HrafnaValkyrja/ultrasonic/RESUME.md

# RESUME (on ice 2026-10-08 ~22:55 ET, owner: "Put Ultrasonic on ice for today.")
Branch claude/clever-mayer-s5rxuw, all session work committed + pushed (last: b92e59c + this file).
Stashes: stash@{0} = pre-session K4 scratch/render outputs parked at freeze (restore with `git stash pop` if wanted); stash@{1} = ECR-0025 dome prep (#11); older WIP below that.

## State
- Four proofs PASS (docs/proof/). D17 = A+L BUILT (owner 22:3x): limiter on, ceiling at clamp, loud mode +12 (triple press in gesture B, HOLD2 in A, off at boot), battery saver off + knob toggle. fwsim all PASS 35 rows.
- Ceiling-test restore DONE (b92e59c): lim_c scales 1/ARR; clamp-hit check covers 200/400/800 kHz, 0 hits / 1.36M hops; plm 0 stale.
- Real-use runtime (cea34fe, 130 mAh, 0.85 usable): loud12 8.1 h dense / 23.7 h dusk. loud_shape (I-034, OFF) would give 6.4 h dense -> off unless bench likes it.
- Iterative Improvement rounds 1-6 judged; ledger docs/brainstorm/LEDGER.md (to I-040). TEAX exciter dropped (12.8 g).
- Bench day kit: docs/bench/bench-day-1.md + .png, k4-dummy-template.pdf, bench/rig/ scripts (sounddevice installed).

## NEXT (movable)
1. #7 cap derating as soon as ./inbox has the Samsung files (CL03A225MP3CRNC K4-P C9, CL03A105MO3NRNC K4-M C17).
2. Ask the taste WHY for D17 (prediction C missed; she chose A+L).
3. II round 7 (new question needed; all live rows are bench-gated).
4. NEXT.md refill per the work-selection rule (movable top 5 + Waiting).

## Waiting
- #7 cap files from her (ruled A: download now) -> ./inbox.
- #1 pen test + I-029 cardboard dummy (bench day) -> pod pick.
- #11 K1-thin button: 2-arc D4 pad re-route (~1 h, stash@{0}) only if K1t still needed after #1.
- #14 bench: masked threshold, car log, I-021/22/27/28, loud_shape A/B, BCE-1 Bl.
- #4 body measure (bench day), #8 order (after freeze, owner-only).
