HrafnaValkyrja/ultrasonic/NEXT.md

# NEXT 5 (ranked, movable today; 2026-10-08 22:20 ET)
1. VIS-D17: one dark PNG for #2 (A+L rec): A / A+L / A+X+L / B side by side: who hears what where, battery, mass. So her tap is by sight. ~30 min.
2. BENCH-ENV: add sounddevice (MIT) + libportaudio2 to tools/setup.sh; install; dry-run bench/rig/* live device listing. ~20 min.
3. PERF-GATE: hook sim/perf/port_meadow.py into the check suite as an opt-in slow check (run on fw changes), document in tools/README. ~30 min.
4. II round 6: radical/rabbit on louder-without-mass (pad geometry, coupling stiffness, drive waveform), mass ≤3 g as a hard rule. ~1 h.
5. Ledger/NEXT hygiene after each round; plm status clean.
Done tonight: PERF-PM c16ecf8, reconciled currents cea34fe, FW-HOLD2 f0f4abb, triple press b99bc4a, BENCH-RIG 95ce40d, ECR-0026 draft (not recommended) 6f96833/9ed8b1a, thermal row 8 5be4ca1, light-driver search 9ed8b1a (none fits).

## Waiting (blocked on her or the bench)
- #2 D17 ruling (Rec A+L) -> limiter + loud_db defaults, re-bless goldens.
- #1 pen test + I-029 cardboard dummy (bench day) -> pod pick.
- #11 K1-thin button: 2-arc D4 pad (~1 h, stash@{0}) only if K1t still needed after #1.
- #14 bench: masked threshold, car log, I-021/22/27/28, BCE-1 Bl (I-014).
- #4-#8 owner rulings (Rec blocks posted).
