HrafnaValkyrja/ultrasonic/docs/system/integration-map.md

# Integration map: the pod as one system (generated)

Generated by `hw/pod/system_map.py` from the SKiDL schematic (`hw/pod/gen.py`, package set mz2: design phase2 in `hw/current.yaml`) plus hand-kept facts. Do not edit by hand; regenerate. Part of the living big-picture set (`docs/system/README.md`). The block diagram is `docs/diagrams/schematic-rev1.png`.

**Use:** before proposing any change, walk it through every section. The required cross-check is at the end.

> 2026-10-07 (round 10, packet Q1): dims_r2.py / heel.py / dock_route.py / shell_r2.py / blade.py now take a NON-DEFAULT variant (ULTRASONIC_DESIGN=k1|k1p via hw/current.yaml blocks + hw/mech/dims.py). Phase-2 values are byte-identical (74-name dims snapshot; shell, heel, dock_route, board_in_pod, mass and interfaces outputs unchanged apart from new info fields). K1 facts: reg-pod-body.md Variants.
> 2026-10-08: hw/current.yaml gained a NON-DEFAULT `k4` block (shell_dims dims_k4.py, shell_out hw/mech/out/k4s; ULTRASONIC_DESIGN=k4) so sim/checks/pod_mass.py can select the K4 pod (mass, CoM, nose/ear split; sim/out/mech/pod_mass_k4.json). The default design (phase2) and every other tool are unchanged. 2026-10-08 (56cf4fd, N-K4-TOOLS): the `k4` block gained board_p / netlist_p / bom_p (P board) and shell_out now `hw/mech/out/k4s_lift` (K4_RELIEF=lift default, ECR-0024); board/netlist/bom keys point at K4 board M, the *_p keys at P; tools default via tools/current.py. 2026-10-08 shell: cell modelled sharp (bought part); cavity y0/z1 edge R0.25 + 0.2 relief in the strut fill clear the cell corner (shell_k4.py, dims_k4 CELL_RELIEF_R). 2026-10-08 (b2fa6ae): each design block gained `cell` (phase2 PH2_175, k4/k1t K1_130 = fw/variants.yaml cells); interfaces.py rails reads it and judges the clamped bridge peak (FWSIM-R64).

> 2026-10-07 round 11 (NON-DEFAULT, packet Q1/Q2): K1 duct options (K1_DUCT, sim/acoustics/duct_options.py), k1t (walls/lid 0.6), 0.6 wall coupon (hw/mech/coupon_wall06.py). Phase 2 unchanged (dims snapshot: only new names REAR_GAP; shell checks add info fields puck_feasible / puck_guide_bore / pocket_breaks_outer_face). Facts: reg-pod-body.md Variants.

## 1. Functions (what the pod must keep doing)

| Function | Blocks | Electrical chain (nets / pins) | Mechanical counterpart | Firmware counterpart |
|---|---|---|---|---|
| F1 Hear 20-85 kHz | MIC, MCU | MIC_VDD from PA5 (GPIO-switched supply, off in Off mode); MIC_CLK PB3 -> R2 33R -> U2; MIC_DATA U2 -> PB4 (ADF1) | mic U2 on B at board (2.65, 6.0), its 0.6 mm port at (1.88, 6.0) through the board (pod x 32.43); sealed duct ID 1.0 (reamed lid bore + D1.0 hole in the 0.25 VHB across the 0.30 F gap), hex-window mesh seat, on the pod centre line | ADF1 4 MHz PDM, algorithm A/B |
| F2 Process | MCU, CORE_SMPS, CLOCK | +3V0 -> VDD/VDDA/VDDSMPS; VLXSMPS -> L1 -> VDD11 (C8/C9); LSE Y1 on PC14/PC15 | - | MSI/PLL clocks, LSE (see A3-clock doc), Stop 2 / Off modes (D12) |
| F3 Drive the exciter | BRIDGE, ARM_PADS | TIM1 CH1/CH1N PA8/PA7 -> Q1 gates (GA_P/GA_N); CH3/CH3N PA10/PB15 -> Q2 (GB_P/GB_N; Rev F, ECR-0003); P sources on +3V0, N sources on BRIDGE_RTN; OUT_A/OUT_B -> J1/J2 | 2 litz wires up the NiTi arm (rear-side route, heel channel, strut bore) to the exciter in the pad | complementary PWM ~200 kHz with dead time; level/volume control |
| F4 Self-test exciter |Z| | SELFTEST, BRIDGE | BRIDGE_RTN -> R21 0.1R -> GND; BRIDGE_RTN -> R22 1k -> I_SENSE (C22 10n; R23 1M offset from +3V0, Phase 2 2026-10-07) -> PA6 ADC1_IN11 | - | tone sweep + synchronous detection over USB self-test (O15) |
| F5 Charge the cell | DOCK_USB, CHARGER, CELL_PADS | dock J3 DOCK_VBUS -> D4 -> VBUS -> U3 IN; U3 BAT -> VBAT -> J5 (cell +) / J4 shared GND (cell -) -> cell (PCM inside); config over I2C | magnetic 5-pin target in the belly bay, wired to J3/J4/J10/J11/J12; cell on 0.25 VHB in the tub, 1.4 mm under the board's B face | I2C charge current/JEITA setup, charge state |
| F6 Temperature-safe charge | CHARGER | TS: RT1 (on board) OR J9 cell NTC, never both -> U3 TS/MR; TS also -> PA2 | optional NTC taped on the cell, wire to J9 | firmware 20 C rule reads PA2 |
| F7 System power rail | CHARGER, LDO | U3 SYS -> VSYS -> U4 IN/EN -> LDO_OUT (C18) -> R20 0R -> +3V0 | - | - |
| F8 Battery level | VBAT_SENSE | VBAT -> R8 1M / R9 1M (C19) -> VBAT_SENSE -> PA4 (ADC4 works in Stop 2) | - | fuel estimate, low-battery cutoff |
| F9 Dock detect | DOCK_USB | VBUS -> R12/R13 100k/100k -> VBUS_SENSE -> PA1 | - | DFU entry, charge mode |
| F10 USB data / DFU | DOCK_USB, MCU | J10 D+ / J11 D- -> U6 ESD -> PA12/PA11 (USB FS); CC: J12 -> R18 5k1 Rd (CC not sensed since Rev F; ILIM by enumeration) | dock contacts D+/D-/CC | ROM DFU via boot stub, CDC self-test, firmware update |
| F11 Wake / button | UI, MCU | SW1 (3V0 <-> BTN) -> PA0 WKUP1, R10 2k2 pull-down (switch needs >= 1 mA) | SW1 on F at board (18.5, 6.0) in a 4.3 x 3.1 lid pocket under a printed puck (selective-fit length) + silicone skin, KMT0 travel 0.15 mm | wake from Off/Stop, on/off, modes |
| F12 Power LED (solid) | UI, ARM_PADS | VSYS -> R14 2k2 -> LED_A -> J7 -> wire -> LED in the pad housing -> wire -> J8 -> LED_K -> PB7 (open-drain, FT) | 2 more litz wires up the arm (4 total), LED on the tiny pad board (O8) | duty set from VBAT for steady brightness |
| F13 Charger link | CHARGER, MCU | I2C_SCL PB13, I2C_SDA PB14 (R15/R16 10k to 3V0); CHG_INT -> PA15 (internal pull-up; PB5 strapped to GND, ECR-0013 S1) | - | I2C2, charger IRQ |
| F14 Debug / flash / test | DEBUG, MCU | TP1 SWDIO PA13, TP2 SWCLK PA14, TP3 NRST, TP4 3V0, TP5 GND, TP6 VSYS; BOOT0 (PH3) R1 10k low (R1 pad = DFU tack point); TP7 PB6 USART1_TX printf; TP8/TP9/TP10 MDF mic fallback dots; PA10 pulled up by the ROM loader itself (bootloader USART1_RX) | TP1-TP6 bare 0.7 mm pads on F (TP1/2/4/5 at y 11.3, TP3 (9.3, 2.9), TP6 (24.0, 10.9)) in a VHB cut-out: reachable before the lid is bonded; snap-off test frame (O9) | SWD, ROM bootloader |
| F15 ESD at exposed contacts | DOCK_USB | D5 TPD1E10B06 at J3 DOCK_VBUS (bidirectional, 5.5 V working; D4 reverse block); D6 (same part) at J12 CC (Rev G); U6 on D+/D- | dock contacts are the only exposed metal | - |

## 2. Blocks (every placed or copper-only part)

| Block | Parts |
|---|---|
| MCU | U1 C1 C2 C3 C4 C5 C6 C7 C10 R1 |
| CORE_SMPS | L1 C8 C9 |
| CLOCK | Y1 C11 C12 |
| MIC | U2 R2 C13 |
| BRIDGE | Q1 Q2 R3 R4 R5 R6 C14 |
| SELFTEST | R21 R22 C22 |
| ARM_PADS | J1 J2 J7 J8 |
| DOCK_USB | J3 J4 J10 J11 J12 D4 D5 D6 U6 R18 R12 R13 C15 |
| CHARGER | U3 C16 C21 RT1 J9 R15 R16 |
| CELL_PADS | J5 |
| VBAT_SENSE | R8 R9 C19 |
| LDO | U4 C17 C18 R20 |
| UI | SW1 R10 R14 |
| DEBUG | TP1 TP2 TP3 TP4 TP5 TP6 TP7 TP8 TP9 TP10 |

## 3. Inter-block nets (the logical connections a domain change can break)

| Net | Blocks | Pins (ref.pin name) |
|---|---|---|
| +3V0 | BRIDGE, CHARGER, DEBUG, LDO, MCU, UI | U1.1 VBAT, U1.9 VDDA, U1.21 VDDSMPS, U1.25 VDD, U1.36 VDD, U1.48 VDD, C1.1 , C2.1 , C3.1 , C4.1 , C5.1 , C6.1 , C7.1 , Q1.4 S_P, R3.2 , Q2.4 S_P, R5.2 , C14.1 , R15.2 , R16.2 , R20.2 , SW1.1 1, SW1.2 2, TP4.1 1 |
| BRIDGE_RTN | BRIDGE, SELFTEST | Q1.1 S_N, Q2.1 S_N, R21.1 , R22.1  |
| BTN | MCU, UI | U1.10 PA0, SW1.3 3, SW1.4 4, R10.1  |
| CHG_INT | CHARGER, MCU | U1.38 PA15, U3.A1 /INT |
| DBG_TX | DEBUG, MCU | U1.42 PB6, TP7.1 1 |
| GA_N | BRIDGE, MCU | U1.17 PA7, Q1.2 G_N, R4.1  |
| GA_P | BRIDGE, MCU | U1.29 PA8, Q1.5 G_P, R3.1  |
| GB_N | BRIDGE, MCU | U1.28 PB15, Q2.2 G_N, R6.1  |
| GB_P | BRIDGE, MCU | U1.31 PA10, Q2.5 G_P, R5.1  |
| GND | all | 47 pins |
| I2C_SCL | CHARGER, MCU | U1.26 PB13, U3.B1 SCL, R15.1  |
| I2C_SDA | CHARGER, MCU | U1.27 PB14, U3.C1 SDA, R16.1  |
| I_SENSE | MCU, SELFTEST | U1.16 PA6, R22.2 , C22.1, R23.2 (Phase 2)  |
| LED_A | ARM_PADS, UI | R14.2 , J7.1 1 |
| LED_K | ARM_PADS, MCU | U1.43 PB7, J8.1 1 |
| LSE_IN | CLOCK, MCU | U1.3 PC14, Y1.1 1, C11.1  |
| LSE_OUT | CLOCK, MCU | U1.4 PC15, Y1.2 2, C12.1  |
| MDF_CCK | DEBUG, MCU | U1.45 PB8, TP8.1 1 |
| MDF_SDI | DEBUG, MCU | U1.19 PB1, TP9.1 1 |
| MIC_DATA | DEBUG, MCU, MIC | U1.40 PB4, U2.1 DATA, TP10.1 1 |
| MIC_VDD | MCU, MIC | U1.15 PA5, U2.5 VDD, C13.1  |
| N$2 | MCU, MIC | U1.39 PB3, R2.1  |
| NRST | DEBUG, MCU | U1.7 NRST, C10.1 , TP3.1 1 |
| OUT_A | ARM_PADS, BRIDGE | Q1.3 D_P, Q1.6 D_N, Q1.7 D_N, Q1.8 D_P, J1.1 1 |
| OUT_B | ARM_PADS, BRIDGE | Q2.3 D_P, Q2.6 D_N, Q2.7 D_N, Q2.8 D_P, J2.1 1 |
| SWCLK | DEBUG, MCU | U1.37 PA14, TP2.1 1 |
| SWDIO | DEBUG, MCU | U1.34 PA13, TP1.1 1 |
| TS | CHARGER, MCU | U1.12 PA2, U3.D1 TS/MR, J9.1 1, RT1.1  |
| USB_DM | DOCK_USB, MCU | U1.32 PA11, J11.1 1, U6.5 IO2 |
| USB_DP | DOCK_USB, MCU | U1.33 PA12, J10.1 1, U6.3 IO1 |
| VBAT | CELL_PADS, CHARGER, VBAT_SENSE | U3.C2 BAT, C16.1 , J5.1 1, R8.1  |
| VBAT_SENSE | MCU, VBAT_SENSE | U1.14 PA4, R8.2 , R9.1 , C19.1  |
| VBUS | CHARGER, DOCK_USB | D4.1 K, U3.A2 IN, C15.1 , R12.1  |
| VBUS_SENSE | DOCK_USB, MCU | U1.11 PA1, R12.2 , R13.1  |
| VDD11 | CORE_SMPS, MCU | U1.23 VDD11, U1.46 VDD11, L1.2 2, C8.1 , C9.1  |
| VLXSMPS | CORE_SMPS, MCU | U1.20 VLXSMPS, L1.1 1 |
| VSYS | CHARGER, DEBUG, LDO, UI | U3.B2 SYS, C21.1 , U4.3 EN, U4.4 IN, C17.1 , R14.1 , TP6.1 1 |

Nets inside one block only: CC, DOCK_VBUS, LDO_OUT, MIC_CLK, N$1

## 4. MCU pin map (STM32U575CIU6Q, QFN48)

| Pin | Name | Net | Other end |
|---|---|---|---|
| 1 | VBAT | +3V0 | (rail) |
| 3 | PC14 | LSE_IN | C11, Y1 |
| 4 | PC15 | LSE_OUT | C12, Y1 |
| 7 | NRST | NRST | C10, TP3 |
| 8 | VSSA | GND | (rail) |
| 9 | VDDA | +3V0 | (rail) |
| 10 | PA0 | BTN | R10, SW1 |
| 11 | PA1 | VBUS_SENSE | R12, R13 |
| 12 | PA2 | TS | J9, RT1, U3 |
| 14 | PA4 | VBAT_SENSE | C19, R8, R9 |
| 15 | PA5 | MIC_VDD | C13, U2 |
| 16 | PA6 | I_SENSE | C22, R22, R23 (Phase 2) |
| 17 | PA7 | GA_N | Q1, R4 |
| 19 | PB1 | MDF_SDI | TP9 |
| 20 | VLXSMPS | VLXSMPS | L1 |
| 21 | VDDSMPS | +3V0 | (rail) |
| 22 | VSSSMPS | GND | (rail) |
| 23 | VDD11 | VDD11 | C8, C9, L1 |
| 24 | VSS | GND | (rail) |
| 25 | VDD | +3V0 | (rail) |
| 26 | PB13 | I2C_SCL | R15, U3 |
| 27 | PB14 | I2C_SDA | R16, U3 |
| 28 | PB15 | GB_N | Q2, R6 |
| 29 | PA8 | GA_P | Q1, R3 |
| 31 | PA10 | GB_P | Q2, R5 |
| 32 | PA11 | USB_DM | J11, U6 |
| 33 | PA12 | USB_DP | J10, U6 |
| 34 | PA13 | SWDIO | TP1 |
| 35 | VSS | GND | (rail) |
| 36 | VDD | +3V0 | (rail) |
| 37 | PA14 | SWCLK | TP2 |
| 38 | PA15 | CHG_INT | U3 |
| 39 | PB3 | N$2 | R2 |
| 40 | PB4 | MIC_DATA | TP10, U2 |
| 41 | PB5 | GND | (rail) |
| 42 | PB6 | DBG_TX | TP7 |
| 43 | PB7 | LED_K | J8 |
| 44 | PH3 | N$1 | R1 |
| 45 | PB8 | MDF_CCK | TP8 |
| 46 | VDD11 | VDD11 | C8, C9, L1 |
| 47 | VSS | GND | (rail) |
| 48 | VDD | +3V0 | (rail) |
| 49 | VSS | GND | (rail) |

**Free MCU pins:** 2 PC13, 5 PH0, 6 PH1, 13 PA3, 18 PB0, 30 PA9

## 5. Rails and loads

| Rail | Source and loads |
|---|---|
| +3V0 | source: U4 LDO via R20 (TPS7A2030, 300 mA rated, ICL 360 mA min). Loads: MCU ~2.4-5.8 mA run; mic ~0.9-1.1 mA via PA5; bridge P sources: avg 0.6-1.7 mA at listening level but ~315 mA peaks at full drive (8R + 1.2R FETs) buffered by C14 22 uF; pull-ups R15/R16; SW1 contact (>= 1 mA while pressed). |
| VSYS | source: U3 SYS (power path: VBUS when docked, else VBAT through the BATFET). Loads: U4 LDO input, R14 LED (~0.35-0.75 mA), TP6. |
| VBAT | cell (Renata ICP501233PA-02 175 mAh, 3.0-4.2 V, PCM inside) <-> U3 BAT. Loads: R8/R9 divider (2 uA), C16. |
| VBUS | dock 5 V via D4 Schottky (reverse-dock block). Loads: U3 IN, R12/R13 sense, C15 (25 V). DOCK_VBUS side: D5 ESD. |
| VDD11 | MCU's own SMPS output via L1; MCU core only (D11 allows this switching regulator only). |
| BRIDGE_RTN | bridge N-FET sources -> R21 0.1R shunt -> GND (31 mV at 315 mA). |

## 6. Off-board interfaces

| Pads | Nets | Goes to |
|---|---|---|
| J1 / J2 | OUT_A / OUT_B | litz wire up the arm -> bone-conduction exciter RC-BC02 (8 or 12 ohm) in the pad |
| J7 / J8 | LED_A / LED_K | litz wire up the arm -> blue 0402 LED on the pad board |
| J3 / J4 / J10 / J11 / J12 | DOCK_VBUS / GND / USB_DP / USB_DM / CC | Xinyangze YZT0675 5-pin magnetic target in the belly bay (pogo YZP0048 on the cable) |
| J5 / J4 | VBAT / GND (J4 shared with dock GND, between J3 and J5) | cell leads (PCM inside the cell) |
| J9 | TS | optional NTC taped on the cell (then RT1 not fitted) |
| TP1-TP6 | SWDIO, SWCLK, NRST, +3V0, GND, VSYS | probe / pogo only |

## 7. Mechanical interfaces and keep-outs

- Board 30 x 12 x 0.8 mm (R1.0 corners), 4 layers (In1 GND plane, In2 +3V0 plane); every part on B except SW1 and bare TP1-TP6 on F; pod x 30.55-60.55 (hw/mech/dims_r2.py).
- F faces the lid (outside); B faces the cell. Height bands: B 1.4 (gap to the cell), F 0.30 (VHB gap to the lid), SW1 0.90 in its lid pocket.
- Mic MUST be on B with its D0.6 port hole on the board centre line y 6.0 (board 1.88 = pod 32.43): sealed duct ID 1.0 (reamed lid bore + VHB hole) onto it; same spot on both pods (O16-5).
- Switch MUST be on F at board (18.5, 6.0), inside the 4.3 x 3.1 lid pocket under the puck + skin: changing the button changes the lid.
- The board hangs from the lid on full-face VHB (3M 4914, 0.25 mm): nothing presses its long edges; coarse x-stop 0.25 mm at the front skirt; a stepped gauge pin through the bore registers it at bonding. F parts only in VHB cut-outs.
- Wire pads J* on B at the rear (board x 25-30); the arm wires reach them through the stowage gap behind the board (pod x 60.55-66.7) from the heel exit.
- Dock target sits in the belly bay (pod x 31.5-52.7), wired to J3/J4/J10/J11/J12; the whole belly is tub.
- Cell 35 x 12 x 5.3 mm on 0.25 VHB in the tub, 1.4 mm under the board's B face (tallest B part U2 1.08 mm).
- Arm: 4 litz wires (2 exciter + 2 LED) in shrink tube through heel channel D1.0 and strut bore D1.2: the wire count sets those bores.

## 8. Firmware dependencies

- TIM1 complementary PWM with dead time on PA8/PA7/PA9/PB0 (bridge).
- ADF1 (audio digital filter) on PB3 clock / PB4 data, 4 MHz PDM; PA5 is the mic's supply pin.
- ADC: PA4 VBAT (ADC4, works in Stop 2), PA1 VBUS sense, PA2 TS, PA6 bridge current (PA3 spare since Rev F).
- I2C2 on PB13/PB14 to the charger, EXTI on PA15 (CHG_INT).
- USB FS on PA11/PA12 (HSI48 + CRS), ROM DFU (the ROM loader pulls PA10 up itself, AN2606 Table 199); PB6 USART1_TX debug printf (TP7).
- Wake: PA0 = WKUP1 (button). LED: PB7 open-drain, PWM duty set from VBAT.
- Knob `loud_shape`/`loud_shape_k` (I-034 flat-top inside loud mode; default off, bit-identical; fw/core/dsp.c only, no new interface). Knobs `loud_db` (D17 loud mode, toggled by the HOLD2 gesture in option A only in practice; default off) and `hiz_idle` (bridge Hi-Z while squelched, I-027; default off): both default to legacy behaviour, bit-identical; touch F3 (drive, limiter, R64 clamp) and F11 (gestures). Tests `fw/test/test_loud.c`.
- SWD on PA13/PA14. Low-power modes Stop 2 / Off (D12).

## 9. Constraints and owner decisions

- Spec section 1 (MVP) is owner-locked.
- D11: switching regulators ONLY the MCU core SMPS; self-noise no louder than ambient.
- Power budget ~5-8.5 mA total (algorithm A) / 7.5-10.5 mA (B); runtime targets in spec.
- O8 power LED in the pad housing, solid. O9 rev 1 IS the prototype (test pads + snap-off frame).
- O12 magnetic USB dock (charge + DFU), IPX4 min / IPX5 preferred, outdoor wear in light rain, fast charge.
- O16: Renata 175 mAh cell, BQ25180 charger, pre-built magnetic connector, one board for both pods, no screws in the housing, IP68 switch.
- Owner rule for this study: one expensive component beats five half-price ones.

## 11. K4 two-board split (ECR-0020, proposed; NOT the current design until adopted)

Netlists (rev 3, area re-balance 2026-10-08): hw/pod/k4/gen.py -> pod_k4_M.net (23 placed parts), pod_k4_P.net (31); ERC 0 errors both. Board M (lower, mic on its outer face): U2/C13, charger U3 block, LDO U4 block (+R20), dock D4/D5/U6 + own gold pads J3/J4/J10/J11 + 2 magnets, SW1/R10, VBUS/VBAT dividers, RT1/J9, R14/J7/J8, J5, TP6, J20 BM28 receptacle. Board P (upper, over the mic): U1 + caps, Y1, L1/C7/C8/C9, R1/R2, R15/R16, bridge Q1/Q2 + shunt + C14, J1/J2, TP1-TP5/TP7-TP10, J21 BM28 plug. J12/R18/D6 and net CC are gone (ECR-0019).

| BM28 pin | Net | BM28 pin | Net | BM28 pin | Net |
|---|---|---|---|---|---|
| 1 | GND | 11 | USB_DP | 21 | GND |
| 2 | GND | 12 | GND | 22 | TS |
| 3 | MIC_CLK | 13 | USB_DM | 23 | I2C_SCL |
| 4 | GND | 14 | GND | 24 | GND |
| 5 | GND | 15 | GND | 25 | I2C_SDA |
| 6 | MIC_VDD | 16 | GND | 26 | VBUS_SENSE |
| 7 | MIC_DATA | 17 | +3V0 | 27 | CHG_INT |
| 8 | GND | 18 | +3V0 | 28 | VBAT_SENSE |
| 9 | GND | 19 | +3V0 | 29 | BTN |
| 10 | GND | 20 | GND | 30 | LED_K |

30 contacts = 16 signal/power + 14 GND (odd pins row A, even row B [T]). Parts: P plug C424570 BM28B0.6-30DP/2-0.35V(51), M receptacle C424571 BM28B0.6-30DS/2-0.35V(51), JLC 2026-10-08. Rating 0.3 A per signal contact [T, secondary source]; +3V0 (LDO on M to P) uses 3 contacts, the 315 mA bridge peaks are served by C14/C4/C7 on P. No VLXSMPS, VDD11 or bridge node crosses. Mated height 0.6 mm [T].

K4 dock (ECR-0021, proposed; docs/research/k4-dock.yaml option_A_design, 2026-10-08): J3 / J11 / J10 / J4 are 4 castellated ENIG pads (pitch 2.5) on the 0.8 mm tab of board M, seen through 4 belly windows, with 2 N52 D2.5 x 1.0 magnets in bossed belly pockets; they replace the YZT0675 target (J3/J4/J10/J11 wired). Head YZP0048-20048-04025-03 (C5126845). Nets and D4/D5/U6 unchanged; pod L 49.15 -> 50.65. Magnet pitch, polarity and stroke of the head are [T] until a sample is calipered.

## 10. Required cross-check for every proposed change

Every proposed change must state, and check against the sections above:
1. functions_affected: which F-rows change, and the NEW implementation chain for each (no function may be left without one; say explicitly if a function is dropped and that it needs an owner decision).
2. nets_changed: nets removed, added or re-driven; every remaining net still has exactly one driver and its loads.
3. pins: MCU pins freed and pins newly needed, with the alternate function used; no pin may end up with two jobs (check the pin map, including other domains' proposals).
4. rails: load change per rail (mA avg and peak) vs its source's rating; new rails need a source that respects D11.
5. offboard: changes to J pads, wire counts up the arm, dock contacts, cell wiring.
6. mechanical: which face each moved/added part is on, height band, keep-outs (mic port, switch/plunger, clamp bands, wire path), lid/shell features that must change.
7. firmware: peripherals/features added, removed or re-pinned.
8. depends_on / conflicts_with: other domains' changes this one needs or excludes.
