HrafnaValkyrja/ultrasonic/docs/brainstorm/LEDGER.md

# Brainstorm ledger (Iterative Improvement mode; process: ~/.claude-shared/board/howto/ITERATIVE-IMPROVEMENT.md)
Owner's plan 2026-10-08. One row per idea; the judge pass re-ranks each cycle and kills weak ones with a reason. Merit = evidence or a calculation + moves a spec metric meaningfully (or removes a hard build step or a risk) + a stated cost. Rows with merit go to the owner as a packet (recommendation first, "let's talk" option). Nothing is ordered; changes to the committed design go through her.

Tracks: D = deeper (main), R = rabbit trail (research swarm), X = step back (informed radical), B = blind designer (requirements brief only: BRIEF-blind.md).
Metrics (spec): thickness T, height H, length L, worn mass, vision clearance, runtime h, charge time, loudness margin (dB over ambient+12.5), mic noise margin dB, build difficulty (max step), build hours, part count, cost, risk.

| ID | Track | Idea | Metric moved (est.) | Evidence / calc | Cost + risk | Rank | Status | Judge note |
|---|---|---|---|---|---|---|---|---|
| I-001 | D | Playback limiter at the R64 clamp (lim_lookahead) + system sounds at 2-3 kHz (alert_hz); the limiter is the playback lever | alert margin +4.5 dB (quiet +6.1->+10.6, office -8.9->-4.4, street -28.9->-24.4; p05) | loudness.md before/after, fbfb38b | free; limiter raises max output past the -12 dBFS D17 ceiling: needs owner re-sign of D17 + golden re-bless | 1 | built, limiter OFF pending owner (D17) | - |
| I-002 | D | Pad stiffness / exciter resonance at 2-3 kHz | loudness +4-10 dB | loudness.md levers; needs E1/E2 | bench time, pad parts | - | bench day | - |
| I-003 | B | B-thin "single-deck slab": cell and board side by side in one layer, cell sets thickness | T 6.4 -> 4.3 mm (-2.1, -33%; sum 0.5+3.0+0.3+0.5 checks); mass ~6.5 g (checks) | B-thin calc; ALL part facts "from memory" [v]. Cell 1.575 cm3 x 83 = 131 mAh checks. L 58 mm from X=30 ends at 88: **fails the ~38 mm usable length by 20 mm**. In 38 mm the cell is ~21 mm = ~78 mAh -> worst day 6.4 h at their 11 mA (8.4 h only if the MCU error below is fixed): misses 8 h unless H grows (O34b). Error: MCU 30% x 96 MHz x 10 uA/MHz = 0.29 mA, not 2.9 mA | Thin win is real in principle; needs a 38 mm re-size (H up, cell shorter), 0.5 mm printed walls, 2 mm exciter unverified; rigid-flex vendor unverified | 3 | killed at 38 mm | D-slab38.md: T 4.3 x H 15.25 x L 38 leaves 13 mm for the cell = ~43 mAh, 3.1 h worst (8 h needs 113 mAh) and cannot source the 315 mA peak |
| I-004 | B+X | Single rigid-flex board (island + flex tail, cell as mandrel); removes BM28 pair, step 3/4 wires and step 9 cell-lead fold | build: -45 min of 5.6 h (~-13%), 2 hard steps gone, ~1 connector gap gone [A] | X-arch #3 and B-thin both reach it independently. JLC rigid-flex stack-up (min thickness, bend radius) NOT checked by either; 4L 0.8 mm is published only for rigid | rigid-flex 5-10x FR4 cost [A] (irrelevant, O19); redo layout (weeks), discards K4 DRC-0 work | 2 | killed at JLC | D-rigidflex.md aeb469c: JLC flex page 2026-10-08 "Rigid-flex PCBs are not yet supported"; flex 1/2/4L, bend 6-10x t; 0.6 mm fold only with a 1-layer tail. Reopen only if the owner accepts another fab |
| I-005 | B | One-chip charger+LDO+battery gauge link (TI BQ25155, 150 mA LDO) to cut parts | part count fewer lines | "[v]" from memory. Its 150 mA LDO is below the 208 mA bridge clamp and the 300 mA LDO figure in loudness.md | needs burst cap or second LDO; unverified datasheet | - | killed | D-onechip.md 9d50882: BQ25155 LDO 150 mA / BQ25120A 100 mA (+buck, D11) < ~219 mA needed; saves ~6 parts but +1.4 mm2; keep U3+U4 |
| I-006 | B | Loud exciter: tragus pad, 6 ohm coil, 0.34 A rms, "+15.5 dB over a 70 dBA street" | loudness claim +15.5 dB over street | Arithmetic internally consistent but drives 0.34 A rms (~0.48 A peak) vs the 208 mA R64 clamp (147 mA rms) and the LDO 300 mA limit; Bl 0.6 is [A]; 10 dB tragus bonus; thresholds [M] | no thickness gain (6.5 vs 6.4) | - | killed (as a loudness claim) | Re-run with the clamp: 78.2 dB-eq by its own method = -3.8 dB under its 82 target; with loudness.md thresholds, ~-4 to -15 dB. See loudness conflict in the judge log |
| I-007 | B | Piezo bender exciter with boost converter (fallback) | same force at ~1/10 current | needs 15-60 V boost | breaks D11 | - | killed (D11) unless owner relaxes D11 | R-exciter reached the same verdict |
| I-008 | B | Dose-based ceiling: <=80 dB-eq continuous, alerts <=88 dB-eq, <=0.5 s, <=60/h | safety policy, no metric | NIOSH 98-126 figures "from memory" [M]; ceiling is in unmeasured dB-eq (+-8 dB) | fw only | - | needs-evidence | Tie to D17; only meaningful after E1/E2 calibrate dB-eq |
| I-009 | X | Electronics into the arm run, front = mic-only flex tail, to fix the vision line | vision deficit 11.85 mm "eliminated" | Ignores the fixed rear end: K4 spans 17.65 to 67.5; the tail and everything else still need X >= 29.5, so the whole 49.85 mm must become ~38 mm. Moving mass back does not shorten it | 40 mm flex, PDM over 40 mm risk | - | killed (arithmetic) | Real need is 11.85 mm of length, not a different layout |
| I-010 | X | Tactile cue for SYSTEM events only (2-3 pulses 150-250 Hz); not a playback fix (owner: audio device, not an alert system) | alert audibility independent of masking (street/office) | Firmware only, 0 g, 0 BOM. Force at 180 Hz vs 300 Hz: 12 dB/oct x log2(300/180) = -8.8 dB (X-arch wrote -7); first-order only; face vibrotactile threshold is [A] | 20 min owner test; may buzz jaw/teeth; D1 promises quiet | 4 | built OFF (7183a29), marginal | skin displacement 4-8 um at 208 mA vs ~2-20 um threshold (from memory): -4 dB at 200 Hz, +2 at 250; system cue only, not playback |
| I-011 | X | One cell in the frame, 2 wires through both hinges | pod -4 mm, mass -3.5 g per pod | 4-5 g on the nose pads (X-arch's own kill test: >4.0 g kills) | links the pods | - | killed (brief hard no: no wires between sides, D2) | |
| I-012 | X | k1t 4L board (8.5 mm thick) behind the hinge in the arm | clears vision by 4.2 mm | 8.5 mm thick, worst on priority 1; depends on I-009 | - | - | killed | |
| I-013 | R | Dayton BCT-3 bone transducer (Bl 4.41) | +12.9 dB (20 log 4.41 and 4.41 x 0.208 = 0.917 N = 119.2 dB both check) | Web datasheet 2020-06-11; but 44x32 mm, 6.1 g | ~7x pod footprint | - | killed (size) | Gain is relative to an assumed Bl 1.0 that implies 106 dB at 208 mA, whereas the loudness model gives 94-97 dB: ratio valid, absolute not |
| I-014 | R | Measure RC-BC02 Bl, f0, force on the E1 rig; buy one Dayton BCE-1 (Bl unpublished) and ask Sonion/Goertek for Bl | retires the assumed Bl 1.0 that the loudness proof, B-loud and R-exciter all rest on; BCE-1 gain 0 to +6 dB, no basis | R-exciter table web-checked 2026-10-08 except BCE-1 price and the Tectonic Bl (secondary) | cheap, bench only; O21 means her call; BCE-1 is 7.8 mm vs T 6.4 | 2 | merit (risk removal) | Highest information per dollar; every loudness number moves with Bl |
| I-015 | R | Vision line from perimetry norms: Goldmann temporal ~90 deg -> line 11-21 mm from hinge (pod.py 29.5 is conservative) | vision clearance: K4 may need ~0-9 mm trim, not 11.85 | R-vision.md 21d7274 (sources dated; pupil-hinge unmeasured) | none; pen test confirms | 1 | merit (evidence) | Judge r3: desk sources fine, 5 mm margin spec-derived; pupil-hinge p unmeasured moves the line more than angle (R-vision says so). Median ~15 mm line, K4 passes only ~15-20%. Real action: 10-min pen test + side photo. |
| I-016 | D | K4-trim: re-lay boards to 13.75 long + gap trims (stock cell) -> X0 ~20.0; + custom 112.5 mAh 26.8 mm cell -> X0 ~24.2 (8.0 h worst, no margin) | vision clearance +2.4 / +6.6 mm; T 6.4 kept | D-k4trim.md 1f7935a | board re-place/re-route (serial heavy job); custom cell = supplier risk | 2 | merit (conditional on the pen test) | Judge r3: arithmetic checks (112.5 mAh = 8 h x 10.55 / 0.75; 4.19 mAh/mm; stack/gap saves sum 2.3 stock, 6.5 custom). Stock-only trim to ~20 is the free step; 24.2 custom has 1.95C and zero margin, so cap at ~21 (8.9 h, 1.75C). Do after pen test.  pen-test result picks: line <=12.6 K4 as is; <=15 K4-trim; <=19 K4-trim + custom cell; else K1t |
| I-017 | B | Blind thin38: one 0.8 mm board over an EEMB LP401230 cell (90 mAh, 4.3 x 12.5 x 31), fits X 29.5-67.5 | T 7.4 vs K1t 8.5 (-1.1), vision-clear | B-thin38.md 300cc45 (cell datasheet dated; mass est.; exciter avg 6 mA assumed) | 150 mA drive cap (-3 dB vs 208 mA); 8.4 h worst rests on the exciter avg; 2C rating only on the PCM-LD variant | - | killed (as specified); T idea kept as I-018 below | Judge r3: runtime fails on our real load. B-thin38 uses 8.6 mA (no LED, exciter 6 mA assumed); our model is 10.55 mA worst (9.8 full-chain + 0.75 LED, sub-power.md). 90 mAh x 0.75 / 10.55 = 6.4 h < 8 h (needs 112.5 mAh). 150 mA cap = 0.58C of our 260 mA clamp basis, -2.8 dB vs 208 mA, violates the 208 mA drive. Single 0.8 board has one face for MCU, bridge, charger, LDO, mic: unproven (Phase-2 and K4 are two-faced / two boards). |

## Judge log (newest first)
### Round 4 judge (2026-10-08)
- Read: R-dbpermA, B-r4-playback, d17-cost.md, sub-output.md, C3-output-stage.md, spec D6. Merit: I-019 (partly confirmed). Needs-evidence: I-020, I-021, I-022, I-027. Killed/dead: I-023, I-024, I-025, I-026.
- **Ternary PWM:** our bridge is 2-level AD at 200 kHz, not ternary; BD was rejected in v0.5 for dead-time distortion. Blind's ripple-mA claim mis-counts: recirculating ripple is heat, not battery mA; SPICE idle is 0.4-0.5 mA. It would cut current only if coil L is tiny (E1 unmeasured). Details in JUDGE-r4.md.
- **Owner packet:** TEAX plus ~+6 dB drive (I-019) with scene caveat; E1 measures L, Bl, f0 (I-014, also kills/keeps I-021/I-026/I-027).
- 2026-10-08 lead: FRAME CORRECTION (owner: "It's an audio device not an alert system."). Loudness is judged as playback listening headroom over day-to-day ambient, not alert margin. I-001 reworded (the limiter is the lever), I-010 demoted to system sounds.
### Round 3 judge (2026-10-08)
- Read: R-vision, D-k4trim, B-thin38, sub-power.md, loudness.md, variants.yaml, dims_k1.py. Merit: I-015, I-016 (conditional). Killed: I-017. New: I-018 (needs-evidence).
- **I-017 key question:** our K1t cannot take a ~90 mAh cell: worst load 10.55 mA (not 8.6) gives 6.4 h; 8 h needs 112.5 mAh. EEMB LP401230 is 90 mAh min at 54 mAh/cm3 (Renata 73), so a 112.5 mAh cell at 4.3 mm does not exist in 31 mm; stock 130 mAh is 4.5 thick. 90 mAh at 2C = 180 mA, clamp 144 mA (-3.2 dB), breaks 208 mA. Real thickness: ~7.6 (0.8 walls) / ~7.2 (0.6 walls), only if a one-face layout fits (unproven); today K1t 8.5.
- **Owner packet:** 1) pen test + side photo (picks K4 / K4-trim / K1t, I-015/I-016). 2) I-016 stock-only trim to ~20 mm is free of cell risk. 3) I-018 one-face floorplan check before any further thin push.
### Round 1 judge (2026-10-08)
- Read: B-thin, B-loud, X-arch, R-exciter, loudness.md. Merit: I-010, I-014. Needs-evidence: I-003, I-004, I-005, I-008. Killed: I-006, I-007, I-009, I-011, I-012, I-013.
- **Brief check:** usable length ~38 mm (X 29.5 to 67.5, rear end fixed). B-thin 58 mm and B-loud 48 mm both overrun it; X-arch #1 misses that K4 already ends at 67.5. Thickness: only B-thin (4.3 mm) moves it. B-loud gains nothing.
- **From memory, unverified:** every B-thin [v] part fact (STM32U3 10 uA/MHz, BQ25155, SPH0641 size, 8 mm exciter 2.0 mm tall); B-loud [M] ISO 389-3 / ISO 226 / NIOSH values; all X-arch [A].
- **Arithmetic errors:** B-thin MCU current 2.9 mA should be 0.29 mA; X-arch tactile -7 dB should be -8.8 dB; B-thin "0.56 W" is the sine average, not peak.
- **Loudness conflict (B-loud +15.5 dB over street vs loudness.md -24 dB):** B-loud never saw the 208 mA R64 clamp. Differing assumptions: (1) current 0.34 A rms vs 0.147 A rms (+7.3 dB); (2) touching-tragus +10 dB vs the measured front-of-tragus threshold at D1 (1-1.5 cm in front); (3) free Bl x I force (Bl 0.6) vs the bone.py pad/mass model, which gives 94.5 dB at clamp against 106 free (about -9 to -11 dB); (4) target: B-loud is stricter (82 dB vs 71.5, broadband vs dBA-11), which narrows the gap by ~10 dB. Net: (1)+(2)+(3) is roughly 26-28 dB of the ~29 dB nominal gap (my decomposition, +-5 dB). Both rest on assumed Bl; I-014 settles it.
- **Owner packet (top, recommendation first):** 1) I-010 tactile alert test (free, 20 min). 2) I-014 measure Bl on E1, plus one BCE-1 if she allows a bench buy. Best needs-evidence: I-003/I-004 thin single-deck rigid-flex, pending a 38 mm sizing and the JLC rigid-flex table.

| I-018 | D | K1t slimmed: single board over the Renata 130 mAh 4.5 mm cell, 0.6 walls, one-face IC layout | T ~7.2-7.6 vs 8.5 (my calc: 0.6+0.6+0.8+0.1+4.5+0.6 = 7.2; 0.8 walls 7.6) | judge calc from B-thin38 stack with the real cell; 130 mAh = 9.2 h, 260 mA pulse -> 208 mA drive kept | needs a one-face layout of ~30 parts in 36 x 13: unproven; H-bridge+charger+LDO heat | - | evidence in (D-k1t-oneface.md): board already one-face (B 228 of 246 mm2, only SW1+TP1-6 on F); 7.2 omitted 1.08 mic band + tapes; real floor 8.28 (8.08 with 0.6 board) | does-not-reach-7.6 | Mic bottom-port pins the B band; I-018 as stated fails, residual -0.2..-0.4 only || I-019 | R | Buy back drive with higher Bl: TEAX + ~+4.4 dB drive instead of +12 dB | runtime 6.2 -> ~8.5-9 h at equal loudness; dense mean 14.5 -> ~8.1 mA | R-dbpermA.md #1, calc from d17-cost table | TEAX bench buy (existing plan); limiter nonlinearity ignored | - | partly-confirmed, MASS KILL for TEAX14C02-8 (12.8 g/side vs ~1.2 g RC-BC02; R-light-driver.md, 2026-10-08) | Re-run (d17-cost.md, teax_drive_check.py): worst-call margin of TEAX+4.4 = current+12 in all scenes, median +4.4 dB; dense 7.8 mA/9.1 h holds, continuous 13.8 mA/6.4 h FAILS 8 h. 8 h dense: TEAX+6 (8.4 h); continuous: TEAX+0 only. |
| I-020 | R | Shift translated-programme energy to 2-4 kHz (lowest bone/tragus threshold) | ~8-12 dB per equal audibility, or x0.3-0.4 mean mA | RECALLED ISO 389-3 values, unverified | firmware mapping; needs primary check + bench | - | KILLED 2026-10-08: 95.6% energy already in 2.5k band; mastoid RETFL gain +0.2 dB (<2). Front-tragus +7.3 dB (2.5->4k, soft, SD 6-9) spun off as I-020b bench-only. D-i020-band.md | killed |
| I-021 | R | Exciter f0 into 2-3 kHz band | +6-9 dB in band, current falls at resonance | calc, assumed Q 2-3 | narrow, drifts with pad/skin; needs impedance sweep (I-014 rig) | - | needs-evidence | |
| I-022 | R | Tragus pad static force/area up | +2-4 dB (recalled) at 0 mA | RECALLED, unverified | comfort cap ~1-2 N; bench force sweep | - | needs-evidence | |
| I-023 | R | Programme-aware compression for mA | ~0.9 dB at best; compression raises mean current | calc | - | - | dead | no dB/mA; AGC on quiet calls only matters for the clamp |
| I-024 | R | Class-D / bridge / rail efficiency | 0 dB per battery mA (F = Bl x I, LDO 1:1); heat only; idle <1 mA | calc, identity in R-dbpermA.md | - | - | dead | does not move runtime-vs-loudness |
| I-025 | B | Blind r4 playback pod: 150 mAh cell in 3.2 x 14 x 27.5 mm, pod 4.9 x 27 x 30, 6.2 g, 12.7 h aged | T 4.9, 6.2 g, 12.7 h | B-r4-playback.md; every [R] unverified | cell energy density 450 Wh/L assumed vs 54-73 mAh/cm3 (about 200-270 Wh/L) found in r3 (EEMB/Renata): 150 mAh needs ~2-2.8 cm3, not 1.23; load 8.05 mA omits our 4.6-7.3 mA base; S=90 dB/W unsourced | - | killed (as specified) | 150 mAh at 1.23 cm3 is 2x denser than any stocked cell; kept as the S-gate idea (I-014 measures it) |
| I-026 | B | Ternary (3-level, BD) PWM 192 kHz + 33 uH per leg to remove idle ripple (claims 25-40 mA at idle) | idle ripple 3 mA vs 25-40 | spec D6/C3-output-stage.md: BD was v0.3/v0.4 and REJECTED in v0.5; bridge_spice.py idle bus current 0.49/0.42 mA (0.3/1.26 mH) | blind's ripple cost is wrong: ripple recirculates in L, battery pays only ~I_rms^2 R (tens of uW at 0.3 mH); only true if coil L is ~20 uH (unmeasured, E1). BD dead-time THD+N -10 dB at -40 dBFS (C3) | - | killed (reason: already analysed and rejected; our AD idle cost 0.4-0.5 mA) | Residual: if E1 measures L < ~0.1 mH, idle cost rises (20 uH: ~8 mA by calc) and a hybrid (BD only above -20 dBFS, or L in series) is worth a rerun. Kill test: E1 LCR meter L; deadtime_switching.py at that L |
| I-027 | B | Bridge Hi-Z (both legs off) when envelope under the noise gate | saves idle 0.4-0.5 mA (bridge_spice) in quiet scenes | calc; our idle number is from sim, not bench | firmware gate hysteresis; re-start click; AD zero-cross cancels dead-time error only while switching | - | SPICE ok: 0.42-0.49 mA at 1 tick, ~0.1-0.2 at 2 ticks; knob hiz_idle (default OFF) landed; D-hiz-idle.md | needs-evidence | Kill test: bench PWR-I12 idle bus current with real coil; if < 0.15 mA, drop |
| I-028 | R | Move playback centre 2.5 -> 4 kHz for ~+7 dB at tragus (Surendran, I-020b) | +7 dB claimed | R-tragus4k.md; Nishimura 2014/2015 (PubMed, doi 10.1002/lary.24485, 10.1016/j.anl.2014.08.001) | at 4 kHz open-ear CC is mostly airborne radiation (fit-dependent, bystander leak); numeric tables not retrieved; SD 6-9 dB; transducer response at 4 kHz unknown | - | needs-evidence | gain range 0 to +7 dB, not firm; bat-call naturalness ok (retune LO/mapping). Kill test: bench sweep at tragus force + canal mic, kill if < 2 dB net |
| I-029 | X | Slide whole K4 pod rearward over the ear helix: X0 17.65 -> 30.0, heel lead 12-15 mm litz | front X 30.0 vs 17.65; T 6.4, 9.2 h unchanged | calc from dims_k4 + R-vision; X-r5-vision.md | needs 79 mm straight arm (assumed); helix contact; CoG +20 % moment | - | needs-evidence | kill: cardboard block 30 min on her frame |
| I-030 | X | Cell forward, stack (P+M) behind the ear, mic flex tail | front X ~33; 9.2 h; nose -0.5 g | calc; X-r5-vision.md | flex PDM SNR, mastoid comfort, layout redo | - | needs-evidence | second to I-029 |
| I-031 | X | Single-face 1.8 mm stack under a 3.0 mm cell (overlap) | L 33.3, X0 33.3; but ~80 mAh = 7.5 mA budget vs 10.55 | calc, density assumed 65 mAh/cm3 | fails 8 h unless -29 % current | - | probably dead | kill by sub-power sum |
| I-032 | R | Tectonic TEAX09C005-8 as lighter exciter | Bl 1.1 -> +0.8 dB; 3.2 g, 26x13x6.5 | R-light-driver.md (datasheet snippet 2026-10-08) | size 26x13, mass over 3 g | - | dead | no gain over baseline |
| I-033 | R | Dayton BCE-1 (22x14x7.8, 2.3 g or 0.57 g) | Bl unpublished | R-light-driver.md | listings disagree; 1.8 mm thick | - | needs-evidence | weigh + measure on E1 |
| I-034 | R | Square/flat-top drive at the output tone (same peak current) | loudness +2.1 dB fundamental, perceived +2-3 | calc 4/pi; R-r6-nomass.md #1 | firmware; RMS current x1.41; 7.5 kHz bystander leak | - | offline 2026-10-08 D-r6-crest.md: k=2.5 +2.2 dB, mA x1.74, OOB 0.6 %: MERIT loud-toggle only; bench A/B still owed | kill: bench A/B < +1.5 dB or mA busts budget |
| I-035 | R | Move output band onto pad response peak (LO / log-map top), not boost | 0 to +7 dB | I-028 + R-r6-nomass.md #2; EQ cannot beat clamp for tones | firmware param; E1 sweep | - | bench day | kill: < 2 dB vs 2.5 kHz |
| I-036 | R | All-pass phase rotation + clip-filter crest reduction beyond limiter | 0-1.5 dB single call, 2-3 dB dense | R-r6-nomass.md #3; broadcast figures [recalled] | firmware, few biquads | - | KILLED 2026-10-08 D-r6-crest.md: fixed -0.2..-0.8 dB, corpus-tuned 0.0 dB | kill: offline corpus mean < 1 dB (no hardware) |
| I-037 | R | Stiffer/thinner pad contact (0.5 mm or A60 / option C foot) | +1 to +4 dB (unproven) | series-spring calc, E and tissue Z assumed | comfort vs O16(4) Sugru | - | bench day | kill: A/B spread < 1.5 dB |
| I-038 | R | Preload 1 -> ~2 N via arm set | +1 to +3 dB | Hosoi/Nishimura force effect [recalled] | comfort, creep | - | bench day | kill: < 1 dB per 0.5 N or discomfort |
| I-039 | R | Aim pad face at concha / canal (open-ear airborne path) | 0 to +3 dB | Nishimura 2015 PMID 25199744 | printed tilt variants, fit variation | - | bench day | kill: < 1 dB or sign flips across ears |
| I-040 | R | Stiffen/thicken cup back wall | 0 to +1 dB | R-r6-nomass.md #7 | 0 g | - | parked | only if E1 shows cup mode < 6 kHz |
