HrafnaValkyrja/ultrasonic/docs/brainstorm/R-r6-nomass.md

# R-r6-nomass: louder playback with the CURRENT pad driver, zero added mass (rabbit trail, II round 6, 2026-10-08)

Hard rule: ear-side mass <= RC-BC02 pad (1.2 g `[Low]`) + 0.5 g; exciter swaps dead (R-light-driver.md, 9ed8b1a). No WebSearch run (budget); numbers are repo-derived or **[recalled]** (unverified, treat as order of magnitude). Baseline: bridge +-3.0 V, 208 mA FWSIM-R64 clamp, look-ahead limiter (I-001), RC-BC02 Bl ~1.0 N/A ASSUMED (E1 unmeasured). Gains are at the SAME peak current unless stated. All bench claims close on E1 (swept sine through the real pod, force + ear-canal mic).

## Ranked (firmware first)
| # | Idea | dB gain (est.) | Cost | Kill test |
|---|---|---|---|---|
| 1 | **Square / flat-top drive (soft-clip to trapezoid) at the output tone.** At equal PEAK current a square's fundamental is 4/pi = **+2.1 dB** over a sine (calc); 3rd harmonic is -9.5 dB at 3f (7.5 kHz at 2.5 kHz), which the ear hears even better, so perceived gain ~ +2 to +3 dB. Bridge is already PWM, so a square is the native waveform. | +2 to +3 | firmware only (waveform shaper after the limiter). RMS current x1.41 vs sine, so the battery term at loud use rises up to 2x; THD irrelevant for an alert/translated-call channel but 7.5 kHz leaks to bystanders (T6 self-noise rule concerns idle, not playback). | Bench: same peak, A/B sine vs trapezoid, ear-canal mic dB(A) and battery mA at 2.5 kHz. Kill if < +1.5 dB or mA x1.8 busts the 8 h budget in loud mode (loud mode is toggle-only, so budget impact is usage-weighted). |
| 2 | **Move the output band onto the pad's response peak** (heterodyne LO / log-map top, free parameter; merges with I-028 4 kHz and I-002). Pre-emphasis proper cannot beat the clamp: a tonal output is already at clamp, so EQ only helps if the band is wider than the clamp-limited region. Choose frequency, not boost. | 0 to +7 (I-028 range; resonance of RC-BC02 unknown) | firmware, one parameter; naturalness tested on the Shokz bench | E1 sweep: net ear-canal level at 1/2/2.5/3/4/5 kHz; kill if best band beats 2.5 kHz by < 2 dB. |
| 3 | **Crest-factor reduction beyond the limiter: all-pass (phase-rotation) + clip-and-filter.** For multi-component or overlapping calls (harmonics, several bats) a cascade of first/second-order all-passes lowers peak with magnitude untouched; broadcast speech processors report 2-4 dB lower crest [recalled]. Single chirps/sines are already ~3 dB crest, so gain ~0 there; realistic **0 to +1.5 dB (single call), +2 to +3 dB (dense passages)**. Needs look-ahead limiter to drop gain by less (peak down C dB => RMS up C dB at fixed clamp). | 0 to +3 | firmware, 2-4 biquads per ear (M33 FPU, a few hundred cycles per block; sub-processing budget check); latency 0 added (IIR). | Offline first (no hardware): run translated-call test corpus through all-pass+limiter, measure RMS at equal peak. Kill if mean < 1 dB. Cheap, do before hardware. |
| 4 | **Stiffer / thinner contact in series with the tissue.** Current CAD: 1 mm silicone disc Shore A 30-40, Ø8, ~50 mm2: k = E A / t, E ~ 1.2 MPa **[recalled for A35]** => ~6e4 N/m, mechanical impedance k/w ~ 3.8 N s/m at 2.5 kHz. Tragus skin + cartilage impedance is not measured here (guess ~ 5-20 N s/m); if the pad is the same order, series loss is several dB. Halving thickness (0.5 mm) or Shore A 60 (option C rigid 6x8x0.9 foot on 0.1 mm tape, reg-pad.md) recovers **+1 to +4 dB (UNPROVEN)**. Conflicts with owner O16(4) (Sugru, 100-150 mm2, comfort). | +1 to +4 | 0 g; comfort risk; part swap in a minute (pad.md option C) | E1: A/B three contacts at equal force, ear-canal mic. Kill if spread < 1.5 dB; then keep Sugru for comfort. |
| 5 | **Preload raised from 1 N to ~1.5-2 N (arm spring set).** Cartilage-conduction output rises with contact force, largest at low f (Hosoi/Nishimura group, force-effect papers [recalled, not retrieved]); at 2.5 kHz perhaps +1 to +3 dB per doubling. D1 floor is >= 1 N; upper bound is comfort over hours. | +1 to +3 | 0 g; NiTi arm force setting (bend) only; comfort/pressure-sore risk, warm-skin creep | Force gauge sweep 0.5-3 N with ear mic at 2.5 kHz plus 30 min wear at the chosen N. Kill if < 1 dB per 0.5 N or discomfort > mild. |
| 6 | **Open-ear air path: tilt/shape the pad face toward the concha opening; keep the cup back vented/closed per the dipole rule.** Nishimura 2015 (Auris Nasus Larynx 42:15, PMID 25199744): at 4 kHz open ear, airborne radiation of the transducer dominates; ear-canal resonance near 2.7 kHz (Shaw, 1974 **[recalled]**, +10 to +17 dB) already helps. Pad geometry that aims the radiating face at the canal may add. | 0 to +3 | 0 g (shape of the printed cup face); needs ear-shape variation test | Two cup tilts (0 and ~20 deg) printed; ear mic at 2.5 and 4 kHz. Kill if < 1 dB or pinna variation (3 test subjects incl. owner) flips the sign. |
| 7 | **Back-of-cup stiffness / damping (pad board clamp on the exciter back).** Mass loading of an inertial exciter: force into the skin is Bl I; a stiffer cap raises first flexural mode of the 0.6 mm resin wall (est. > 8 kHz, not a 2.5 kHz issue). Likely **0 to +1 dB**. | 0 to +1 | 0 g | Skip until E1 shows a cup resonance below 6 kHz; then thicken wall 0.6 -> 0.8 mm. |

## Stack and recommendation
Stacking is not additive in practice: 1 (square) and 3 (crest) fight over the same peak headroom (use whichever wins offline; square already has crest 0 dB). Plausible no-mass total **+3 to +6 dB**: 1 or 3 (+2) + 2 (frequency, 0 to +4) + 4/5 (+1 to +3). For reference, I-001 limiter already gave +4.5 dB, alert margin office -4.4 dB, so this may not close the street gap (-24 dB) alone; physics-wise it narrows it.
**Do first:** (3) offline corpus test (hours, no hardware), (1) as an A/B knob `drive_shape` in knobs.yaml. **Bench (E1 day):** 2, 4, 5, 6 on one session. Neither needs any ear mass.
Open: RC-BC02 Bl and f0 unknown (E1); tissue impedance guessed; no primary source retrieved this run for contact-force/stiffness effects, so rows 4-5 rest on [recalled] values.

## Sources
Nishimura et al., Auris Nasus Larynx 2015;42(1):15-9 (PMID 25199744) via R-tragus4k.md (retrieved 2026-10-08). Repo: reg-pad.md (contact, D1), sub-output.md (clamp, loud_db), loudness.md (I-001), R-light-driver.md. 4/pi square-wave fundamental: Fourier series (calc).
