HrafnaValkyrja/ultrasonic/docs/system/reg-pod-body.md

# Pod body: tub, lid, retention, duct, switch pocket, dock bay
Rev MZ-2 2026-10-07: body rewritten to the Phase-2 shell (`hw/current.yaml`, ECR-0018): seam at the board's B face, board hung from the lid on per-pad-cut VHB, sealed D1.0 duct + gauge pin, SW1 pocket + selective-fit puck, no ribs/foam; Rev F/G shell moved to the reference section.
Status: Phase-2 shell CAD `hw/mech/shell_r2.py` (constants `hw/mech/dims_r2.py`), last rebuilt for commit c348661 (2026-10-07 07:30): `hw/mech/out/r2/checks.json` every clash 0 mm³, tub/lid/puck each 1 valid solid. Not printed, not owner-reviewed (O25: review in 1-2 weeks). Updated 2026-10-07.
· Source of truth: `hw/mech/dims_r2.py` (every number), `hw/mech/shell_r2.py` (solids, checks), `hw/mech/notes/shell_r2.md` (decisions D1-D8, retention options, assembly), `hw/mech/blade.py` (rail, adapter), `hw/mech/heel.py` (heel unioned into the tub, [reg-arm](reg-arm.md)), `docs/build/tolerances.md` (Rev-1 fits; no Phase-2 rows yet, issue 18)
· Owner decisions: O5, O10, O12(b), O16(3)(5)(6)(7), O17, O19, O24 (sealed duct D1.0 + locating), O25/O26 (Phase 2, Claude lays out), O27 (thin > short > long) · ECR-0001 (`frame.py`/`pod.py` constants) implemented 2026-10-07, awaiting owner review · Open ECRs: ECR-0006 (weighted dummy pair, wear + joint flex), ECR-0018 (Phase 2, approved, implementation in progress)

## Purpose
- Holds and protects the board, the cell and the dock target, **without screws** (O16-6).
- Mechanical half of: **F1** sealed mic duct in the lid; **F11** SW1 pocket, puck and skin; **F5/F9/F10/F15** dock window in the belly; **F3/F12** stowage zone + heel + wire channel (`integration-map.md` §1).
- Mounts to the glasses through a removable frame adapter (spec §8; adapter work deferred, O26).
- Two-stage build (O10): taped test build, bonded final build that can be cut open. Sealing IPX4 min, IPX5 preferred (O12b).
- Exterior: "Spine" top (O17), carried over from r1 onto the Phase-2 top.

## Big picture
Renders (build outputs, gitignored; `shell_r2.py` writes them): `hw/mech/out/r2/section.png` (y-z section through mic and SW1), `hw/mech/out/r2/plan.png` (x-z plan through the lid: board, mic, SW1 pocket, dock, stowage, seam keys). No 3D render dump of r2 yet (issue 9).

1. **Two prints + a puck.** The **tub** is everything below the seam y 12.1 (the board's B face) **plus the whole belly** (x < 55.0, z < −8.9), so the dock window lies in one part. It carries the heel, the dovetail rail and the strut relief. The **lid** is a shallow cap y 12.1-14.7: skirt walls round the board, lid face 0.8, armour plate 0.7, spine top. Printed **puck** in the SW1 bore (5 lengths, selective fit).
2. **Stack, inside out (pod y):** wall 4.3-5.1 → cell VHB gap 0.3 → cell 5.4-10.7 → **B gap 1.4** (B parts, tallest U2 1.08) → board 12.1-12.9 → **F gap 0.30 = VHB 4914 0.25 + 0.05** → lid face 13.2-14.0 → plate 14.0-14.7. Thickness T 10.4 (dims_r2.py, 2026-10-07).
3. **Retention:** the board **hangs from the lid** on full-face 3M VHB 4914, die-cut at the duct (D1.0), the SW1 pocket (4.3 × 3.1) and one 1.8 mm square per F test pad (TP1-TP6): 91 % of the tape outline bonded, ~314 mm² (interfaces.py [clamp-bands] PASS; checks.json `vhb_area_mm2` 313.9; 2026-10-07). Nothing touches the board's long edges (0.45 free each side). Lifting the lid lifts the board on its wires and exposes the cell.
4. **Locating:** the lid's D1.0 duct bore is the datum. While the VHB grabs, a stepped gauge pin (D0.98 body in the bore / D0.50 tip in the board's D0.6 hole) registers tape and board to the bore; then it is pulled. The front skirt wall is a coarse x-stop 0.25 ahead of the board and never touches within tolerance (so it can't fight the pin).
5. **Seam:** tub tongue 0.35 × 0.5 / lid groove +0.05 on the straight wall runs, stopped 1.4 mm short of every convex corner; a 0.35 × 0.35 key on the belly step. Cut line: 0.2 × 0.4 tub-only rebate on the y 12.1 runs (0.3 before 2026-10-07); the belly step has none (issue 12).
6. **Rear:** stowage zone behind the board (pod x 60.55-66.7, cell top → lid face) + 1.1 mm behind the cell: 277 mm³ for the 12 wire loops (need 107-142).

## Elements
```yaml
# pod mm: x rearward, y outward, z up (right pod = CAD; left = mirror). src hw/mech/dims_r2.py unless noted; 2026-10-07
outer_body: {x: [29.5, 67.5], y: [4.3, 14.0], plate_to: 14.7, z: [-9.7, 4.8], chamfer: 1.0, wall: 0.8}
belly: {x: [29.5, 55.0], z_to: -11.75, depth: 2.05, why: "flat-tail dock target 2.8 + tails 0.85 - (wall + 0.8 under-cell slack)"}
cavity: {x: [30.3, 66.7], y: [5.1, 13.2], z: [-8.9, 4.0]}
bay: {x: [30.3, 54.2], z: [-10.95, -8.9]}
tub: "outer_body & (y < 12.1, + belly x < 55 / z < -8.9) + blade.rail + heel.heel_add - cavity - heel.heel_cut - dock window - strut relief + tongue + plate below the belly step - seam rebate (shell_r2.py tub())"
lid: "outer_body - tub region + plate - cavity - groove - duct bore - hex window - SW1 pocket/bore/skin recess + spine top (shell_r2.py lid_base(), top_concept())"
seam: {y: 12.1, tongue: "0.35 x 0.5, groove clearance 0.05, stops 1.4 short of convex corners (1 mm chamfer leaves 0.42 wall)", belly_step_key: "0.35 high (the hanging board's lower edge sweeps past it, 0.10 clear)", rebate: "0.2 x 0.4 (was 0.3 until 2026-10-07), tub only, y 12.1 runs; belly step witness groove 0.1 x 0.4"}
board_pocket: {board: "30 x 12 x 0.8 R1.0 at x 30.55-60.55, y 12.1-12.9, z -8.45..3.55", x_stop: 0.25, long_edges_free: 0.45, rear_to_wall: 6.15}
vhb: {part: "3M VHB 4914 (0.25 mm acrylic foam tape)", outline: "board inset 0.2", cut_outs: ["D1.0 duct", "4.3 x 3.1 SW1 pocket", "1.8 mm square per TP1-TP6 (TP_PAD_D 1.0 [A] + 0.4 margin; real TP copper D0.7)"], bonded: "~314 mm2, 91 % (interfaces.py clamp-bands PASS)"}
mic_duct: {axis: "pod (32.43, z -2.45) = board (1.88, 6.0), read live from the routed board (dims_r2.board_mic)", bore: "D1.0, printed undersize + reamed, lid face y 13.2 -> hex floor 13.9 (0.7)", vhb_hole: "D1.0 across the 0.30 F gap", board_hole: "NPTH D0.6", length: "1.0 total (notes/shell_r2.md D4)", hex_window: "R1.9 x 0.8 deep from the plate top = mesh seat (mesh part TBD)"}
gauge_pin: {body: 0.98, tip: 0.50, runout: 0.02, material: "turned brass [A]", state: "to source or turn (issue 16)"}
sw1_pocket: {centre: "pod (49.05, -2.45) = board (18.5, 6.0)", pocket: "4.3 x 3.1, ceiling y 13.8 (0.25 over SW1 nominal)", bore: 2.6, puck: "D2.3 + nub D1.0 x 0.10", skin: "silicone D4.6 x 0.25 recess, floor y 14.45, flush with the plate", puck_kit: [0.73, 0.78, 0.83, 0.88, 0.93]}
dock: {part: "Xinyangze YZT0675 (5-pin magnetic pogo target, 21.2 x 6.86 x 2.8, LCSC C5126848)", box: "x 31.5-52.7, y 5.72-12.58, z -11.75..-8.95", window: "+0.1 per side through the belly floor", tails: "flat, in the 0.8 under-cell slack"}
usb_c_keepout: "not carried into shell_r2 (R-DOCK-BODY)"
cell_bed: {cell: "Renata ICP501233PA-02 envelope x 30.6-65.6, y 5.4-10.7, z -8.1..3.9", tape: "VHB 4914 0.25 in the 0.3 gap to the inner wall"}
strut_relief: "identical to r1 (same Z0, CAV y0/z0): fill 1.0 legs in the inner-bottom rear corner x 62-66.7; outside cut to y + z = -3.65"
rail_adapter: "blade.rail(zc=-2.45) in shell_r2; since ECR-0001 (2026-10-07) blade.rail()/blade.adapter() default to pod.POD_ZC = the current body centre (-2.45), so the modelled adapter slot now mates the r2 rail (it sat 0.45 mm high before). The adapter itself is still redesigned with the two-frame adapter work (O26, deferred); shell_r1 pins its as-built -2.0 (RAIL_ZC)"
spine_top: "shell_r1.concept_spine moved -1.4 y / -0.7 z onto the r2 top, unioned into the lid (159.6 mm3)"
```

## Interfaces
```yaml
- to: reg-board
  crosses: "board 30 x 12 x 0.8 at x 30.55-60.55, y 12.1-12.9, z -8.45..3.55; F face on VHB; B band 1.4 (tallest U2 1.08, margin 0.32); F band 0.30 (SW1 pocket 0.90, SW1 0.65 margin 0.25); F parts only in VHB cut-outs; x-stop 0.25"
  invariant: "no F part outside a cut-out; nothing on the long edges; interfaces.py outline/inside/heights/clamp-bands PASS 2026-10-07"
  rel: R-BOARD-BODY
- to: sub-audio-in
  crosses: "duct bore D1.0 + VHB hole D1.0 over the board's D0.6 NPTH at board (1.88, 6.0) = pod 32.43"
  invariant: "nominal offset 0.000 (interfaces.py mic-port PASS); worst 0.155 <= 0.20 with the gauge pin, 0.86 FAIL walls-only (checks.json duct)"
  rel: R-AUDIO-BODY
- to: sub-ui
  crosses: "SW1 pocket 4.3 x 3.1 + D2.6 bore + puck + skin over board (18.5, 6.0) = pod 49.05"
  invariant: "selective fit puck top -> skin 0.005..0.135 (PASS); fixed puck worst -0.198 pre-presses (FAIL, why the kit exists); interfaces.py switch WARN: lateral stack 0.20 vs 0.15 limit"
  rel: R-UI-BODY
- to: sub-dock-usb
  crosses: "DOCK box + window in the tub belly, BAY; 5 dock wires target -> J3/J4/J10/J11/J12 (B, board x 25-29)"
  invariant: "wire route under the cell (0.8) undesigned (issue 7)"
  rel: R-DOCK-BODY
- to: sub-power
  crosses: "CELL envelope on 0.25 VHB in the 0.3 gap; 1.4 B gap to the hanging board"
  invariant: "B parts never touch the cell (checks.json clash parts_B/cell 0)"
  rel: R-PWR-BODY
- to: reg-arm
  crosses: "heel unioned into the tub (heel.heel_add/heel_cut, unchanged); channel exit (66.20, 5.15, -5.50) necked D0.8 into the 1.1 gap behind the cell (2026-10-07); arm bundle on the rear wall, then the upper stowage; strut relief"
  invariant: "exit hole x 65.80-66.60 behind the cell end 65.6 (rim-corner 0.36), outer wall 0.60; arm wires keep >= 0.39 to the cell, 0.68 to the rear seam (heel checks.json wire_route)"
  rel: R-BODY-ARM
- to: physical
  crosses: "frame axes; frame.py/pod.py pod names derived from dims_r2.py (frame.pod_facts(), ECR-0001); assembly order"
  invariant: "interfaces.py frame PASS: 10 of 10 shared facts agree (2026-10-07)"
  rel: R-PHYS-FRAME
- to: sub-debug-test
  crosses: "TP1-TP6 bare pads on F under the VHB cut-outs, facing the lid 0.30 away"
  invariant: "reachable only before the lid bond (checks.json F_face_pads reachable_assembled false); after it SWD = peel the board off the lid (issue 15)"
- to: reg-pad
  crosses: "no direct contact: pad pose via the arm (frame.pad_pose)"
- to: spec
  crosses: "O10, O12b, O16-6, O17, O24 (duct), O27 (thin first)"
  rel: R-SPEC-BODY
```

## Constraints
- **O16-6** no screws in the housing (cup screw and NiTi set screws allowed). **O10** taped test build, bonded cut-openable final build.
- **O12b** IPX4 min, IPX5 preferred. **O16-3** pre-built magnetic connector. **O16-7** IP68 switch (KMT022), not a printed flexure.
- **O16-5** one board for both pods: mic and SW1 on the board centre line y 6.0 = pod z −2.45; left shell = mirror.
- **O24(1)** sealed straight duct ID 1.0 between lid bore and board hole + a board locating feature (x-stop + gauge pin here) + firmware EQ notch (target moved to ~63 kHz, sub-audio-in).
- **O27** thin first, then short, then long: T 10.4 (Rev F 11.8), H 14.5 (Rev F 15.2), L 38.0 unchanged.
- **O19** serviceability: cell swap must not destroy the board bond (lid lifts the board; met by D1 seam). **R20/R24** via ECR-0006.
- **Spec §8:** port opens over the board hole, no gasket cavity, thin mesh never foam; nothing visible with the eyes straight ahead (pod x ≥ 29.5).
- **Resin** (`tolerances.md`, `hardware.md` §5): holes < ~0.8 mm may close, recesses < 0.4 may fuse; ream critical holes.
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
