HrafnaValkyrja/ultrasonic/docs/system/vcrm.md

# Requirement to verification matrix (VCRM)
Status: second version after an adversarial test, 2026-10-02 · Source of truth: [`vcrm.yaml`](vcrm.yaml) (hand-kept), checked by `python3 tools/checks/vcrm.py` · Requirements: [`docs/spec.md`](../spec.md), which always wins · Owner decisions: O18 (stage C before hardware), O19, O20
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
