HrafnaValkyrja/ultrasonic/.pcba-workflow/k4-release/pin1_expected.png

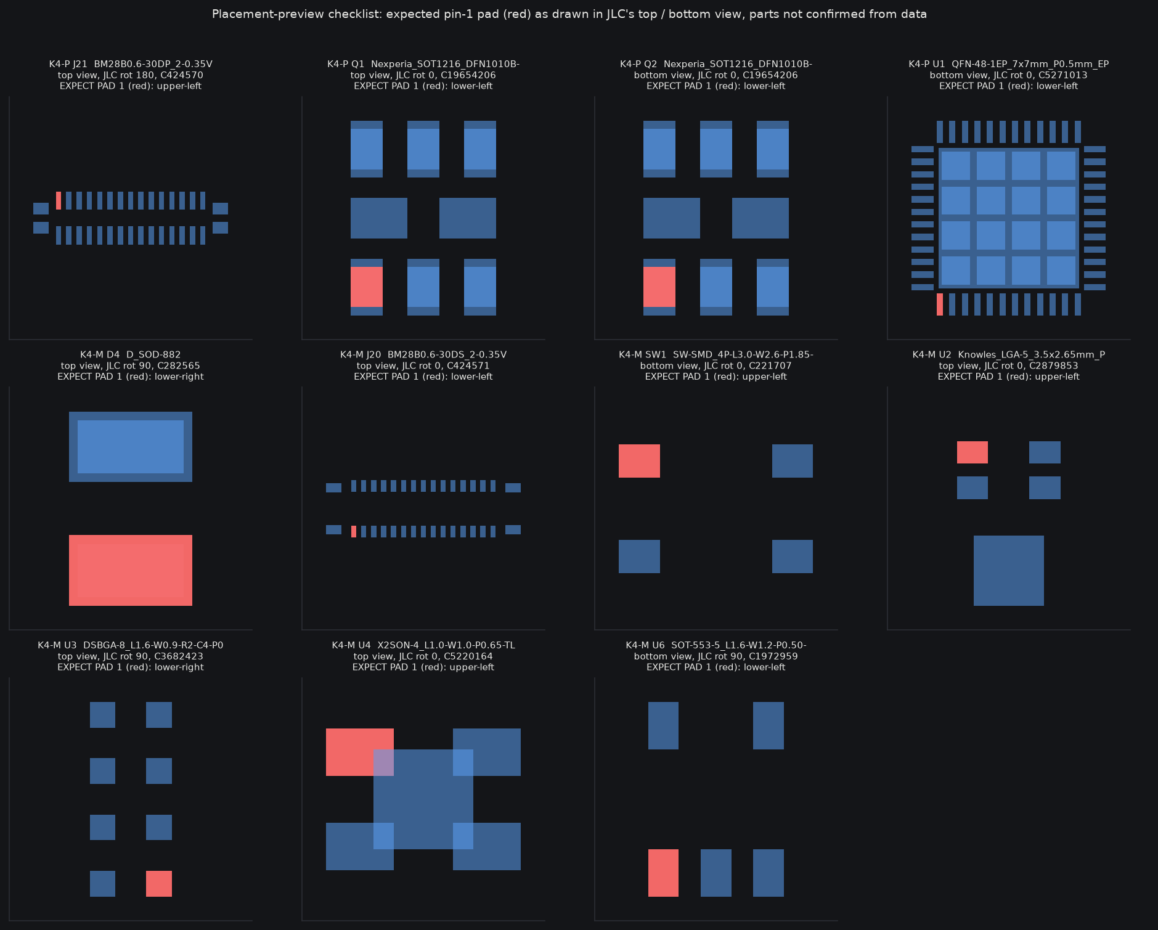
.pcba-workflow/k4-release/pin1_expected.png
