HrafnaValkyrja/ultrasonic/.pcba-workflow/r2-release/pin1_expected.png

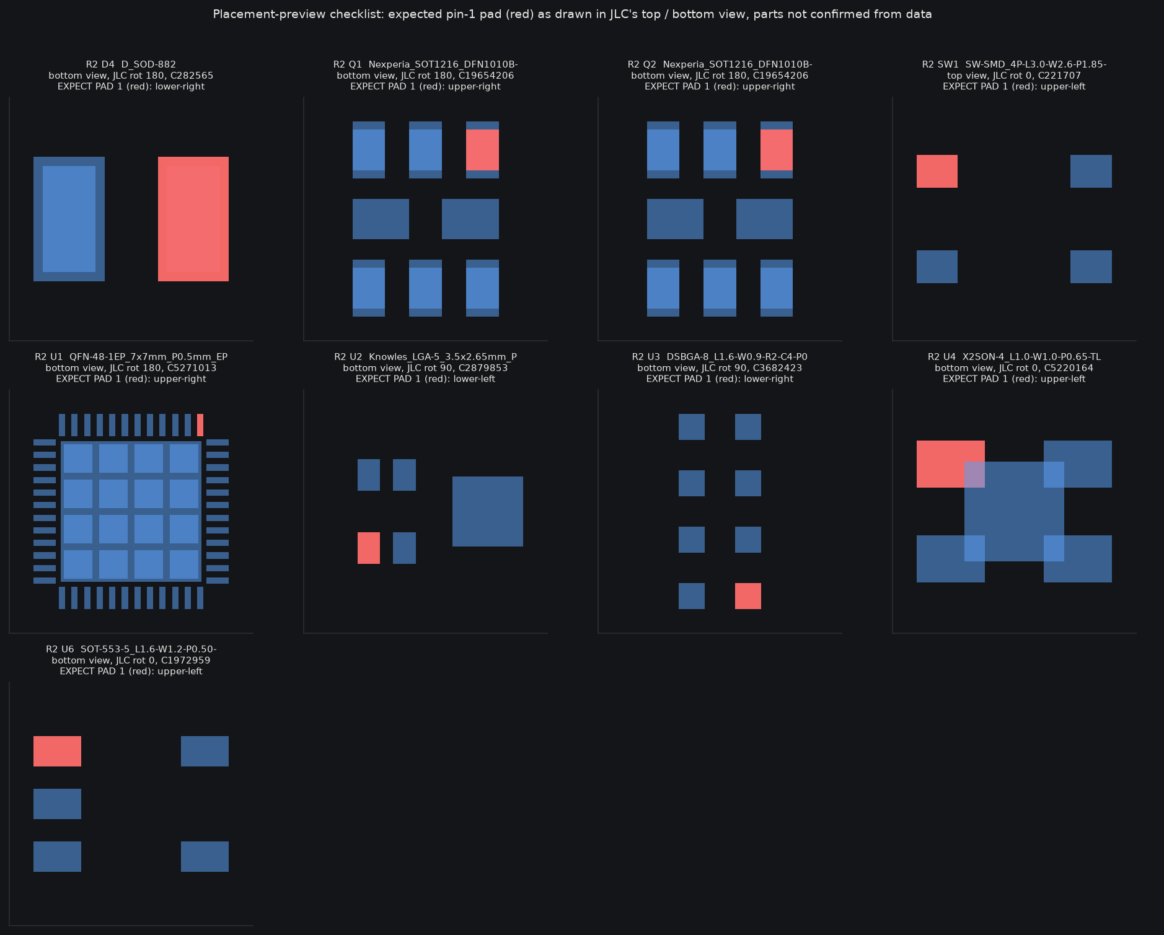
.pcba-workflow/r2-release/pin1_expected.png
