HrafnaValkyrja/ultrasonic/docs/bench/bench-day-1.png

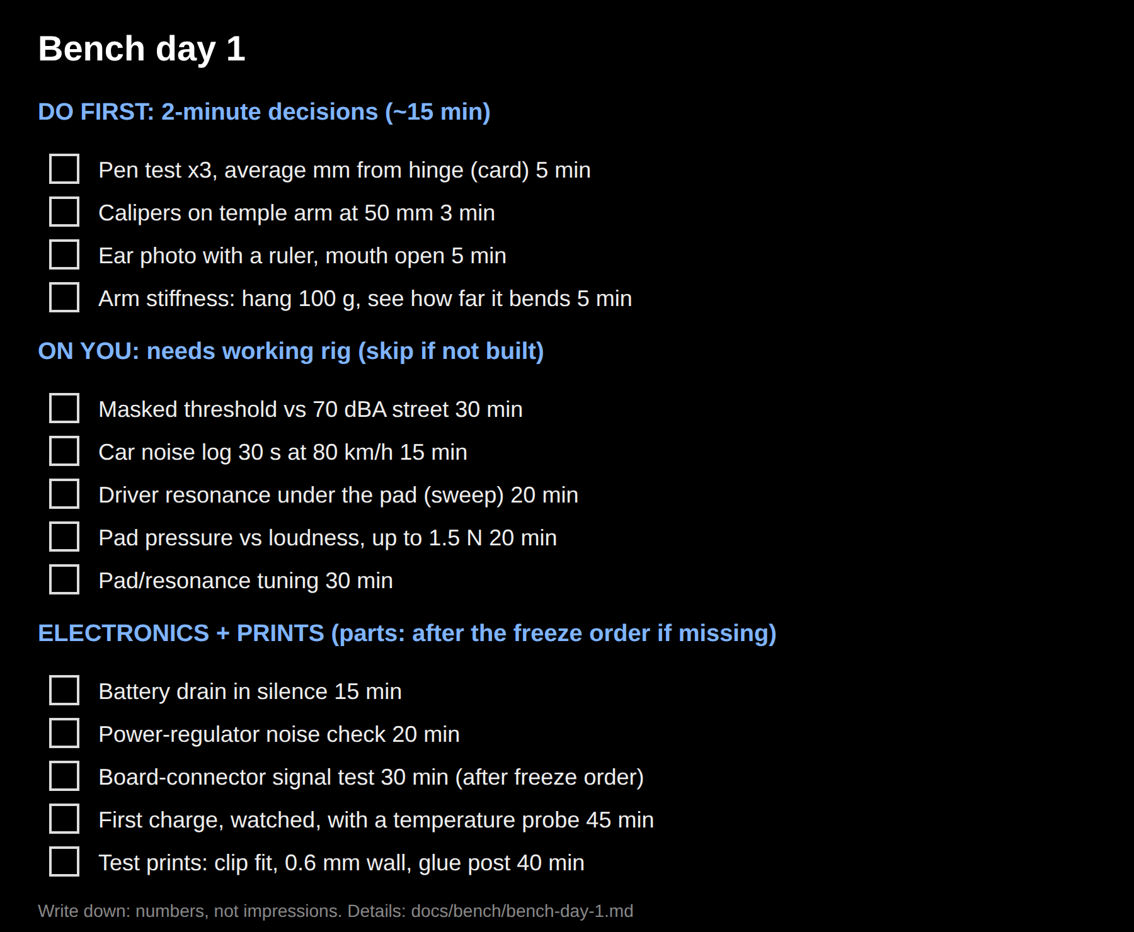
docs/bench/bench-day-1.png
