HrafnaValkyrja/ultrasonic/docs/diagrams/jig-lidstack-exploded.png

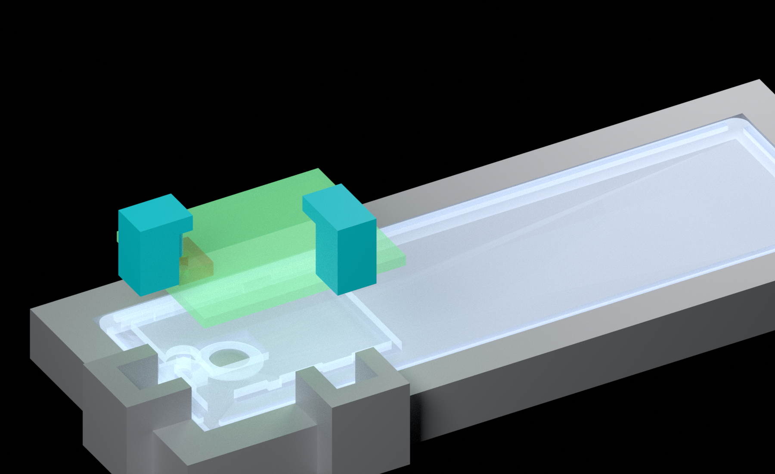
docs/diagrams/jig-lidstack-exploded.png
