HrafnaValkyrja/ultrasonic/docs/diagrams/jig-lidstack.png

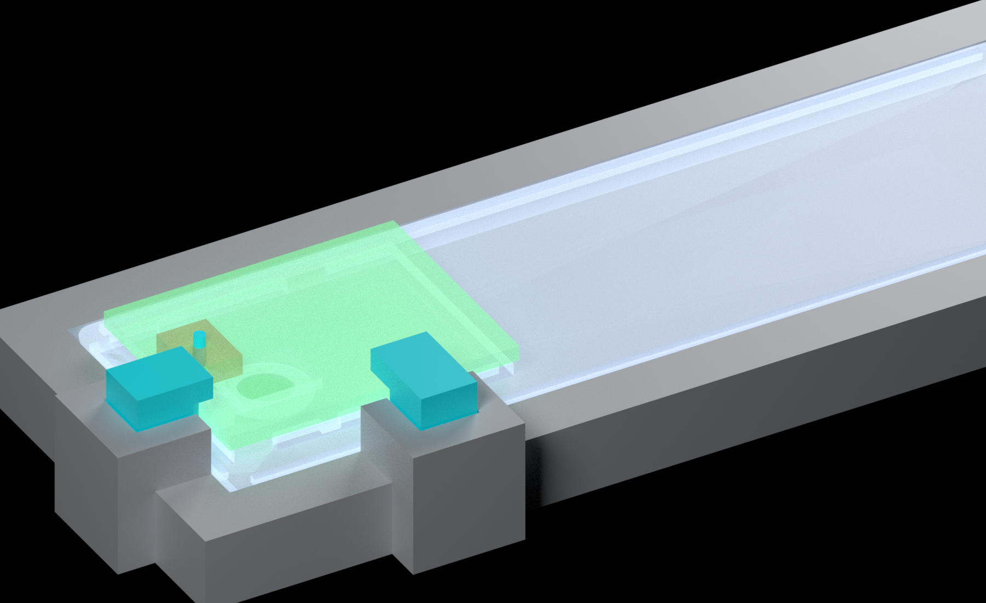
docs/diagrams/jig-lidstack.png
