HrafnaValkyrja/ultrasonic/docs/learn/01-big-picture.png

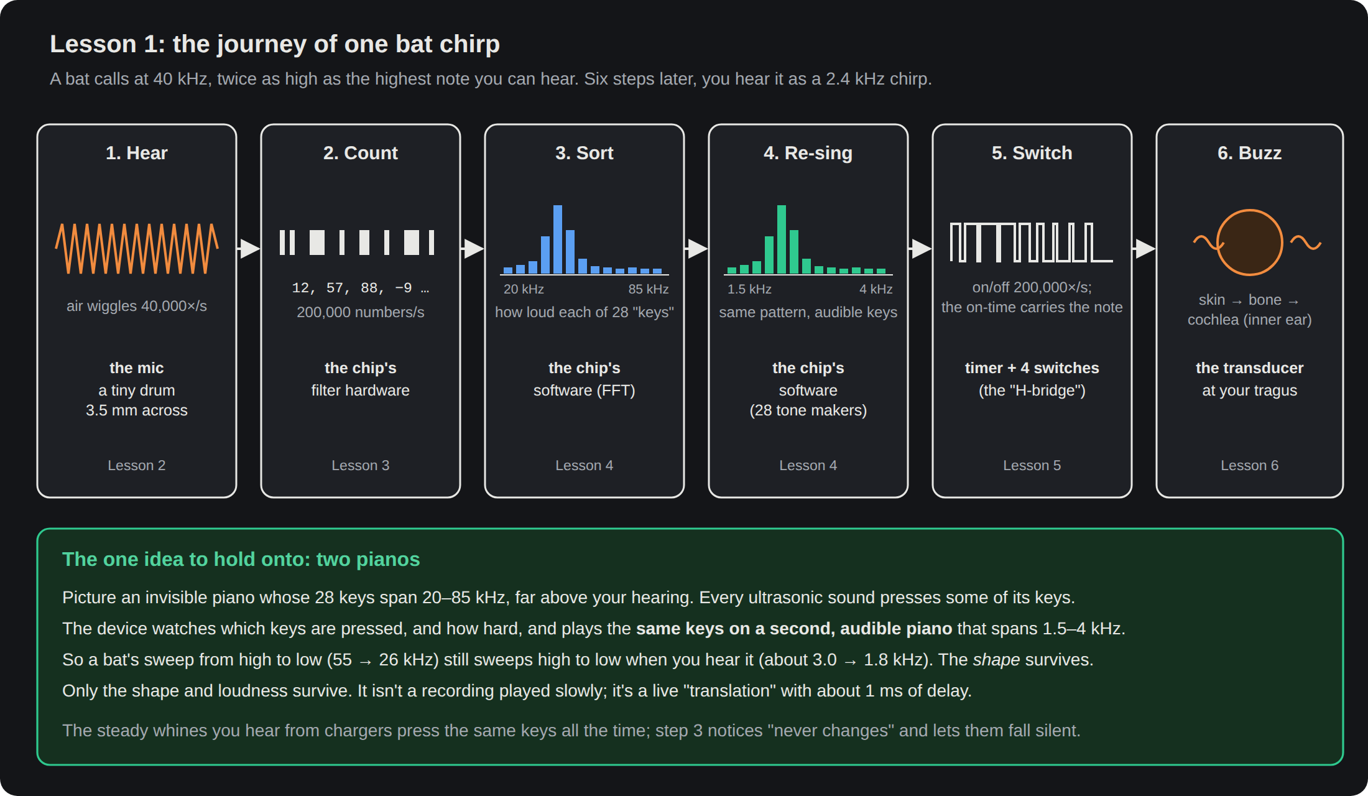
docs/learn/01-big-picture.png
