HrafnaValkyrja/ultrasonic/docs/learn/02-inside-the-chip.png

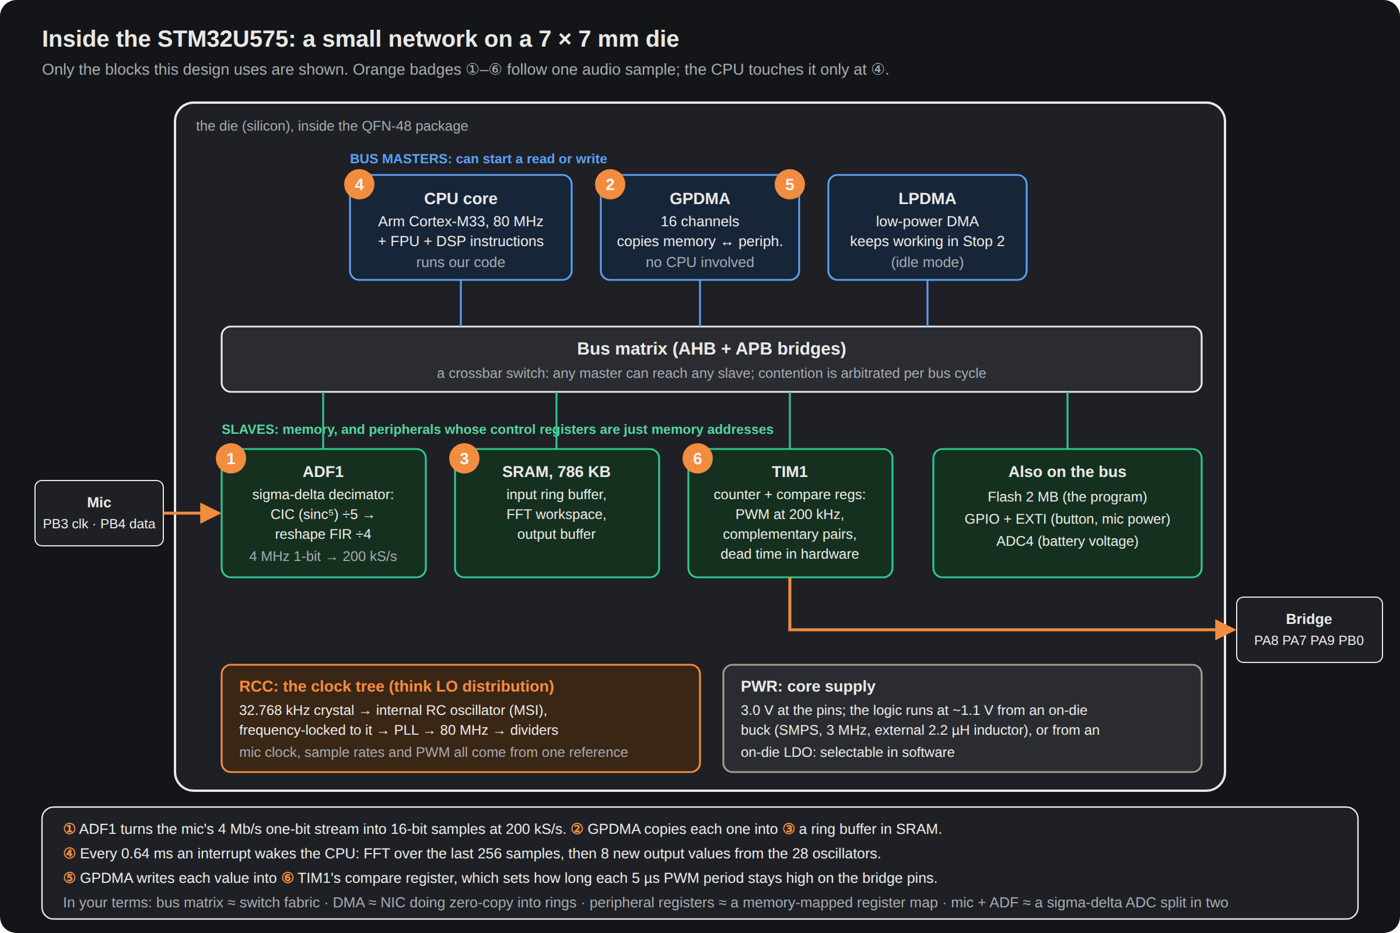
docs/learn/02-inside-the-chip.png
