HrafnaValkyrja/ultrasonic/docs/learn/03-four-layer-board.png

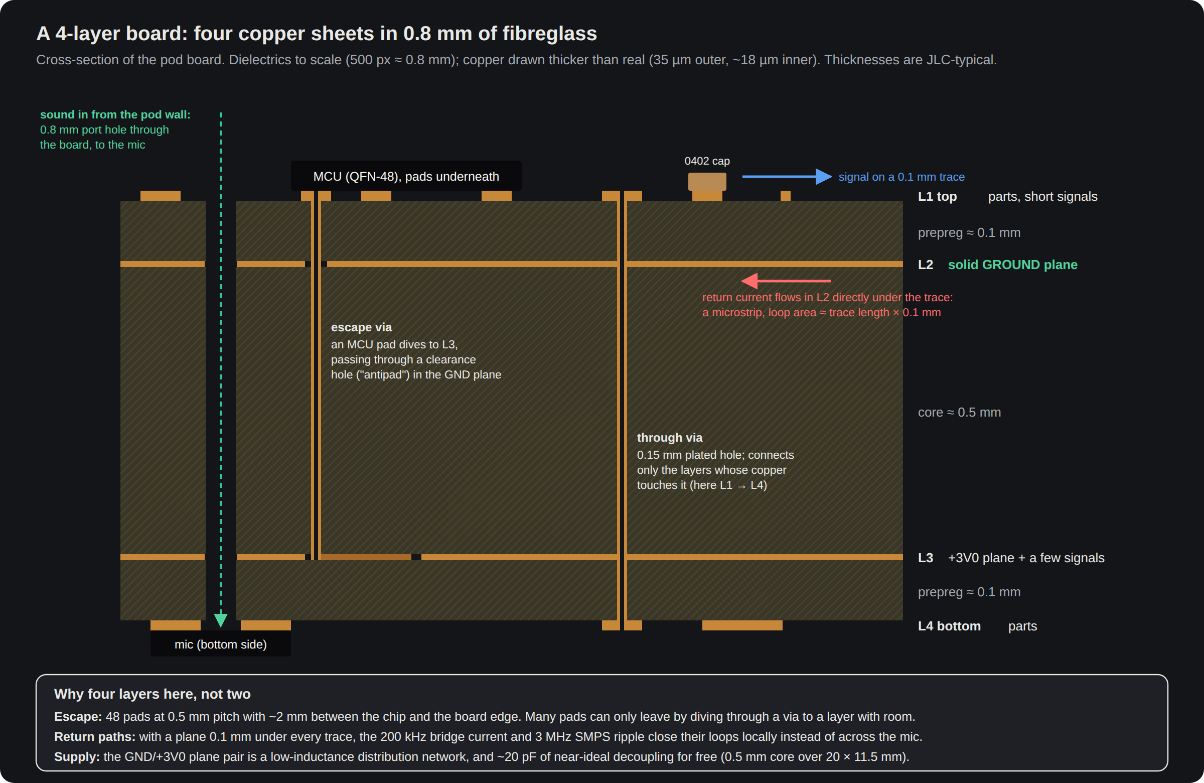
docs/learn/03-four-layer-board.png
