HrafnaValkyrja/ultrasonic/docs/proof/electrical/audibility_reconciled.png

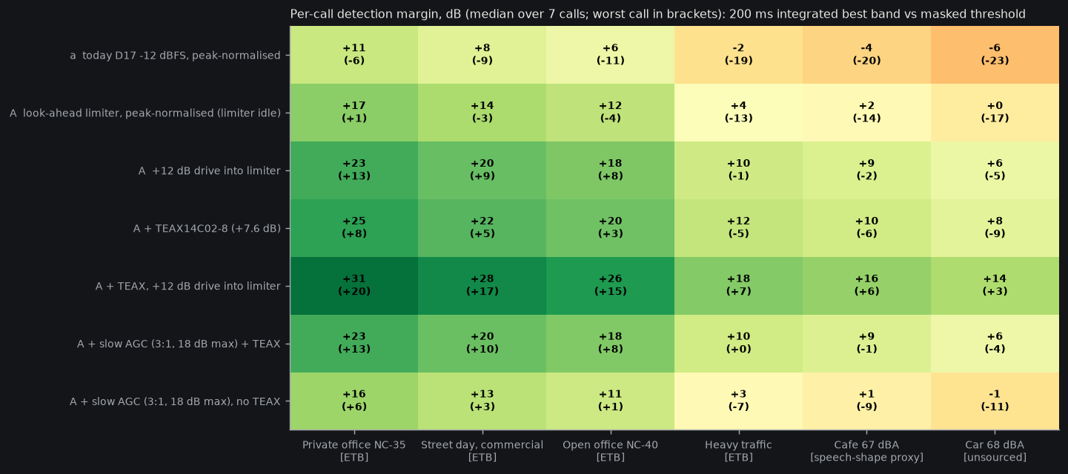
docs/proof/electrical/audibility_reconciled.png
