HrafnaValkyrja/ultrasonic/docs/proof/electrical/loudness.png

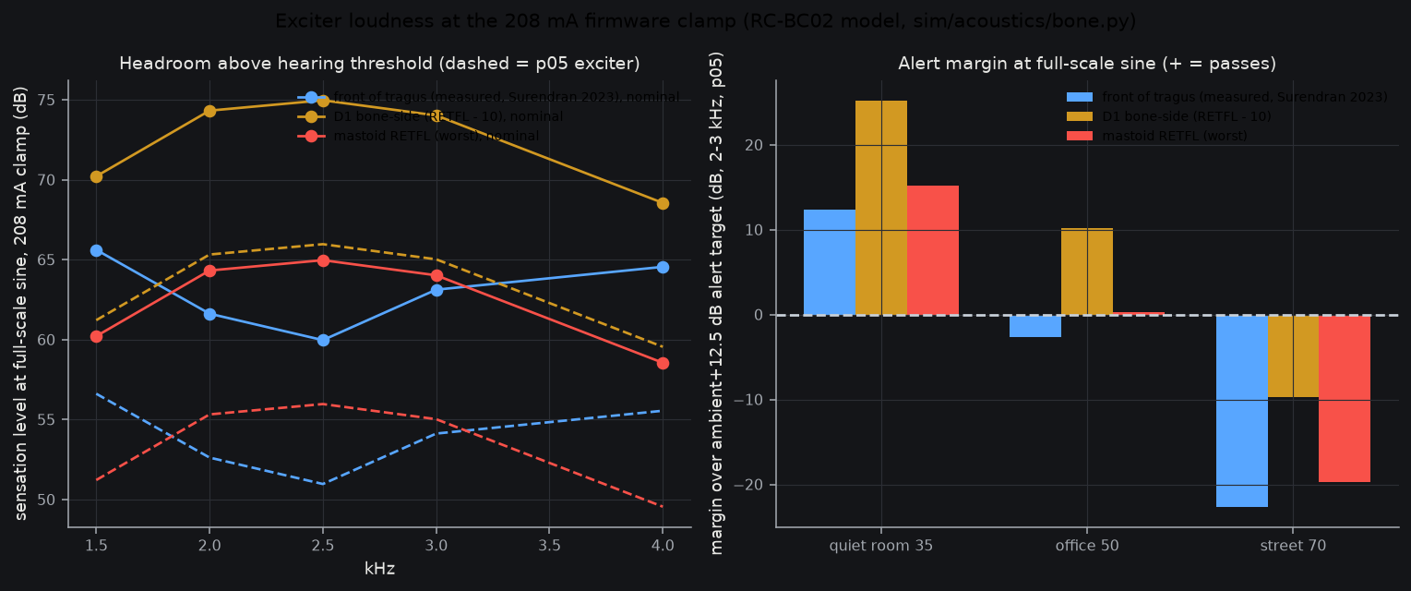
docs/proof/electrical/loudness.png
