HrafnaValkyrja/ultrasonic/docs/proof/electrical/loudness_fw.png

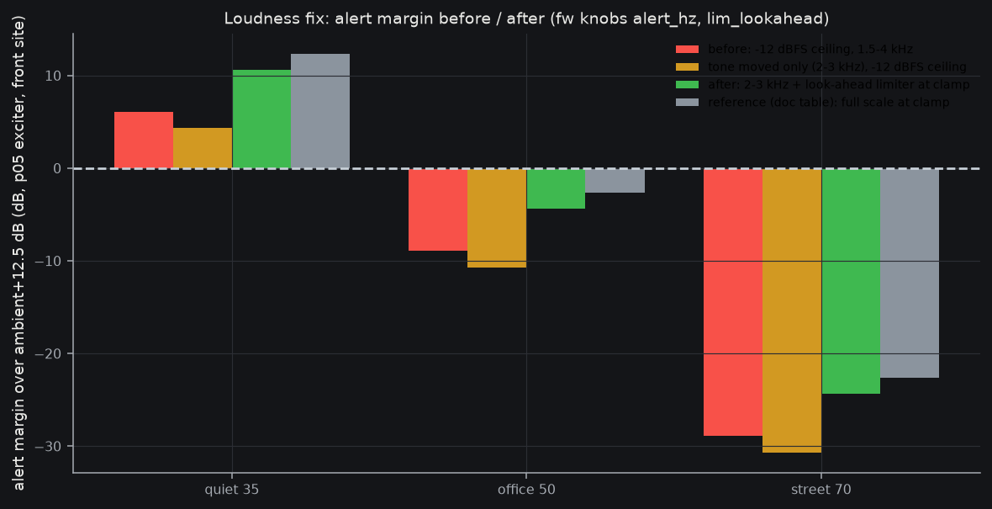
docs/proof/electrical/loudness_fw.png
