HrafnaValkyrja/ultrasonic/docs/proof/physical/physical.png

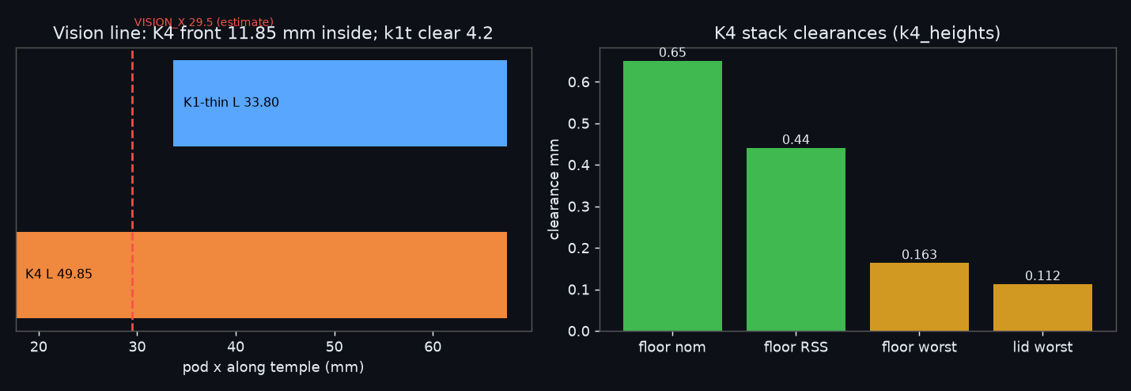
docs/proof/physical/physical.png
