HrafnaValkyrja/ultrasonic/docs/proof/thermal/thermal.png

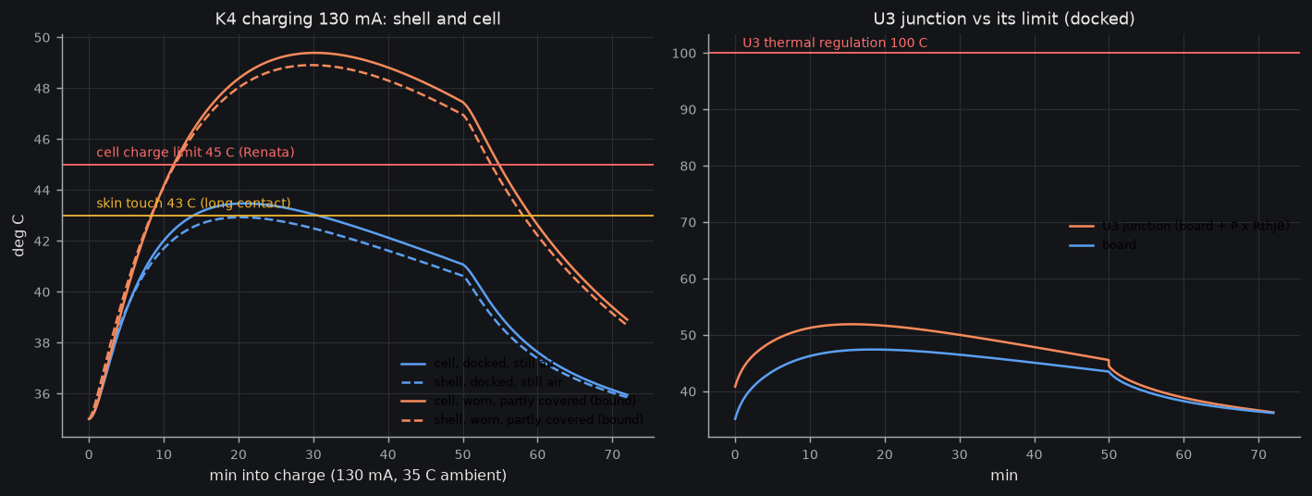
docs/proof/thermal/thermal.png
