HrafnaValkyrja/ultrasonic/docs/research/img/k1t_button_section.png

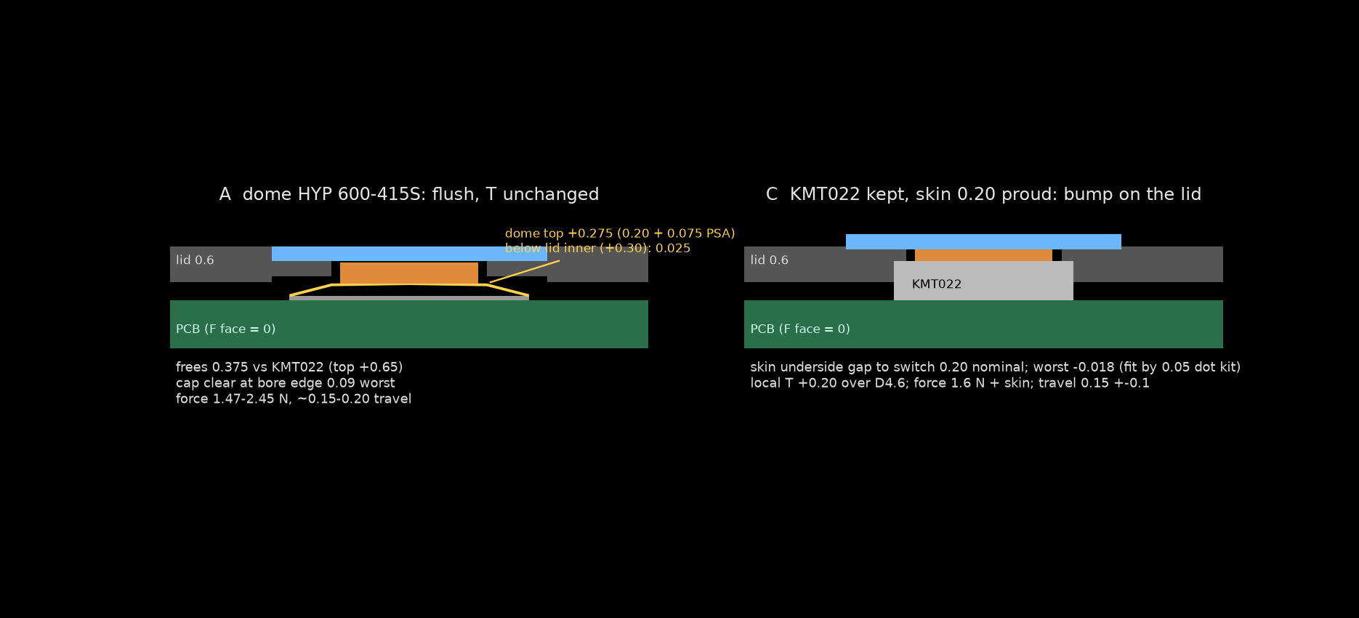
docs/research/img/k1t_button_section.png
