HrafnaValkyrja/ultrasonic/docs/research/simplify/output-compare.png

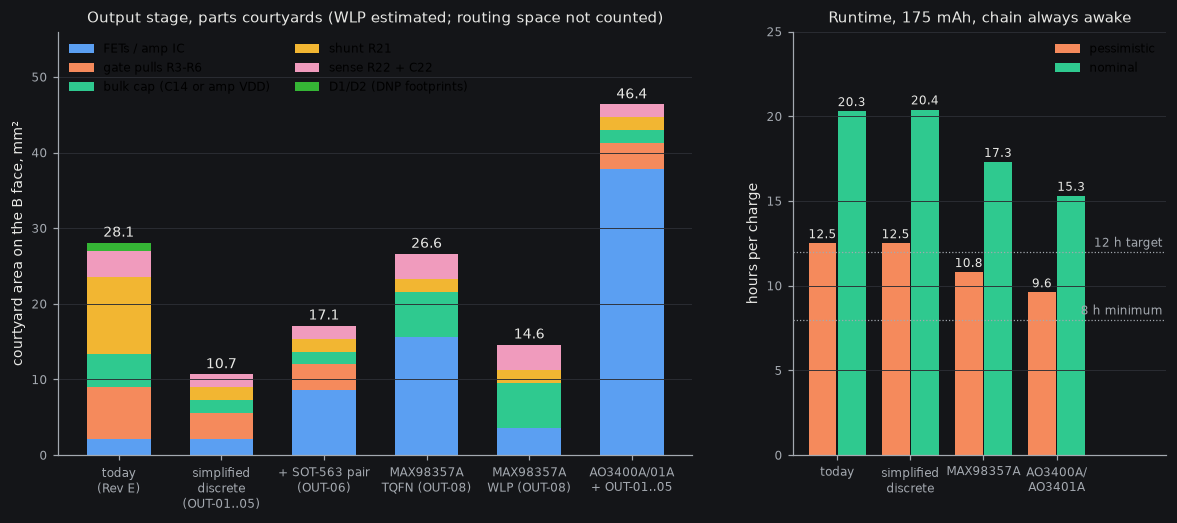
docs/research/simplify/output-compare.png
