HrafnaValkyrja/ultrasonic/docs/review-v1/niti-types.png

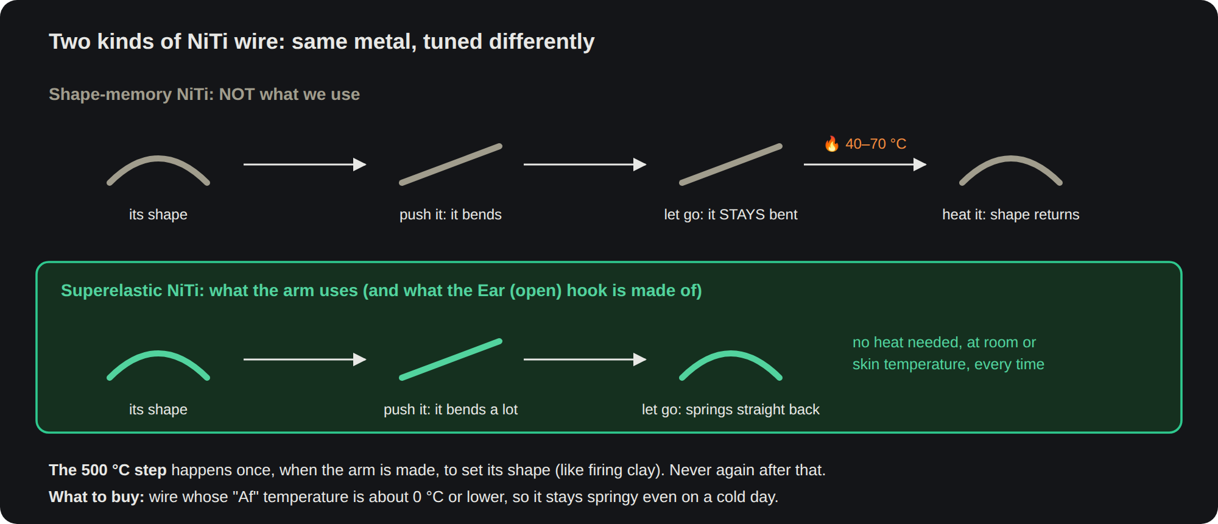
docs/review-v1/niti-types.png
