HrafnaValkyrja/ultrasonic/docs/review-v1/roadmap.png

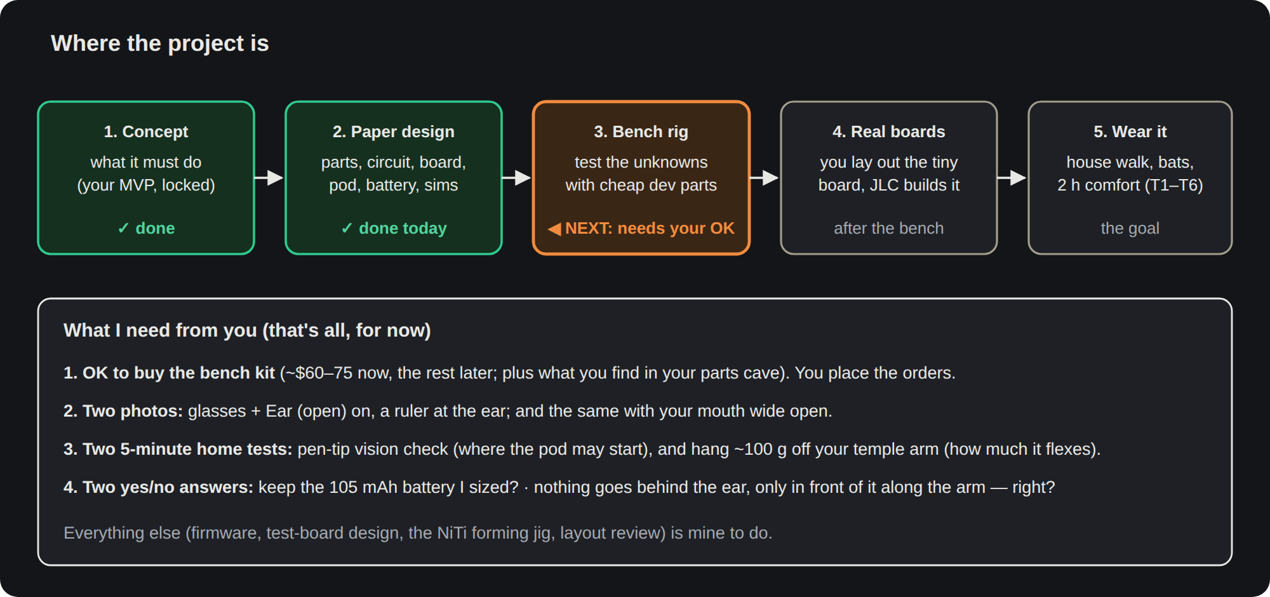
docs/review-v1/roadmap.png
