HrafnaValkyrja/ultrasonic/hw/pod/sch/png/sheet-1.png

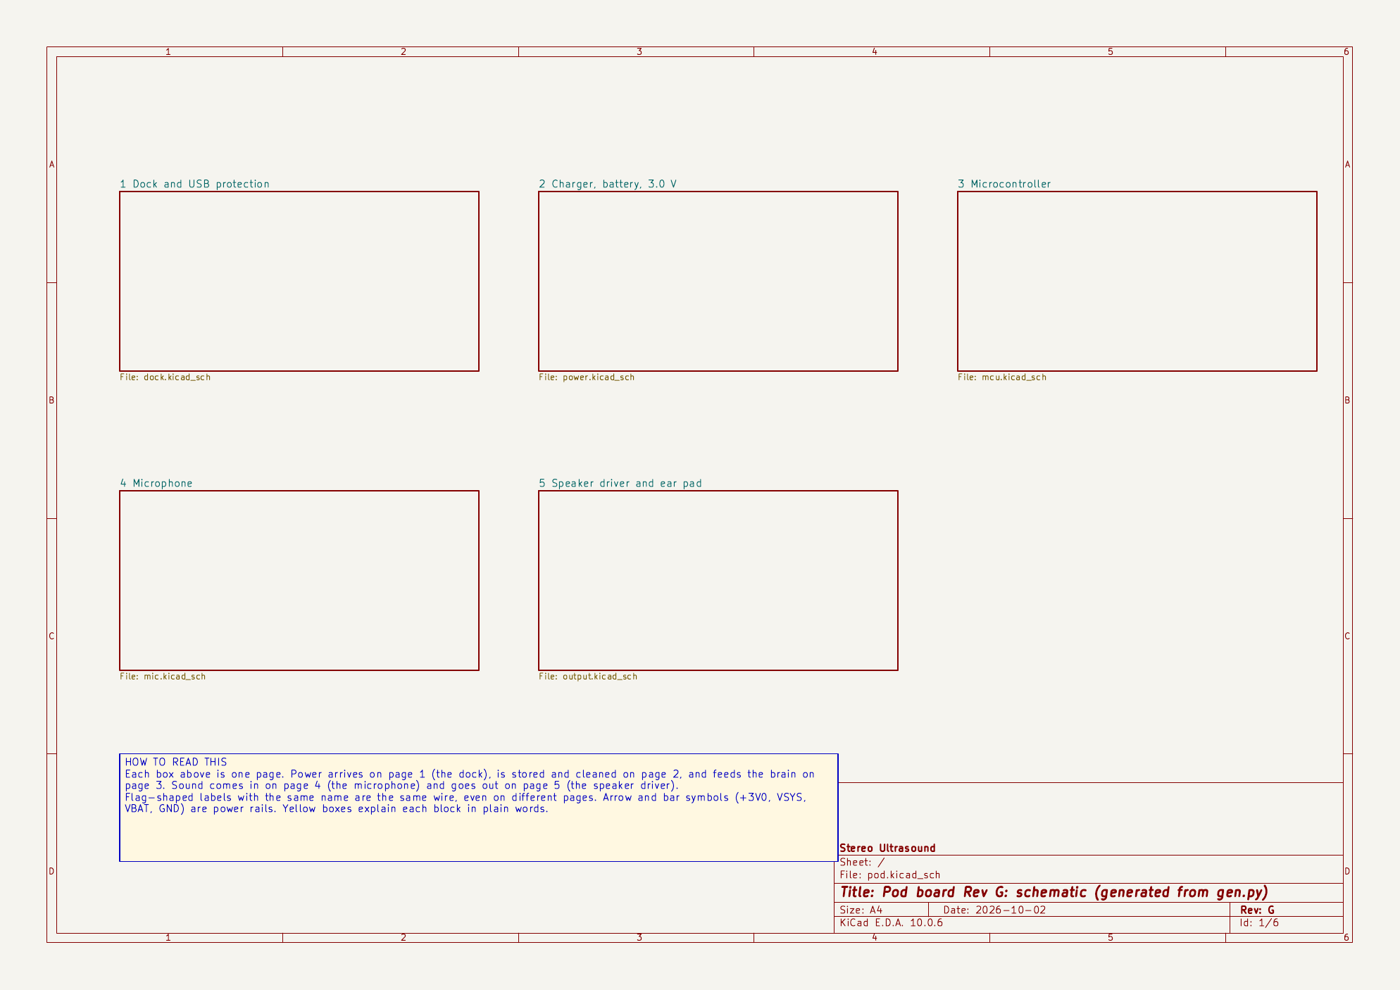
hw/pod/sch/png/sheet-1.png
