HrafnaValkyrja/ultrasonic/hw/pod/sch/png/sheet-2.png

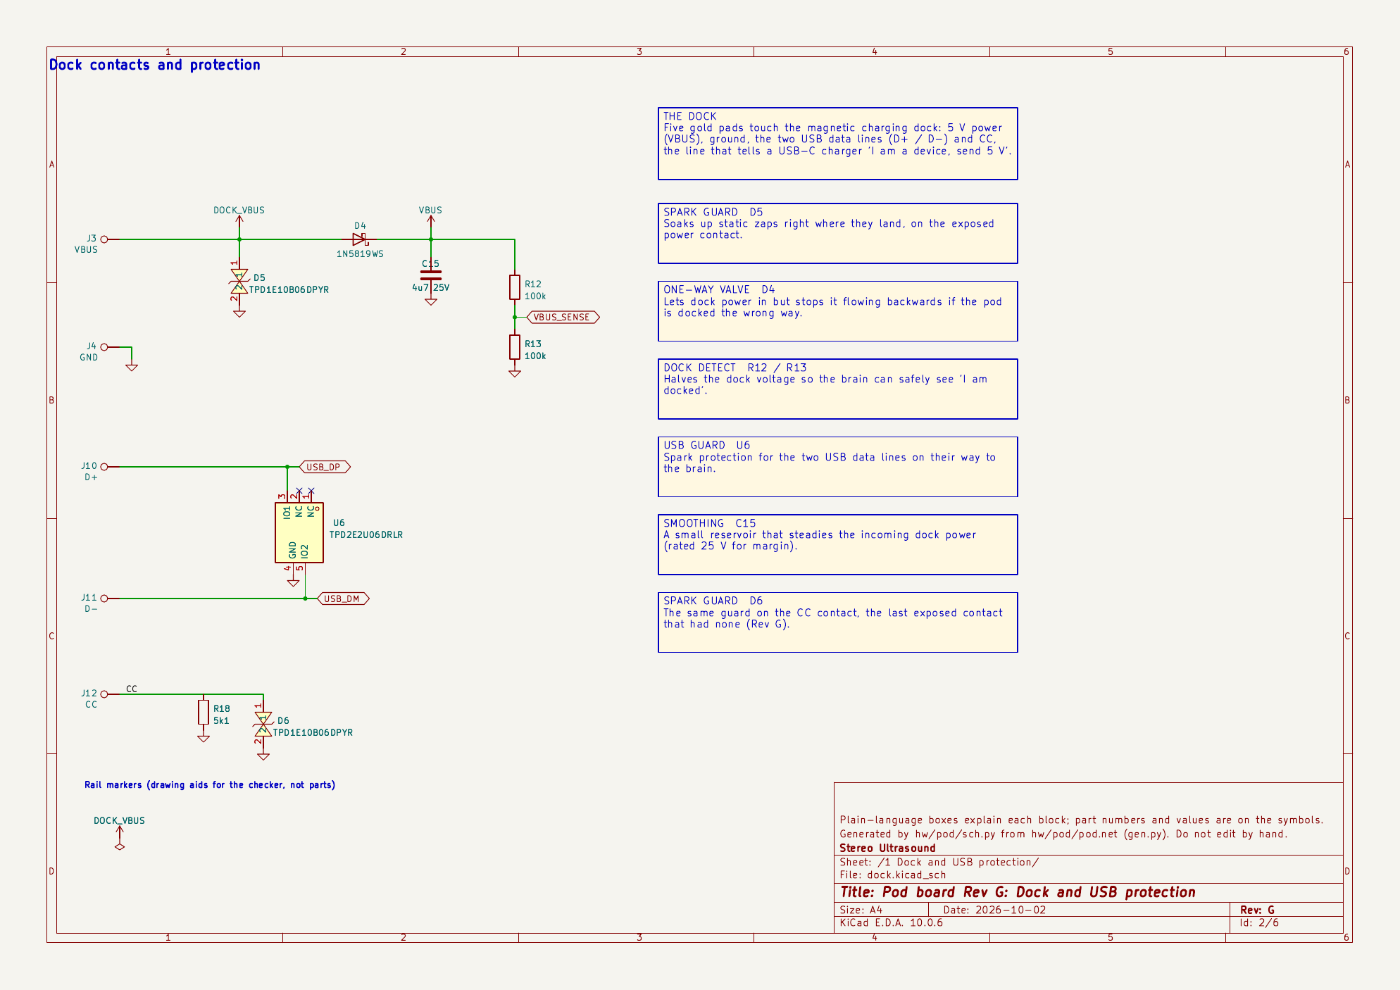
hw/pod/sch/png/sheet-2.png
