HrafnaValkyrja/ultrasonic/hw/pod/sch/png/sheet-3.png

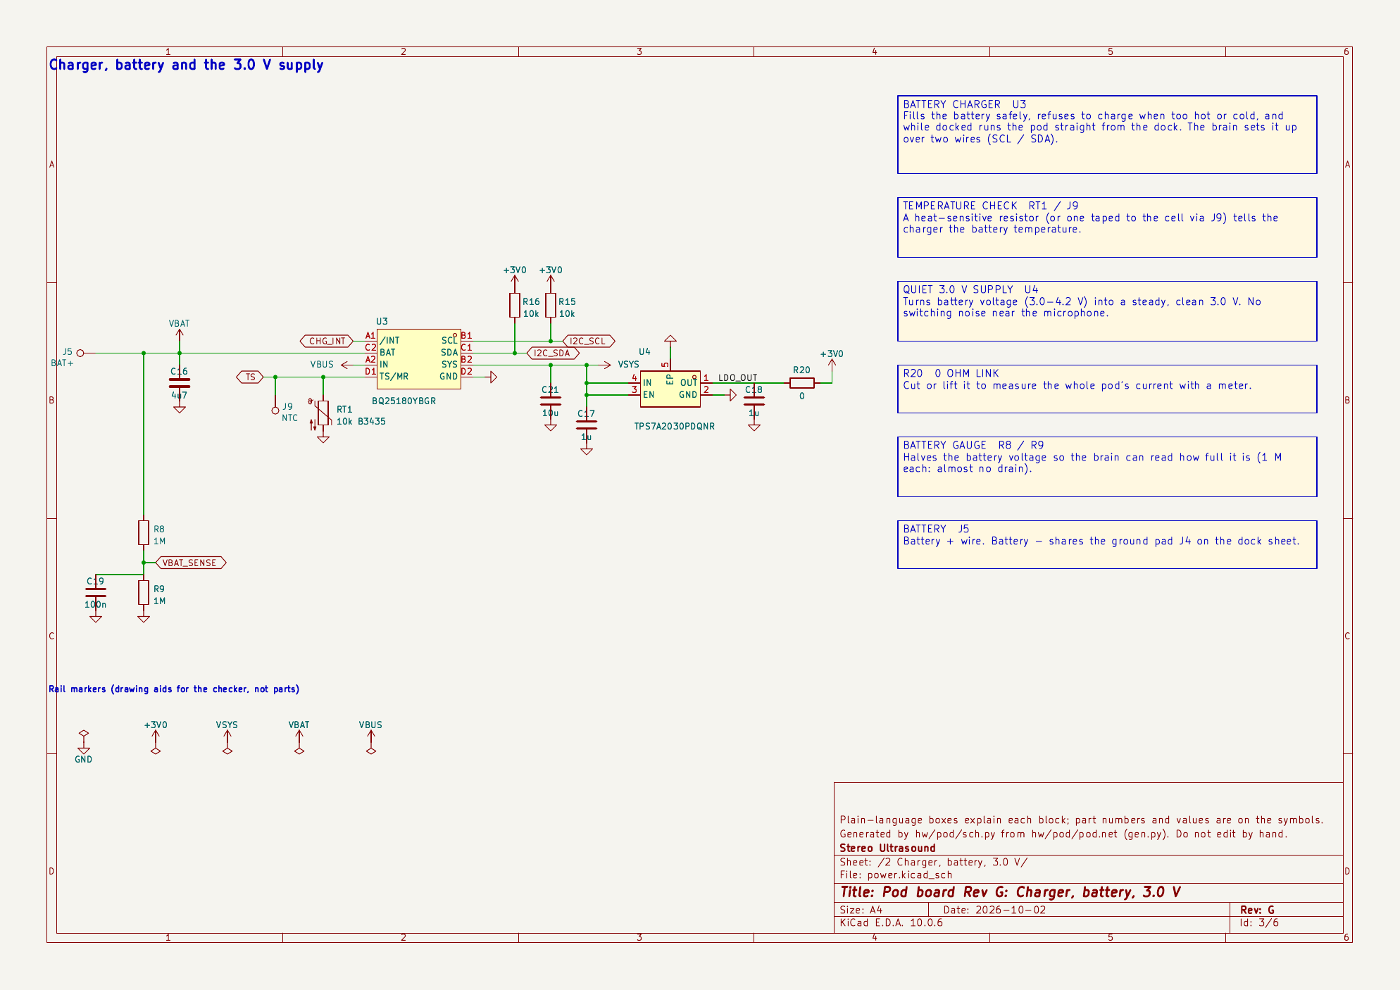
hw/pod/sch/png/sheet-3.png
