HrafnaValkyrja/ultrasonic/hw/pod/sch/png/sheet-4.png

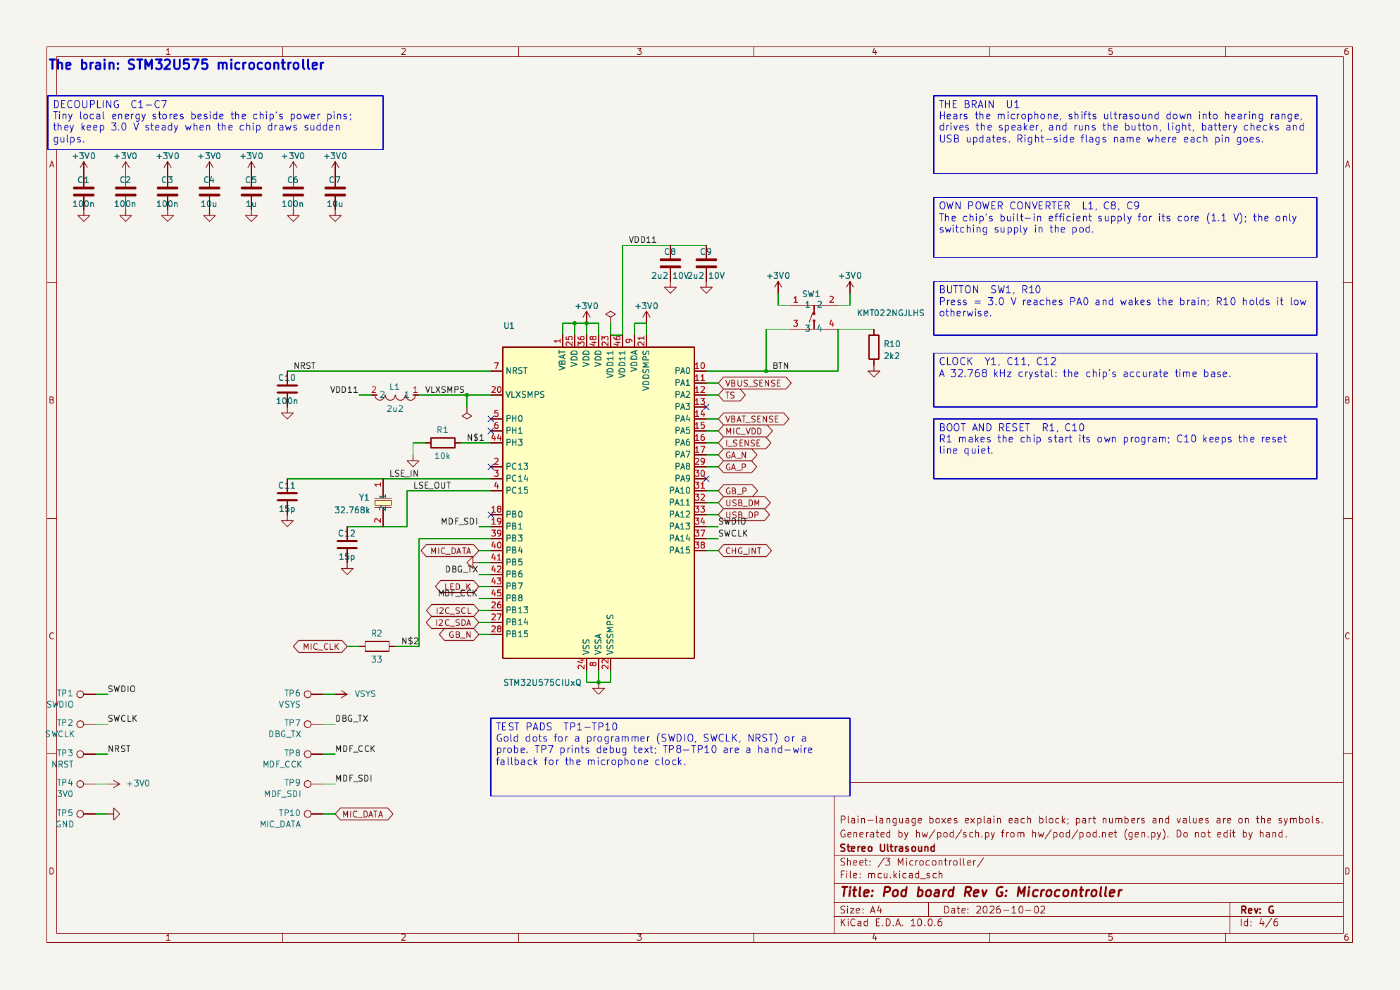
hw/pod/sch/png/sheet-4.png
