HrafnaValkyrja/ultrasonic/hw/pod/sch/png/sheet-5.png

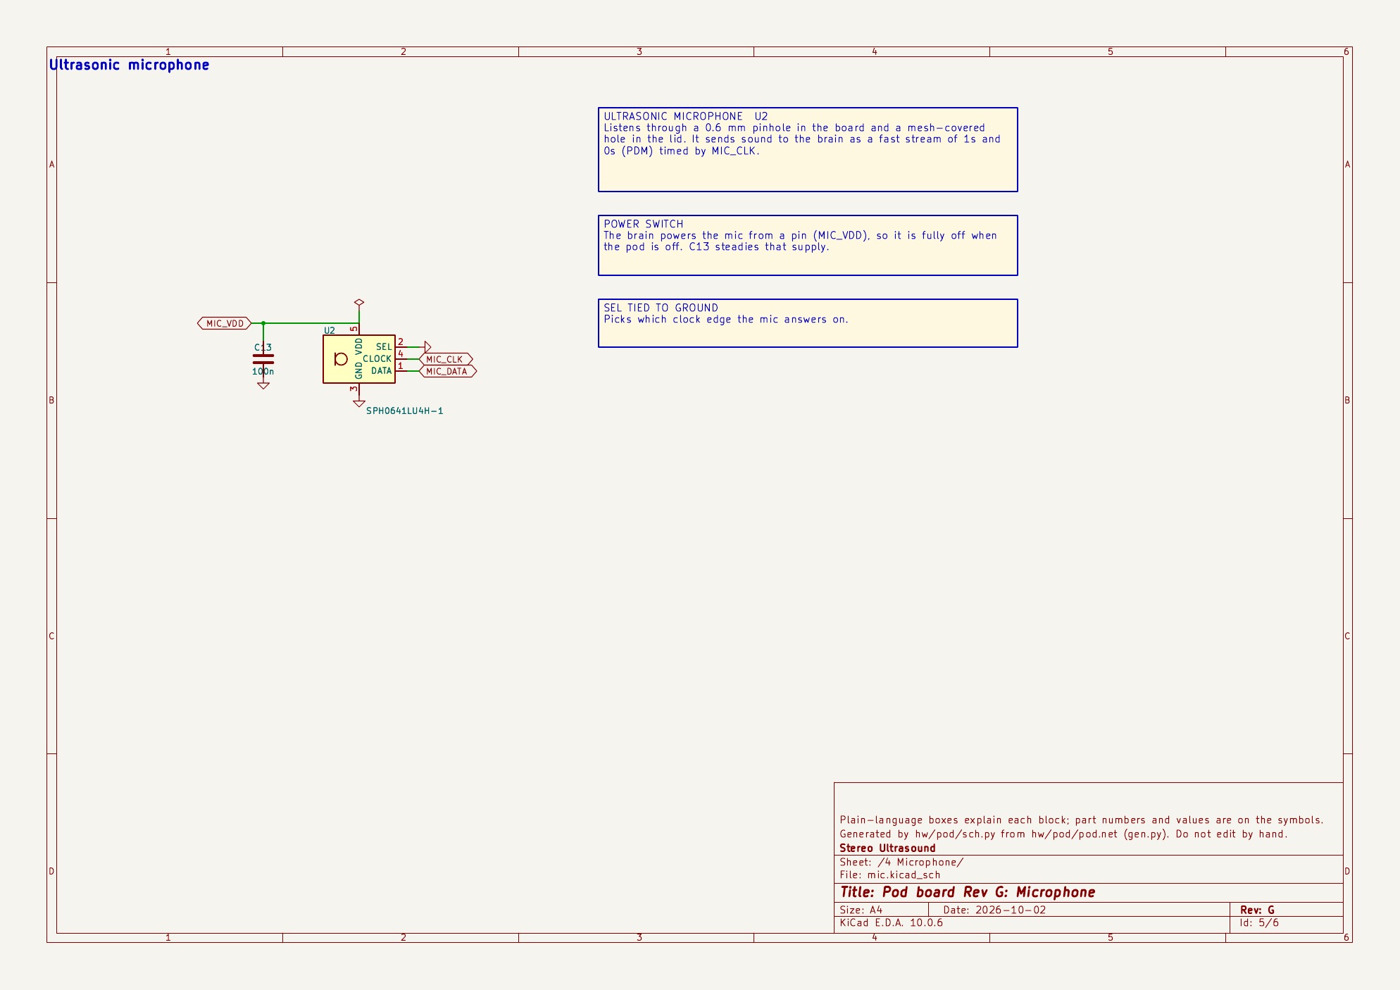
hw/pod/sch/png/sheet-5.png
