HrafnaValkyrja/ultrasonic/hw/pod/sch/png/sheet-6.png

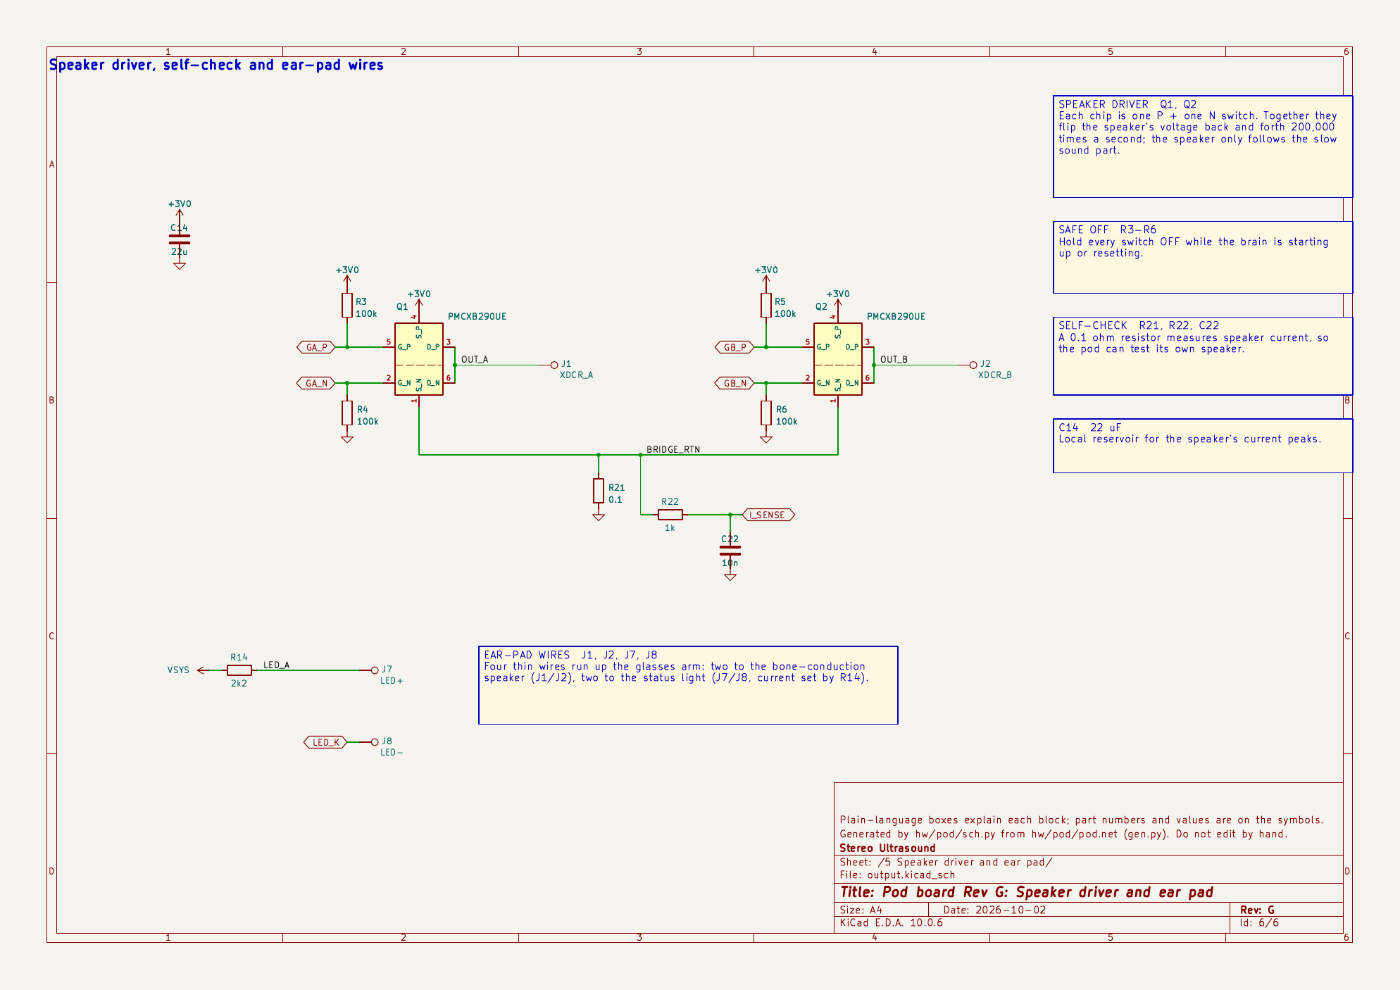
hw/pod/sch/png/sheet-6.png
