HrafnaValkyrja/ultrasonic/sim/noise/out_r2/noise_budget.png

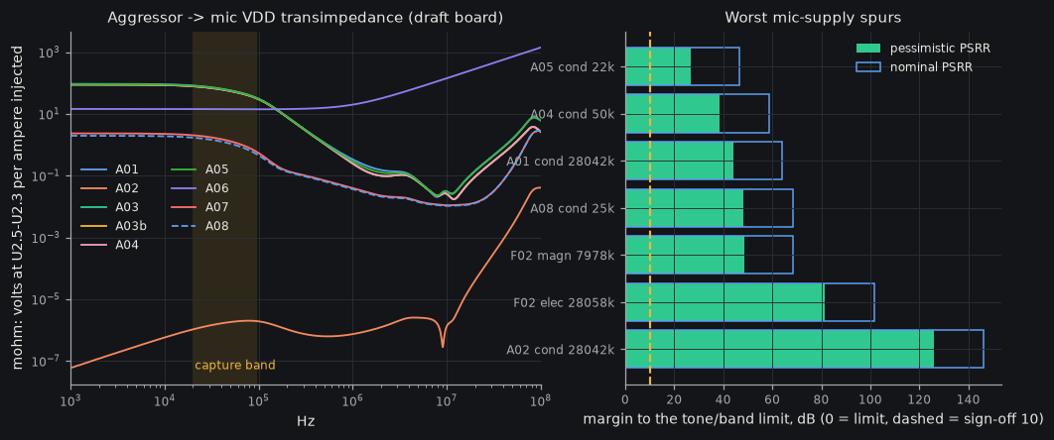
sim/noise/out_r2/noise_budget.png
