HrafnaValkyrja/ultrasonic/hw/padboard/bom_jlc.csv

Comment | Designator | Footprint | LCSC Part # | Qty
BLUE_0402 | D1 | LED_0402_1005Metric | C131223 | 1
