HrafnaValkyrja/ultrasonic/docs/learn/04-board-parts.png

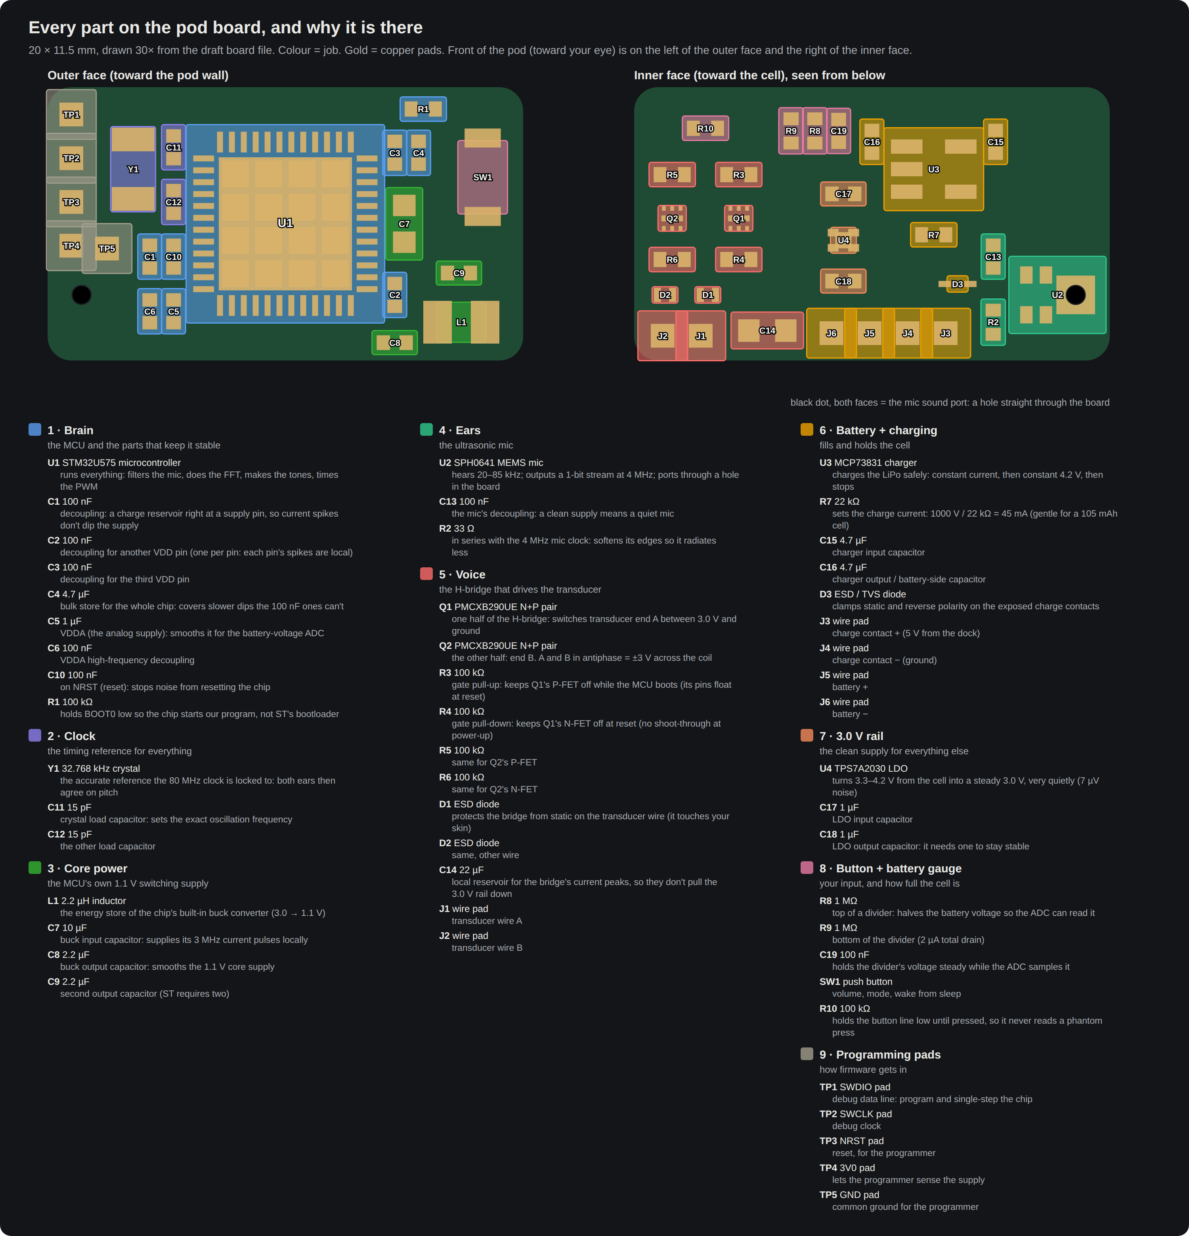
docs/learn/04-board-parts.png
