HrafnaValkyrja/ultrasonic/hw/pod/density/b_qfn32_u3_L17.kicad_pcb

## KiCad design hw/pod/density/b_qfn32_u3_L17.kicad_pcb (2026-10-07)

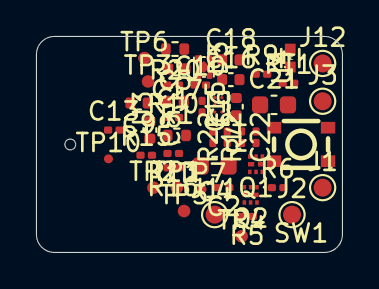
[picture p55: board b_qfn32_u3_L17.kicad_pcb from above]

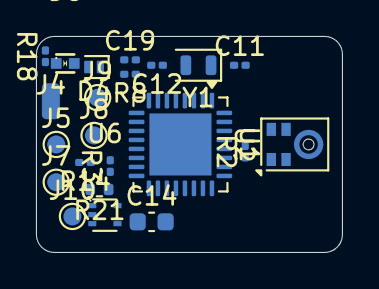
[picture p56: board b_qfn32_u3_L17.kicad_pcb from below]

Board: 4 copper layers, 17.0 x 12.0 mm, 69 parts (22 on the bottom side), 39 nets, no tracks yet.

Parts:
C1, C2, C6, C10, C11, C12, C13, C19, C22: C_0201_0603Metric
C4, C14, C21: C_0603_1608Metric
C5, C8, C9, C15, C16, C17, C18: C_0402_1005Metric
D4: D_SOD-882
D5, D6: X1SON-2_L1.0-W0.6-P0.65-BI-1
J1, J2, J3, J5, J7, J8, J9, J10, J11, J12: TestPoint_Pad_D1.0mm
J4: WirePad_1.0x2.0mm
Q1, Q2: Nexperia_SOT1216_DFN1010B-6
R1, R20, R21: R_0402_1005Metric
R2, R3, R4, R5, R6, R8, R9, R10, R12, R13, R14, R15, R16, R18, R22: R_0201_0603Metric
RT1: R_0201_0603Metric
SW1: SW-SMD_4P-L3.0-W2.6-P1.85-LS3.4
TP1, TP2, TP3, TP4, TP5, TP6: TestPoint_Pad_D0.7mm
TP7, TP10: TestDot_D0.5mm
U1: QFN-32-1EP_5x5mm_P0.5mm_EP3.45x3.45mm
U2: Knowles_LGA-5_3.5x2.65mm; Knowles_LGA-5_3.5x2.65mm_Port0.6
U3: DSBGA-8_L1.6-W0.9-R2-C4-P0.40-BL
U4: X2SON-4_L1.0-W1.0-P0.65-TL-EP
U6: SOT-553-5_L1.6-W1.2-P0.50-LS1.6-TL-1
Y1: Crystal_SMD_2012-2Pin_2.0x1.2mm

Connections:
+3V0: C1.1, C2.1, C4.1, C5.1, C6.1, C14.1, Q1.4, Q2.4, R3.2, R5.2, R15.2, R16.2, R20.2, SW1.1, SW1.2, TP4.1, U1.1, U1.5, U1.17
BRIDGE_RTN: Q1.1, Q2.1, R21.1, R22.1
BTN: R10.1, SW1.3, SW1.4, U1.6
CC: D6.1, J12.1, R18.1
CHG_INT: U1.25, U3.A1
DBG_TX: TP7.1, U1.19
DOCK_VBUS: D4.2, D5.1, J3.1
GA_N: Q1.2, R4.1, U1.13
GA_P: Q1.5, R3.1, U1.18
GB_N: Q2.2, R6.1, U1.15
GB_P: Q2.5, R5.1, U1.20
GND: C1.2, C2.2, C4.2, C5.2, C6.2, C8.2, C9.2, C10.2, C11.2, C12.2, C13.2, C14.2, C15.2, C16.2, C17.2, C18.2, C19.2, C21.2, C22.2, D5.2, D6.2, J4.1, R1.2, R4.2, R6.2, R9.2, R10.2, R13.2, R18.2, R21.2, RT1.2, TP5.1, U1.16, U1.32, U1.33, U2.2, U2.3, U3.D2, U4.2, U4.5, U6.4
I2C_SCL: R15.1, U1.29, U3.B1
I2C_SDA: R16.1, U1.7, U3.C1
I_SENSE: C22.1, R22.2, U1.11
LDO_OUT: C18.1, R20.1, U4.1
LED_A: J7.1, R14.2
LED_K: J8.1, U1.14
LSE_IN: C11.1, U1.2, Y1.1
LSE_OUT: C12.1, U1.3, Y1.2
MIC_CLK: R2.2, U2.4
MIC_DATA: TP10.1, U1.27, U2.1
MIC_VDD: C13.1, U1.12, U2.5
unnamed: R1.1, U1.30
unnamed: R2.1, U1.26
NRST: C10.1, TP3.1, U1.4
OUT_A: J1.1, Q1.3, Q1.6, Q1.7, Q1.8
OUT_B: J2.1, Q2.3, Q2.6, Q2.7, Q2.8
SWCLK: TP2.1, U1.24
SWDIO: TP1.1, U1.23
TS: J9.1, RT1.1, U1.8, U3.D1
USB_DM: J11.1, U1.21, U6.5
USB_DP: J10.1, U1.22, U6.3
VBAT: C16.1, J5.1, R8.1, U3.C2
VBAT_SENSE: C19.1, R8.2, R9.1, U1.9
VBUS: C15.1, D4.1, R12.1, U3.A2
VBUS_SENSE: R12.2, R13.1, U1.10
VDD11: C8.1, C9.1, U1.31
VSYS: C17.1, C21.1, R14.1, TP6.1, U3.B2, U4.3, U4.4
