HrafnaValkyrja/ultrasonic/docs/brief/backlog.yaml

# ENGINEERING BACKLOG (AI-facing). The queue that proves whether unblocked work exists.
# Scope: RE-BASELINED 2026-10-08 for K4 (O33: two stacked 6L boards P/M, ECR-0020/0021, hw/pod/k4/, shell_k4, pod_mass k4). Built 2026-10-07 for phase2 (MZ-2, ECR-0018, draft_r2/shell_r2); r2-only entries are st stale-closed (st_r2 keeps the old status), still-valid ones carry a k4: re-point, new ones are K4-*.
# (old scope line follows) current design hw/current.yaml = phase2 (MZ-2, ECR-0018). Built 2026-10-07 by the backlog agent
# (session 01Wg997D) from: numbered "Open issues" in docs/system/*.md, `tools/plm.py status` open ECRs,
# WARN lines of tools/checks/interfaces.py + bom_check.py (run 2026-10-07), docs/brief/queue.yaml tier-B/open non-owner items.
# Keys: id (doc-prefix + the doc's stable issue id), src, t (one line), blk (blocker), cls (risk|evidence|hygiene),
#   rank (unblocked only; value order: design risk > evidence gap > hygiene), dup (same issue tracked elsewhere), st (open|done|stale-closed).
# blk values: none | owner (decision; options+rec in `opts`) | hardware (parts/bench/board; O21 = no orders before freeze)
#   | router (needs re-route/placement: parallel agents may not) | fw-agent (fw/ + firmware-emulation.yaml owned by another agent) | item:<id>
# Prefixes: OUT sub-output, PROC sub-processing, PWR sub-power, DK sub-dock-usb, SAI sub-audio-in, DBG sub-debug-test, UI sub-ui,
#   RB reg-board, RPB reg-pod-body, ARM reg-arm, PAD reg-pad, PHYS physical, ECR plm, CHK checks, Q queue.
# Maintenance: when an item closes, set st + evidence (commit) here AND in its source doc in the same commit.
schema: 1
date: 2026-10-08
counts: {total: 139, unblocked: 49, owner: 28, hardware: 41, router: 6, fw_agent: 7, item_dep: 4, stale_closed_section: 2}   # entries (dups folded); update on every close
counts_before_k4_2026-10-07: {total: 116, unblocked: 40, owner: 23, hardware: 36, router: 4, fw_agent: 7, item_dep: 4, stale_closed: 2}
k4_rebaseline_2026-10-08: {stale_closed_by_k4: 15, repointed_k4_field: 69, new_k4_items: 16, new_open_unblocked: 9, new_blocked_unblocked_class: 2, new_hardware: 5, new_router: 2, done_this_pass: [K4-DOCK-STRIP, K4-SW1-PRESS, K4-SHELLCHK], open_unblocked_by_rank_k4: [K4-BM28-DS(fetch blocked), K4-SW1-PRESS, K4-STACK6, K4-SHELLCHK, K4-CONDUCT(item), K4-HEIGHTS, K4-BOM-STOCK, K4-DOCS-MPLANE, K4-BRINGUP, K4-DIAG, PWR-I14]}
progress_2026-10-07: {done: [UI-2, DK-18, OUT-1, ARM-6, PHYS-8, PROC-6R, PROC-9, VHB-TOL, RB-TOL, SAI-3, DK-16, DK-05, ARM-LEFT, UI-1, PAD-5, RPB-5, RPB-14, DBG-16, DK-01, CHK-STOCK, CHK-IDENT, CHK-MODELS, RB-19, CHK-DRCWARN, ARM-7, RB-9, DK-09], partly: [RPB-12, DK-17, RPB-16, PWR-I9, DIAG], decided_by_coordinator: [RB-20, OUT-6, ARM-6D, RPB-15, RPB-4], blocked_now: [PWR-I14, PWR-I6, RB-2, DK-17], still_open_unblocked: [], stale_closed_in_doc: [RB-18, SAI-14]}

unblocked:   # value order; rank 1 = do first
  - {id: UI-2, rank: 1, cls: risk, src: sub-ui.md#2, dup: [RPB-17, 00-whole risk 12], t: "SW1 press (1.2-2.0 N) reacted only by the 0.8 mm board + VHB; board deflection, VHB stress and whether the KMT022 stroke (0.15+-0.1) survives are uncomputed", close: "scikit-fem plate model of the bonded board under 2.0 N at board (18.5, 6.0)", blk: none, st: "done 2026-10-07 (analysis; sim/checks/sw1_press_fem.py: 2 N -> SW1 1.4-20 um, VHB 12-52 kPa vs 85 kPa 3M dynamic factor; bench press test stays in hardware RPB-17)", commit: 230a471, k4: "SW1 now on M's belly face (ECR-0020); r2 result stands as method only -> K4-SW1-PRESS"}
  - {id: PWR-I14, rank: 2, cls: risk, src: sub-power.md PWR-I14, t: "C21 (VSYS) 10 V class-2 cap vs TI's 25 V recommendation; derated value must stay > 1 uF at 4.5 V", close: "DC-bias of C19702 at 4.5 V from the maker's curve, or a 16/25 V Basic swap", blk: "browser fetch still failing (2026-10-07, headless Chromium): LCSC datasheet C19702 = Samsung catalog (no DC-bias curve); weblib.samsungsem.com/mlcc/mlcc-ec.do?partNumber=CL10A106KP8NNNC loads but its DC-Bias graph is a UI-driven AJAX (/graph/mlccEcMakeGraphJson.do) I could not trigger; product.samsungsem.com part URL errors. Next: owner clicks DC Bias in the weblib page, or swap to a 16/25 V Basic part", st: open, k4: "C21 is on M, now C315248 0402 10 V (ECR-0022). 2026-10-08 JLC API: no 0402 10 uF >=16 V exists; 0603 options are all Extended: C6119814 TDK CGA0603X5R106M160JT 16 V ($0.033, 79,949 in stock), C6119815 CGA0603X5R106K250JT 25 V ($0.045, 195,204 in stock). Both are likely ~0.8-0.9 mm tall vs the 0.70 lid-ledge limit (unverified), so the swap is unlikely to fit; it closes by the C315248 DC-bias curve (owner fetch at order time, see A-CAP-CURVES) or a TDK height check"}
  - {id: PWR-I6, rank: 3, cls: risk, src: sub-power.md PWR-I6, dup: [DBG-9], t: "R20 0402 0R jumper carries the whole +3V0 rail (326 mA peak); rating unsourced", close: "read the jumper's rated current in the maker datasheet", blk: none, st: "done 2026-10-07: Uni-Royal thick-film datasheet V.3 (Feb 12 2019) §7 Ratings, 0402 jumper: <50 mOhm, rated 1 A, max overload 2 A, -55..155 C -> 326 mA peak = 33 % of rating. Source https://datasheet.lcsc.com/datasheet/pdf/0a975aaa49b7c97f38a963127be4a823.pdf?productCode=C17168 (via headless Chromium on lcsc.com/datasheet/C17168.pdf, fetched 2026-10-07)", k4: "R20 stays on M (ECR-0020); result valid; +3V0 now also crosses 3 BM28 contacts (K4-BM28-DS)"}
  - {id: DK-18, rank: 4, cls: risk, src: sub-dock-usb.md DK-18, t: "D5 TPD1E10B06 working voltage 5.5 V vs worst-case dock VBUS; leakage near 5.5 V unknown", close: "datasheet I_leak vs V", blk: none, st: "done 2026-10-07 (SLLSEB1G: VRWM 5.5, ILEAK <= 100 nA at 5 V, VBR >= 6 V; VBUS <= 5.25/5.5 V inside VRWM; bring-up meter check stays in hardware)", commit: 8f17250, k4: "D5 on M at J3 (ECR-0021); result valid"}
  - {id: RPB-12, rank: 5, cls: risk, src: reg-pod-body.md#12, dup: [PHYS-13], t: "seam rebate 0.2 x 0.3 is below the 0.4 resin recess minimum (may fuse); belly step unmarked", close: "widen to 0.4 in shell_r2, mark the step, re-run shell checks", blk: none, st_r2: "partly done 2026-10-07: rebate 0.2 x 0.4 (tub valid, 1318.9 -> 1317.4 mm3); belly-step cut line + reopening procedure still open; done 2026-10-07 (b): belly-step witness groove 0.1 x 0.4 in shell_r2.seam_rebate, shell checks unchanged, tub 1316.6 mm3 valid; docs/build/reopen.md written", commit: 5885ee6, st: "stale-closed 2026-10-08 (K4: shell_r2 seam rebate/witness groove: shell_k4 reuses the rebate, drops the groove (no belly step); re-check rebate >= 0.4 in shell_k4 -> K4-SHELLCHK)"}
  - {id: OUT-1, rank: 6, cls: evidence, src: sub-output.md#1, dup: [DBG-5], t: "self-test |Z| method option D (2f synchronous detection on R21 supply current + offset) unverified", close: "verify in sim/checks/bridge_spice.py", blk: none, st: "done 2026-10-07 (sim/checks/selftest_lockin.py: -12 dBFS |Z| <= 1.9 %, phase <= 0.7 deg; -22 dBFS <= 3 %/3.4 deg at 0.25 s; -32 unusable)", commit: 111b542, k4: "R21/R22/C22 on P; lock-in result valid"}
  - {id: ARM-6, rank: 7, cls: evidence, src: reg-arm.md#6, dup: [PAD-6], t: "strut-housing clearance 1.18-1.34 vs 1.4 target; pad checks.json still reports 0.79 FAIL vs an old tub preview", close: "re-run pad.py + heel.py on the shell_r2 tub", blk: none, st_r2: "done 2026-10-07 (heel.py strut_clearance_to_r2_tub: worn 1.176 / free 1.303 / jaw 1.29-1.34 vs 1.4; pad.py cross-check now uses the real tub, was 0.79 on the preview) -> owner ARM-6D", commit: 9999eed, st: "stale-closed 2026-10-08 (K4: strut clearance vs the shell_r2 tub; shell_k4 has K4_RELIEF=len -> K4-SHELLCHK)"}
  - {id: RB-2, rank: 8, cls: evidence, src: reg-board.md#2, dup: [00-whole risk 17], t: "no dielectric stack-up in the board file; sim/noise borrows the Rev E stack", close: "enter JLC 0.8 mm 4-layer stack (dated page read), re-run sim/noise if different", blk: none, st_r2: "done 2026-10-07 (evidence): jlcpcb.com/impedance (headless Chromium, 0.8mm tab clicked, read 2026-10-07) JLC04081H-3313 = Cu 0.035 / 3313 prepreg 0.0994 / Cu 0.0152 / core 0.5 / Cu 0.0152 / 3313 0.0994 / Cu 0.035; eps prepreg 3313 4.1, core 4.6. sim/noise default 0.0994/0.4804/0.0994, eps 4.05/4.6/4.05 differs only in core (0.4804 vs 0.5, +4 %) and prepreg eps (+1 %) -> small; sim/noise re-run NOT done, optional (update pcbgeom.py DEFAULT_STACKUP first). Other 0.8 mm options on the page: 2116B 0.1164/0.45, 1080 0.0764/0.55, 7628 0.2104/0.25", st: "stale-closed 2026-10-08 (K4: 0.8 mm 4-layer stack; K4 boards are 6-layer -> K4-STACK6)"}
  - {id: PHYS-8, rank: 9, cls: evidence, src: physical.md#8, dup: [RPB-10, 00-whole risk 18, D18], t: "pod mass >= ~9.5 g vs ~8 g target; two resin densities in sources", close: "mass from the r2 STLs with one density + parts + wires", blk: none, st_r2: "done 2026-10-07 (sim/checks/pod_mass.py: 11.2-13.2 g per side worn, pod body 8.7-10.1; c369d38) -> owner PHYS-8D", commit: c369d38, st: "stale-closed 2026-10-08 (K4: r2 mass 11.2-13.2 g superseded by pod_mass ULTRASONIC_DESIGN=k4: 9.05-10.15 g worn (d59f086))"}
  - {id: PROC-6R, rank: 10, cls: evidence, src: sub-processing.md#6, dup: [OUT-6], t: "research half of the fault cut-off question: can COMP/ADC watchdog reach TIM1 break internally on U575 (RM0456 TIM1 break sources [TBD])", close: "RM0456 read, options into the backlog for the owner", blk: none, st: "done 2026-10-07: ADC1(PA6)->MDF1 OLD->mdf1_break0->TIM1 BKCMP7E = CPU-independent break, no board change (RM0456 Rev 7 Table 541, §16.3.18); COMP out (PA6 not a COMP input); ocref_clr path rejected (ES0499 2.16.2)", commit: 4c1068b, k4: "U1 on P; result valid"}
  - {id: DK-17, rank: 11, cls: evidence, src: sub-dock-usb.md DK-17, t: "does the U5 ROM DFU need VBUS sensing? (corrected 2026-10-07: PA9 pin 30 IS USB_OTG_FS_VBUS, left NC)", close: "AN2606 read", blk: "still blocked 2026-10-07: st.com PDF unreachable even from headless Chromium (curl 000, chrome-error) -> owner/router DK-17D", st: "researched 2026-10-07: RM0456 allows software B-session override; AN2606 Table 199 shows PA9 as USART1_TX in ROM; USB-DFU path unproven", commit: 286623c, k4: "PA9 VBUS question now lives on P (hw/pod/k4); VBUS reaches P only as VBUS_SENSE via BM28 pin 26 and D+/D- 11/13"}
  - {id: PROC-9, rank: 12, cls: evidence, src: sub-processing.md#9, t: "SMPS 3 MHz synchronous or free-running (whine risk with /20 mic divider) unverified", close: "RM0456/DS read", blk: none, st: "done 2026-10-07: no SMPS clock/sync control in RM0456 Rev 7 (free-running, 3 MHz typ only); lever = REGSEL to LDO; spread needs the bench (E11)", commit: d2b66d5, k4: "valid; U1 + L1 on P"}
  - {id: VHB-TOL, rank: 1.5, cls: risk, src: "3M VHB 4914 TDS 2024-09 (found during UI-2)", t: "VHB 4914 thickness tolerance is +-15 % = +-0.0375 mm (TDS), but dims_r2.switch_stack() assumes +-0.025 [A]: the switch stack and pocket clearance are computed on a tolerance 1.5x too tight", close: "set the TDS value in dims_r2, re-run switch_stack + interfaces", blk: none, st: "done 2026-10-07 (fixed worst -0.198..+0.287, ceiling worst 0.082, F-gap slack worst 0.0125; selective fit unchanged)", commit: e158710, k4: "dims_k4 inherits dims_r2 switch/VHB stack? re-run with TDS +-0.0375 -> K4-SHELLCHK"}
  - {id: RB-TOL, rank: 13, cls: evidence, src: reg-pod-body.md#18, dup: [PHYS-18, SAI-15], t: "Phase-2 [A] tolerances (JLC outline +-0.2, NPTH +-0.05, VHB, resin, KMT022) undated; tolerances.md Rev-1 only", close: "dated sources, tolerances.md Phase-2 section", blk: none, st: "done 2026-10-07 (JLC capabilities: outline +-0.2, hole +0.13/-0.08, position +-0.075, board +-0.1; gauge-pin duct worst 0.115 -> 0.155 PASS; resin + KMT022 still [A]) -> owner SAI-15D", commit: 2a8744f, k4: "JLC outline/NPTH tolerances valid; mic-port duct numbers re-derive for M outer-face port (dims_k4)"}
  - {id: SAI-3, rank: 14, cls: evidence, src: sub-audio-in.md#3, t: "no acoustic mesh chosen (S8-mesh FAIL)", close: "pick a mesh with ultrasonic transmission data", blk: none, st: "done 2026-10-07 (analysis): Acoustex 042 at the hex-seat floor (mesh_pick.py: mean -1.2 dB, peak +18.5 -> +14.3 at ~56 kHz); hydrophobic treatment + coupon measurement + purchase (O21) remain", commit: "e5afdab", k4: "mesh pick valid; mic port now on M outer face"}
  - {id: DK-16, rank: 15, cls: evidence, src: sub-dock-usb.md DK-16, t: "dock wire gauge/type unchosen (only OD 0.8 specified; under-cell slack 0.8)", close: "pick <= 0.4 mm OD, record, fill check", blk: none, st_r2: "done 2026-10-07: enamelled 32 AWG VBUS/GND + 36 AWG D+/D-/CC (OD 0.249/0.160), flat 0.98 x 0.25 fits under the cell", commit: "24dfbda", st: "stale-closed 2026-10-08 (K4: dock wire gauge: no dock wires in K4 (own pads, ECR-0021/0019))"}
  - {id: DK-05, rank: 16, cls: evidence, src: sub-dock-usb.md DK-05, dup: [PHYS-3, PHYS-15, RB-5, RPB-7, DBG-17], t: "dock + cell wire route belly -> rear B pads not designed (slack for lid lift)", close: "wire-route sketch with gauges in physical.md", blk: none, st_r2: "done 2026-10-07 (dock wires, both pods: hw/mech/dock_route.py; v2 2026-10-07: worst 2.41 right / 0.58 left to the arm bundle, hold + check in physical.md step 11; cell leads wait PWR-I10)", note: "DK-16 done 2026-10-07", commit: "9268372", commit_v2: "bbdc7fe", st: "stale-closed 2026-10-08 (K4: dock wire route belly -> rear B pads: no dock wires in K4; cell leads still route (PWR-I10))"}
  - {id: ARM-LEFT, rank: 16.5, cls: risk, src: "found in DK-05 (2026-10-07)", t: "heel.py wire_route models only the right pod; in the left pod the board flips, arm pads sit low (z -7.4..-4.15) and the dock wires climb past the arm exit (0.11 mm)", close: "pod argument in heel.wire_route/route_checks (left = board y -> 12 - y), checks for both pods", blk: none, st: "done 2026-10-07 (left pod: pass_0.3 true, cut lengths 19.4-21.9; right unchanged; dock ribbon >= 0.114)", commit: "80c16a9", k4: "arm-wire half valid in shell_k4 (heel reused); dock-wire half moot; left-pod flip re-check on M/P -> K4-SHELLCHK"}
  - {id: UI-1, rank: 17, cls: evidence, src: sub-ui.md#1, t: "puck selective-fit procedure not written", close: "fit procedure in physical.md assembly order", blk: none, st: "done 2026-10-07 (physical.md step 9); test-build run = hardware; stuck flag = fw-agent", commit: 42f45db, k4: "SW1 pocket + puck selective fit reused in shell_k4; SW1 on M"}
  - {id: PAD-5, rank: 19, cls: risk, src: reg-pad.md#5, t: "closure pilot D0.95 in CAD vs D1.0 in hardware.md (92 % vs 74 % engagement, boss split risk)", close: "FASTENERS pilot 1.0 or ream note", blk: none, st: "done 2026-10-07 (pilot 1.0; pad.py: cavity-pilot wall 0.775 -> 0.75, nothing else changed)", commit: 186ea3b, k4: "pad unchanged by K4"}
  - {id: RPB-5, rank: 20, cls: evidence, src: reg-pod-body.md#5, dup: [PHYS-6, DK-07, PAD-3 research half, UI-4], t: "sealing note missing (O10 cites absent docs/research/sealing-and-service.md); spray-test plan", close: "sealing note + IPX4 test plan (test itself = hardware)", blk: none, st: "done 2026-10-07 (docs/research/sealing-and-service.md; membrane_loss.py: ePTFE membranes fail R14, hydrophobic open mesh instead); products + spray coupon remain", commit: "082fa70", k4: "sealing note valid; adds the 4 dock windows -> K4-WINDOW-SEAL"}
  - {id: RPB-14, rank: 21, cls: evidence, src: reg-pod-body.md#14, dup: [PHYS-14], t: "service procedures not in physical.md", close: "write Service section", blk: none, st: "done 2026-10-07 (physical.md Service: procedures existed; added lid-lift slack arm 2.65/3.04, dock 0.0 + 2 mm loops, tools; seam cycles = coupon)", commit: "1c298eb", k4: "Service section: BM28 unmate = new service path; physical.md update with ECR-0020 impl"}
  - {id: DBG-16, rank: 22, cls: evidence, src: sub-debug-test.md DBG-16, t: "no lid bond before DFU-via-stub passes on the bare board: gate not written into physical.md", close: "add the gate", blk: none, st: "done 2026-10-07 (physical.md step 8 gate)", commit: 42f45db, k4: "DFU gate valid; U1 on P, VBUS D+/D- via BM28"}
  - {id: RPB-16, rank: 23, cls: evidence, src: reg-pod-body.md#16, t: "stepped gauge pin D0.98/D0.50 not sourced", close: "source or turn; else ECR (2 NPTH + lid pins)", blk: none, st: "partly 2026-10-07: JLCCNC can't (min D3, +-0.05); rec A pin-gauge set + 20G hypodermic sleeve (worst 0.17 / selected ~0.12 vs 0.175); tube dims [A] until measured; purchase at freeze (O21)", commit: "3d8405b", k4: "gauge pin for M's mic port (outer face): re-derive"}
  - {id: DK-01, rank: 24, cls: hygiene, src: sub-dock-usb.md DK-01, t: "bom.md pairs the 5-pin target with a 4-pin head (C5126845); 5-pin mate stock 0", close: "fix bom.py; dated stock check of the 5-pin head", blk: none, st_r2: "done 2026-10-07 (bom.py/bom.md -> C5126847 5-pin; JLC stock 0 at 17:14Z, buy at order time; per pod $23.18 -> $22.50)", commit: "c7a5523", st: "stale-closed 2026-10-08 (K4: bom.py 5-pin YZT0675/C5126847 leaves the BOM (ECR-0021); head = 4-pin C5126845 (stock 46, 2026-10-08))"}
  - {id: PWR-I9, rank: 25, cls: hygiene, src: sub-power.md PWR-I9, t: "BQ25180 SLUSE99C + Renata V03 rows missing from datasheet-provenance.md", close: "add rows", blk: none, st: "rows done 2026-10-07 (+ VHB 4914 TDS); spec O12's docs/research/battery-and-charging.md still absent", commit: 167a4bb, k4: "provenance rows valid (U3 on M)"}
  - {id: CHK-STOCK, rank: 26, cls: hygiene, src: "bom_check stock-lock + lock-drift WARN", t: "8/31 LCSC numbers without lock rows (C25744 undated); D5/D6 C48260 only ALTERNATE; 12 RECOMMENDED rows for unused parts", close: "tools/jlc.py dated rows; prune lock", blk: none, st: "done 2026-10-07 (8 dated rows added via tools/jlc.py 17:35-17:36Z, C48260 promoted, 12 unused rows SUPERSEDED; bom_jlc_mz2.csv regenerated; bom_check lock-drift PASS, stock-lock only U1 stock 26 = ECR-0008)", commit: "8d38c68", k4: "K4 BOMs hw/pod/k4/bom_jlc_M.csv + bom_jlc_P.csv need dated lock rows -> K4-BOM-STOCK"}
  - {id: CHK-IDENT, rank: 27, cls: hygiene, src: "bom_check identity WARN", t: "8 wrong LCSC properties in superseded hw/pod/kicad-draft", close: "clean or delete the draft", blk: none, st: "done 2026-10-07 (LCSC Part stripped from 8 draft footprints; README note; bom_check identity PASS)", commit: "ca8a717", k4: "draft cleaned; K4 gen.py footprints -> K4-BOM-STOCK"}
  - {id: CHK-MODELS, rank: 27.5, cls: hygiene, src: "found in RB-9 (2026-10-07)", t: "KiCad 3D models: SW1 model 0.39 tall vs KMT022 datasheet 0.65; U2 (mic) has no model: renders and JLC 3D/DFM previews understate the tallest parts", close: "swap in correct models (easyeda2kicad by LCSC or a dimensioned box) in hw/lib, re-run board_in_pod.py", blk: none, st: "done 2026-10-07 (own datasheet placeholders, library footprints repointed; board_in_pod with real heights: SW1 0.21 to the pocket ceiling, U2 0.28 to the cell, PASS both pods; board embedded copies sync at the next layout pass)", commit: "b15c781", k4: "SW1/U2 models: re-check in K4 footprints"}
  - {id: RB-19, rank: 28, cls: hygiene, src: reg-board.md#19, dup: [CHK-VALUES], t: "74/74 board Value fields hold footprint names", close: "write schematic values into the routed board (no geometry change)", blk: none, st: "done 2026-10-07 (74 Value fields via pcbnew; bom_check values PASS; DRC unchanged)", commit: "d2e8793", k4: "Value fields for the K4 routed boards M/P -> K4-BOM-STOCK"}
  - {id: CHK-DRCWARN, src: "found in RB-19 (2026-10-07)", t: "routed board DRC warnings", st: "done 2026-10-07: 2 dangling vias deleted (d461bbf) + redundant +3V0 via d5fef857 and its stub deleted (keeps plane -> via -> C6 -> U1.9): DRC 0 violations / 0 unconnected / parity 0; noise smoke identical", blk: none, commit: "d461bbf, 670f8c1, 8b2adb8", k4: "K4 M routed 0/0; P open (router)"}
  - {id: ARM-7, rank: 29, cls: hygiene, src: reg-arm.md#7, dup: [PAD-10, UI-9, DK-13, DBG-10], t: "stale build notes (heel.md/pad.md/hardware.md/electronics.md/pcb-mech-interface.md/padboard gen.py docstring/learn scripts)", close: "update notes", blk: none, st: "done 2026-10-07 (route fixes 748ef61; values, VSYS comments, provenance SW1, superseded banners on 4 Rev-E notes)", commit: "748ef61, 55051d1", k4: "stale notes pass: K4 docs updated with ECR-0020/0021"}
  - {id: DIAG, rank: 30, cls: hygiene, src: "RB-10, PHYS-11, ARM-11, PAD-12, UI-10, SAI-12, DK-14, DBG-11, PROC-10", t: "stale/missing diagrams (Rev E pictures, arm-wiring, button stack, belly bay, test-access map, clock tree, pin map)", close: "redraw (render.sh, dark)", blk: none, st_r2: "partly 2026-10-07: arm-wiring.svg redrawn (ARM-11), button-stack.svg new (UI-10, generated), dock-cable.svg (DK-14 contact half), duct-section.svg (SAI-12), phase2-overview.svg (PHYS-11), test-access-map.svg (DBG-11), belly-section.svg (DK-14), all generated; u575-clock-tree.svg + u575-pin-map.svg (PROC-10, make_u575_maps.py, 2026-10-07); open: pad-board pad map (PAD-12), Rev E pictures (RB-10)", commit: "f3ec25a, 6ae9dc7", st: "stale-closed 2026-10-08 (K4: r2 diagrams (phase2-overview, belly-section, dock-cable, test-access-map ...) are Phase-2 pictures; K4 set -> K4-DIAG)"}
  - {id: RB-9, rank: 31, cls: hygiene, src: reg-board.md#9, dup: [PHYS-5], t: "which pod has which edge up is derived, not checked", close: "KiCad 3D render placed in the CAD for both pods", blk: none, st_r2: "done 2026-10-07 (hw/mech/board_in_pod.py: PASS both pods; findings: SW1 model 0.39 vs 0.65 datasheet, U2 has no model -> new CHK-MODELS)", commit: "ec63f80", st: "stale-closed 2026-10-08 (K4: board_in_pod PASS was for r2; K4 stack in pod -> K4-SHELLCHK)"}
  - {id: DK-09, rank: 32, cls: hygiene, src: sub-dock-usb.md DK-09, t: "cable side undocumented (plug, CC, length, strain relief)", close: "dock/cable note + diagram", blk: none, st_r2: "done 2026-10-07 (sub-dock-usb DK-09 + docs/diagrams/dock-cable.svg: USB-C plug with CC wired, rec; USB-A = 100 mA until enumeration)", commit: "6ae9dc7", st: "stale-closed 2026-10-08 (K4: USB-C cable side moot (O31); head cable = k4-dock.yaml)"}

  # decided by the coordinator 2026-10-07, doc parts done (moved from owner)
  - {id: RB-20, cls: decision, t: "R21 mid-board vs MZD-4 edge", opts: "accept (rec) / 0603 shunt at edge + wider Kelvin pour (router)", st: "decided 2026-10-07 (coordinator, decisions-log 9330d9c); accepted; doc updated (reg-board issue 20)", commit: "b73598d", k4: "R21 on P; decision stands"}
  - {id: OUT-6, cls: decision, dup: [PROC-6, PROC-6R], t: "bridge fault cut-off: always-on hardware break during playback, or self-test only", opts: "A ADC1->MDF1 out-of-limit->TIM1 break, always on in playback (rec; firmware-only, +0.15-0.34 mA + MDF clock) / B self-test-only over-current (today) / C software ADC1 guard (ISR latency, dies with the CPU)", st: "decided 2026-10-07 (coordinator, decisions-log 9330d9c); option A always-on MDF break; docs updated; FWSIM-R65 appended (dd9c6fb); implementation = fw-agent", commit: "dd9c6fb, b73598d", k4: "decision stands (MDF break on P)"}
  - {id: ARM-6D, cls: decision, src: reg-arm.md#6, t: "strut to real tub 1.176 mm (worn) vs SHROUD_CLEARANCE 1.4; binding = strut-relief chamfer at the cell's rear end, wall already at the 0.6 resin min", opts: "A accept 1.18 (rec; all wear states modelled; confirm with E12) / B move pad.py strut top 0.25 rear/outboard (re-solves strut + Ear clearance) / C deeper relief behind the cell only with a local 0.45 wall (below resin min)", st: "decided 2026-10-07 (coordinator, decisions-log 9330d9c); accepted 1.18 mm; docs updated (reg-arm 6, reg-pad 6)", commit: "b73598d", k4: "re-confirm on shell_k4 -> K4-SHELLCHK"}
  - {id: RPB-15, cls: decision, t: "SWD needs a peel after the lid bond", opts: "accept, DFU recovery (rec per DBG-16 gate) / TPs back on B (router)", st: "decided 2026-10-07 (coordinator, decisions-log 9330d9c); accepted; DFU gate already in physical.md step 8", commit: "b73598d", k4: "SWD pads on P (TP1-TP5): P faces the lid in the stack? check in physical.md"}
  - {id: RPB-4, cls: decision, dup: [CHK-SWITCH, UI lateral], t: "switch lateral stack 0.20 worst vs 0.15 (interfaces WARN, 0.05 over)", opts: "accept with selective fit / tighten board-lid tolerance (gauge pin also locates SW1) / larger bore", st: "decided 2026-10-07 (coordinator, decisions-log 9330d9c); selective fit (physical.md step 9); WARN kept visible", commit: "b73598d", k4: "switch lateral stack: SW1 on M, re-run switch_stack in dims_k4 -> K4-SHELLCHK"}

  # ---- K4 re-baseline 2026-10-08 (O33, ECR-0020/0021, V9-k4-board.yaml, k4-dock.yaml). rank_k4 = order of the OPEN unblocked work; rank above is the 2026-10-07 r2 order.
  - {id: K4-BM28-DS, rank_k4: 1, cls: risk, src: "ECR-0020 (mated height 0.6 [T], 0.3 A/contact [T], pin n mates n [T]); V9 open_items", t: "Hirose BM28 30-contact C424570 plug / C424571 receptacle: datasheet values never read (mated height decides the 3.9-4.3 stack vs 4.5 zone, margin only 0.2-0.6; contact current, retention, mating cycles, pin numbering, footprint)", close: "read the Hirose drawing/datasheet, fetch footprints (easyeda2kicad C424570/C424571), put numbers in V9 + sub-power", blk: none, st: "done 2026-10-08: Hirose BM28 catalog (Aug 2019) read via datasheet.lcsc.com/lcsc/C424571.pdf (curl with Referer lcsc.com; works, www.lcsc.com/datasheet/ is JS shell). 0.6 mm stacking height (no tol printed), signal 0.3 A/contact, 2 power contacts 5 A, 30 V, contact R max signal 100 / power 30 mohm, 10 mating cycles, no polarity, stencil 80 um. Footprints match land pattern bar plug pad width 0.15 vs 0.18 (left); plug courtyard +-0.42 -> +-0.90 fixed; pin n to pin n verified vs place_k4. Details V9 k4_bm28_ds_2026_10_08. Left: +-0.05 mated tol, mating force (customer drawing), 10-cycle limit vs K4-DOCK-CYCLES"}
  - {id: K4-DOCK-STRIP, rank_k4: 2, cls: risk, src: "k4-dock.yaml zero_growth cost: M strip fragile in handling", t: "dock tab (M strip beyond the stack, castellated pads): bending/crushing fragility", close: "hand calc in sim/checks/dock_strip.py", blk: none, st: "done 2026-10-08: pogo push-off is in-plane (column stress 0.16 MPa); y tip load to fail >= 111 N at 1.8 mm strip (33 N at 6 mm); castellation Cu 9.9 N vs 1.18 N push (8x, [A] Cu 25 um). Not bending: weak links are half-hole pad lift-off (keep the 0.15 annular ring) and panel handling; ENIG wear = K4-DOCK-CYCLES", commit: "(this commit)"}
  - {id: K4-SW1-PRESS, rank_k4: 3, cls: risk, src: "UI-2 (r2 FEM) re-point; ECR-0020 SW1 on M belly", t: "SW1 press (2 N) reacted by the M board with the P board stacked 0.6 over it: M outline, support and VHB differ from r2; KMT022 stroke 0.15+-0.1 may not survive", close: "re-run sim/checks/sw1_press_fem.py with the K4 M outline (hw/pod/k4/placement_M.yaml) and the lid/VHB support", blk: none, st: "done 2026-10-08 (SW1_BOARD=k4 sw1_press_fem.py): M 14x12x0.8, 2 N -> SW1 1.6-34 um vs min travel 50 um (stroke survives, 16 um margin soft case), VHB 23-59 kPa < 85; 10 N 114-297 kPa (as r2); P 0.2 above floor not loaded, BM28 plug tilt <= 1.5 mrad / 10 um lift; P-on-floor worst case 1.1-1.85 N via BM28 [A]. Evidence sim/out/mech/sw1_press_fem_k4*.json; docs sub-ui issue 2", commit: "(this commit)"}
  - {id: K4-LEDGE-PRESS, rank_k4: 3, cls: risk, src: "ECR-0022 ledge", t: "SW1 press with the VHB only on the 19 mm2 notched ledge tip", close: "sw1_press_fem.py K4 ledge mode + floor post (ECR-0023)", blk: none, st: "2026-10-08 UPDATE: compressible-pad replacement (sw1_pad_fem.py, Poron 4701-30 / HT-800) does NOT close: contact at all corners needs 2.36 mm pad, preload 1.6-5.6 N shifts SW1 31-107 um into the 70 um pre-gap, VHB 108-112 kPa; options in ECR-0023 addendum (recommend gap-filling dot bonded post), owner decides; LEAD DECISION 2026-10-08: gap-filling bonded post (ECR-0023 add.2): post printed 0.5875 short, epoxy dab + Kapton peel fills the real gap; FEM 2 N SW1 1.7-32 um, VHB <= 60 kPa (VHB E <= 0.5; E 2 needs shrink <= 0.5 %); k4_heights never_negative true. Supersedes the shim fit. ledge alone FAIL 2026-10-08 (SW1 6-153 um, VHB 113-187 kPa vs 85). FIXED by ECR-0023 (proposed): printed floor post on the U1 top under the BM28 line, shim/trim-fitted gap 0.015 +-0.015 (chain +-0.54 lin so a fixed post cannot work); FEM 2 N gap 0-30 um: SW1 4-34 um, VHB 7-62 kPa PASS (E <= 0.5; E 2 marginal gap <= 0.01); k4_heights floor_post PASS, floor +0.163 unchanged, pod T unchanged. Open: owner approve ECR-0023; bench check of epoxy shrink and Kapton peel and the BM28 housing stop load", commit: "(this commit)"}
  - {id: K4-ACO, rank_k4: 4, cls: risk, src: "ECR-0022 duct 0.95", t: "mic port acoustics with the ledge tube + VHB duct", close: "ULTRASONIC_DESIGN=k4 run_port.py", blk: none, st: "done 2026-10-08, PASS: mean +4.6 dB (MC p05 -0.1), notch -8.4 dB @26 kHz, peak +10.8 dB @44.4 kHz (r2 61-63 kHz); EQ target moves to ~45 kHz", commit: "(this commit)"}
  - {id: K4-STACK6, rank_k4: 4, cls: evidence, src: "RB-2 re-point; V9 6L option", t: "K4 boards are 6-layer 0.8 mm: sim/noise vertical_bplus.py and the layout use a 4-layer stack (JLC04081H); dated JLC 6L 0.8 mm stack-up + impedance not recorded", close: "read jlcpcb.com/impedance 6L 0.8 mm, update sim/noise/pcbgeom.py DEFAULT_STACKUP, re-run vertical_bplus.py (nominal 12.7 dB, pessimistic 4.8 dB leak margin)", blk: none, st: "done 2026-10-08 (re-run both splits: 26.4 / 26.2 dB worst corner; V9 + k4-release README updated)", st_done: "2026-10-08 evidence: JLC publishes no 0.8 mm 6L stack-up (impedance page lists 1.2/1.6/2.0 only; 0.8 mm 6L is orderable); recorded in V9 k4_mic_filter + ECR-0020 rev 5; k4_noise.py has two bounding splits (0.2 dB apart) and the corrected P geometry; with the R30 filter worst corner 26.4 dB. Optional: ask JLC for the 0.8 mm build at order time", st_prev: "partial 2026-10-08: sim/noise/k4_noise.py ran the REAL routed P+M geometry with an assumed uniform 6L stack: F02 SMPS -> MIC_VDD worst-PSRR margin 4.6-14.4 dB (today 18.6, sign-off >= 10) = MARGINAL, all else PASS (V9 k4_post_route). JLC 6L impedance page still unread; conduction through BM28 still K4-CONDUCT"}
  - {id: K4-SHELLCHK, rank_k4: 5, cls: evidence, src: "re-points RPB-12 ARM-6 VHB-TOL RB-9 ARM-LEFT ARM-6D RPB-4", t: "r2 checks never re-run on shell_k4/dims_k4: seam rebate >= 0.4, strut clearance (K4_RELIEF=len), VHB +-15 % in switch_stack, left-pod flip, board-in-pod with M/P heights, switch lateral stack", close: "re-run hw/mech checks with ULTRASONIC_DESIGN=k4; write results to reg-pod-body", blk: none, st: "done 2026-10-08 (sim/checks/k4_shellchk.py; heel.py HEEL_TUB=k4; dims_k4.switch_stack reuses dims_r2): strut 1.176 = r2; switch stack/VHB +-15 % = r2 PASS; FIXED dims_k4 MIC 1.75 / SW 5.3 (SW was 2.7 mm off the routed M); FAIL open: M 14.05 long vs STACK_L 11 (pod +3.05 or shorter M, owner/router); WARN: rebate 0.1x0.4 residual wall 0.5 < 0.6, floor clear worst -0.038, lateral 0.225 vs 0.15 (RPB-4 selective fit); heel wire_route is r2-frame only (K4 arm-wire route open). FOLLOW-UP 2026-10-08: dims_k4.STACK_L now reads routed_P/M Edge.Cuts (max, else placement yaml L, else 11; K4_STACK_L overrides; pod L = 38.15 + stack: 14.0 -> 52.15, 15.0 -> 53.15, 16.0 -> 54.15, current routed M 15.5 -> 53.65); WARNs fixed at 0 L/T cost: rebate ridge (residual 0.6), F_GAP 0.30 -> 0.25 (floor worst +0.012), BORE 2.6 -> 2.8 (lateral 0.225 <= 0.25); K4 wire routes modelled (dims_k4.wire_routes, pads J4/J5/J9 cell, J7/J8/J1/J2 arm via 8.4 lane under cell to heel exit; clash 0; ASSUMPTION P keeps a solder window at the pads). Evidence sim/out/mech/k4_shellchk.json, reg-pod-body K4 shell checks", commit: "(this commit)"}
  - {id: K4-CONDUCT, rank_k4: 6, cls: evidence, src: "V9 B_plus_noise: A6 conduction through BM28 unmodelled; +3V0 3 x ~50 mohm [T]", t: "+3V0 drop and ground-return noise through 3 BM28 +3V0 contacts and 14 GND contacts under 0.33 A bridge peaks (C14 on P)", close: "extend sim/noise/vertical_bplus.py with contact R from K4-BM28-DS", blk: none, st: "done 2026-10-08: sim/checks/k4_conduct.py (Hirose BM28 catalog Aug 2019: signal 100 / power 30 mohm max): +3V0 drop 5.9 mV (18.5 mV tabs dead) at 326 mA peak; mic-supply conduction margin >= 17 dB pessimistic (worst A08 LED PWM); no extra pins. Evidence V9 k4_conduct_2026_10_08, reg-board K4 section. Bench: measure contact R", commit: "this commit"}
  - {id: K4-HEIGHTS, rank_k4: 7, cls: evidence, src: "V9 open_items: QFN48 ~0.6 [T], C14 0603, U3 BGA <= 0.6 assumed", t: "part heights not read; stack 3.9-4.3 vs 4.5 zone depends on them", close: "read datasheets (U1 STM32U575 QFN48, U3 BQ25180, C14), recompute stack in dims_k4", blk: none, st: "done 2026-10-08 (sim/checks/k4_heights.py; V9 k4_heights_2026_10_08): floor side PASS (L1 1.0, 0.86 worst of 1.35); inner 0.6 gap PASS but 0.00 worst on C16/C17/C9; LID SIDE FAIL: 12 M file-B parts vs the 0.25 VHB under a flat lid (C21 0.9) -> fix A lid ledge 0.84, pod T unchanged, needs owner/ECR; heights are package-max [T], datasheets not fetched -> K4-BM28-DS + new K4-LIDLEDGE"}
  - {id: K4-LID-LEDGE, rank_k4: 7, cls: evidence, src: "ECR-0022/0023", t: "Lid ledge 0.70, 0201 gap caps, SW1 glue post (84a215d), heights re-verified 2026-10-08 (lid +0.112, floor +0.163). C9/C17 curves moved to queue A-CAP-CURVES + release gate", st: closed}
  - {id: K4-BOM-STOCK, rank_k4: 8, cls: hygiene, src: "re-points CHK-STOCK CHK-IDENT RB-19", t: "hw/pod/k4/bom_jlc_M.csv + bom_jlc_P.csv: no lock rows, Value fields on the routed M board, BM28 and C5126845 stock (Ext; 20k/737/46 on 2026-10-08)", close: "tools/jlc.py dated rows, bom_check on the k4 BOMs, Value fields after P routes", blk: none, st: "done 2026-10-08: .pcba-workflow/k4-sourcing-lock.csv 40 lines validated 0 errors (build_lock.py, live jlc.py 12:17Z: BM28 receptacle 717 / plug 19972, C5126845 46); BOMs now all in lock; gen.py writes values_{M,P}.json + place_k4.py applies them at next placement (routed boards untouched, no re-place here); alternates qualified, none swapped"}
  - {id: K4-DOCS-MPLANE, rank_k4: 9, cls: hygiene, src: "k4-dock.yaml open_items: M mid-plane y 6.8 not in docs/system; plm status", t: "M mid-plane y 6.8 and M parts on the floor face only must be in reg-board / physical; clear `tools/plm.py status` after ECR-0020/0021 (suspect relations: ECR-0020 relations still unchecked)", close: "docs update + plm review", blk: none, st: "done 2026-10-08 (docs): reg-board + physical updated, plm 0/0; FINDING: after ECR-0022 the pads sit at y 7.95-8.75, windows at 6.2-7.4, overlap 0 (sim/checks/k4_mplane.py) -> K4-DOCK-YALIGN", commit: "this commit"}
  - {id: K4-DOCK-YALIGN, cls: risk, blk: none, decided: "lead 2026-10-08: A (technical; head overhang only while docked, never worn O32); assigned to the floor-post shell agent", src: "found in K4-DOCS-MPLANE 2026-10-08", t: "dock windows/magnets at y 6.8 but M mid-plane is 8.35 after ECR-0022 (lid-side M): pads miss windows by 1.55 mm; M has parts on both faces", opts: "A move DOCK_YC to 8.35 in dims_k4/shell_k4 (rec; shell-only; head overhangs lid side 1.1 mm, never docked worn) / B swap stack order, M floor-side (mid 6.95; re-does SW1, mic, ledge, heights) / C stepped tab board (rejected)", close: "owner picks; shell agent edits dims_k4; re-run k4_mplane.py (must exit 0), k4_shellchk", st: open, st: "done 2026-10-08: dims_k4.DOCK_YC = Y_F - PCB_T/2 (8.35, derived from the board stack); k4_mplane.py exit 0 (pad/window overlap full); windows open resin 0; walls 0.6 min kept (cavity+0.6 outside 0 mm3); boss clipped at the seam (lid clash 0.085 -> 0). CLOSED 2026-10-08 (K4-WIRE-LANE): lane moved to one z (-8.8), y 8.85..9.51 spacing 0.22, single drop column DROP_X 30.86 (between boss edge and cell face 31.0): clash arm_wires/boss 0, magnet 0, tub/arm_wires 0, walls 0; was grazing the rear magnet/boss (x 28-31): wires x boss 0.021, x magnet 0.005, tub x wires 0.011 mm3 - lane z/route needs a nudge; head 6.86 centred on 8.35 spans y 4.92-11.78 vs pod 4.3-10.7 (overhang 1.08 docked only)", commit: "(this commit)"}
  - {id: K4-BRINGUP, rank_k4: 10, cls: evidence, src: "re-points ECR-0010 RB-4", t: "docs/build/bringup.yaml (40 steps) is the r2 board: needs K4 steps (BM28 mate/continuity, dock pads + head, L1 acoustic buzz check, 2-board DFU path)", close: "rewrite for K4", blk: none, st: "done 2026-10-08: docs/build/bringup.yaml stage K, steps K1-K10 (50 steps total, gates G6/G7) with meter values from netlist/datasheets; bringup.md regenerated; 2-board DFU path = D2-D4 on the mated stack (K5)"}
  - {id: K4-DIAG, rank_k4: 11, cls: hygiene, src: "re-points DIAG RPB-9", t: "K4 diagram + render set (stack section, dock section, BM28 map) after the ECRs are implemented", close: "docs/diagrams/ + render dump", blk: none, st: "done 2026-10-08: docs/diagrams/k4-stack-section, k4-dock-section, k4-bm28-map (.svg, make_k4_diag.py); k4-review stack-iso/stack-section and k4-shell-* re-rendered from the current boards"}

stale_closed:   # listed open in a doc but already fixed; close in the doc
  - {id: RB-18, src: reg-board.md#18, t: "DRC rules in untracked routed.kicad_pro", evidence: "git ls-files: hw/pod/draft_r2/out/routed.kicad_pro tracked (B-DOC-AUDIT-0007 item 4)", st: "closed in doc 2026-10-07", commit: 3b8fa36}
  - {id: SAI-14, src: sub-audio-in.md#14, t: "MC on disk n 40 vs log n 60", evidence: "sim/acoustics/out/port_results.json phase2 MC n 60 (B-DOC-AUDIT-0007 item 6)", st: "closed in doc 2026-10-07", commit: 3b8fa36}

owner:   # decisions; spec §0: options + rec live in the source doc or here
  - {id: ECR-0005, dup: [OUT-3, PWR-I1, CHK-RAILS], t: "U4 300 mA vs 326 mA +3V0 peak", opts: "A OUT-07 clamp + capped self-test (rec) / B 12 ohm exciter (E1) / C bigger LDO", blk: "owner (+hardware E1)"}
  - {id: ECR-0009, dup: [OUT-12, PWR-I5, DBG-12, 00-whole risk 6], t: "no output while docked vs docked self-test", opts: "a capped self-test exemption <= -12 dBFS (rec) / b sweep on battery, read back", blk: owner}
  - {id: ECR-0014/15/16, t: "simplification packages A/B/C still 'proposed'; superseded in practice by ECR-0018 (O25/O26)", opts: "close as superseded (rec) / keep open for the cherry-picks not in MZ-2", blk: owner}
  - {id: ECR-0018, t: "Phase-2 MZ-2 approved, implementation in progress, owner review in 1-2 weeks", blk: "owner (A-PHASE2-REVIEW)"}
  - {id: UI-5, t: "gesture model holes", opts: "A spec + timings / B short=mode, double=vol, hold=Off (rec) / C three holds", blk: owner, packet: "in packet 2 (coordinator, 2026-10-07)"}
  - {id: UI-8, dup: [PAD-13, ARM-8, 00-whole risk 3], t: "PB7 unprotected; pad-board LED_K 0.45 mm from OUT_B", opts: "A reorder pad-board pads / B R14 split / C both (rec)", blk: owner}
  - {id: PAD-1, dup: [PHYS-9], t: "contact face 50 mm2 vs O16(4) 100-150", opts: "A Sugru over whole cup face (rec) / B grow cup / C pre-made", blk: owner, packet: "in packet 2 (coordinator, 2026-10-07)"}
  - {id: PAD-3, t: "pad sealing", opts: "A dry test build, RTV final (rec) / B gasket / C pot", blk: owner}
  - {id: PAD-9, t: "pad board panel vs separate order", blk: "owner (JLC quote)"}
  - {id: SAI-4, t: "acoustic coupons vs O9", opts: "a JLC coupon panel / b rev-1 board + printed lids (rec) / c both", blk: owner}
  - {id: PROC-11, t: "SMPS inductor DFE201610E vs spec D5 LQM21PN", blk: "owner (spec or schematic)"}
  - {id: PROC-12, dup: [DBG-4], t: "O18 spare pins without pads (PA3 could sense VSYS)", blk: owner}
  - {id: PROC-2, dup: [ECR-0008], t: "MCU stock 8 at JLC; reserve vs U585 drop-in", blk: "owner (O21)"}
  - {id: PROC-3, t: "C7 CIN > 2 mm from pin 21", blk: "owner review O25"}
  - {id: DK-04, t: "sealed-pod update path", opts: "A write-protected boot stub + ROM DFU (rec) / B dual bank / C SWD-only", blk: owner}
  - {id: DK-10, dup: [A-USBC-SPACE], t: "USB-C fallback space not in shell_r2", opts: "clip-on adapter outside the pod (rec) / re-add keep-out", blk: owner, packet: "in packet 2 (coordinator, 2026-10-07)"}
  - {id: DBG-1, t: "first-flash path", opts: "B DFU-first (rec) / C DFU + probe (FWSIM rec) / A probe", blk: owner}
  - {id: DBG-3, dup: [RB-8], t: "panel / snap-off frame for 30 x 12", opts: "A header tab / B no-wire jig on tooling holes (rec) / C none", blk: "owner (O9)"}
  - {id: PWR-I3, t: "charger watchdog policy B (triage default) awaits the safety packet", blk: "owner (A-SAFETY-REVIEW)"}
  - {id: PHYS-8D, src: physical.md#8, t: "mass 11.2-13.2 g per side worn vs ~8 g target (D18); cell 4.2 g is 37 %", opts: "A (rec) decide after the owner's ~12 g wear test (A-TODAY-MASS-TARGET): if comfortable, set the ceiling ~12.5 g and accept / B trim inside the design: drop the armour plate (A-PHASE2-REVIEW Q2), lighter dock target (weigh it) / C smaller cell (drastic K1; runtime cost)", blk: owner}
  - {id: UI-3, src: sub-ui.md#3, t: "SW1 nub D1.0 = C&K minimum; C&K KMT0 sheet (2018-03-21, SHA a7791d9888a26610): 'recommended to enlarge this diameter to a full flat surface covering the switch'", opts: "A keep D1.0 nub (central load even when the puck tilts in its 0.3 bore clearance) / B (rec) D1.6 nub: closer to C&K's recommendation, still central within +-0.8 / C flat D2.3 foot (= the puck; max without a flange, a pocket flange would need < 0.082 worst ceiling clearance): best match to C&K, but a tilted puck presses the dome off-centre", note: "click feel = owner's domain; print all three in the puck kit and let her press them (test build)", blk: "owner (feel) + bench"}
  - {id: Q-A-SAFETY-REVIEW, t: "ECR-0013/0009 safety read vs SLUSE99C", blk: owner}
  - {id: Q-B-FOSS-INSTALL-DEFAULT, t: "FOSS install rule reading", blk: owner}
  - {id: Q1-K1, t: "packet Q1: K1 (130 mAh) built as a NON-DEFAULT variant 2026-10-07 round 10 (ULTRASONIC_DESIGN=k1|k1p; docs/diagrams/k1-vs-phase2.png). k1 (plate off): T 9.1 / -16 % / R14 duct-peak FAIL at 78.7 kHz; k1p (plate kept): T 9.6 / -13 %, duct = phase2. Synthesis T 8.5 also needs 0.6 walls + lid 0.6", opts: "A k1p (lowest risk, T 9.6) / B k1 + duct fix (keep a 0.7 bore: shallower hex seat or an inner boss; T 9.1) / C stay phase2 (175 mAh, T 10.4)", blk: owner}
  - {id: Q2-DUCT-THINLID, t: "plate off (lid 1.0, k1 or phase2): mic duct R14 FAIL (bore 0.2). Built options round 11: seat 0.3 restores R14, MC all-pass 0.75 vs Phase-2 0.63 (docs/diagrams/duct-options.svg)", opts: "A rec: seat 0.3 + skin recess 0.1 (puck guide 0.30) (RECOMMENDED) / B seat R1.2 x 0.3 (best nominal peak, smaller mesh) / C outer boss 0.5 (= Phase-2 duct, local bump)", blk: owner}
  - {id: Q2-WALL06, t: "0.6 wall coupon: print + home tests T1-T6 (hw/mech/notes/coupon_wall06.md); decides k1t walls/chamfer/groove/rebate", blk: "owner print (hardware)"}
  - {id: Q2-BUTTON-THIN, t: "K1-thin (0.6 lid) button: the KMT022 stack breaks through. Built round 12 (docs/diagrams/button-concepts.svg): A dome flush, all shell checks pass in k1t; C proud skin needs no board change; B resin window / D side switch / E B-face rejected with numbers", opts: "A Phi4 metal dome (HYP 600-415S, LCSC C256252 150 gf / C256257 250 gf, cents each; 2026-10-07T21:36Z) on new F pads (F-copper local edit + DRC, dome hand-placed after reflow), flush, crisp click (RECOMMENDED) / B skin 0.20 proud straight over KMT022 + selective nub dot: no board change, soft bump / C keep a 1.0 lid (k1 rec, T 9.1) and skip K1-thin", note: "feel = her call: buy a 150/180/200/250 gf dome set with the freeze order (O21) and press them through a skin coupon", blk: owner}

hardware:   # parts / bench / built board (O21: nothing ordered before freeze)
  - {id: FMAC-RM-UNKNOWNS, src: "docs/research/drastic/V5-fmac-cordic.yaml rm_facts.unclear; fw/core/fmac_model.c A1/A2 (2026-10-07)", t: "RM0456 Rev 7 does not say how the FMAC's 16x16 product enters the 26-bit q4.22 accumulator (A1) or how bits are dropped at the q1.15 output (A2); the firmware model assumes floor for both. Read-back on a real U575 (Nucleo-U575 or rev 1), FIR with P=1 tap, CLIPEN=1, 8 inputs x = 0x0001, 0x007F, 0x0080, 0x00FF, 0xFFFF, 0xFF81, 0xFF80, 0xFF01: TEST A1 (output exact: R=7, b0=0x0001): expected under floor 0,0,0,0,-1,-1,-1,-1 (truncation toward zero gives 0 for all); TEST A2 (product exact: R=0, b0=0x0100): expected under floor 0,0,1,1,-1,-1,-1,-2 (truncation gives 0,0,1,1,0,0,-1,-1). `python3 sim/fw/fmac_model.py --bench` prints these expected words; a mismatch -> change A1/A2 in fw/core/fmac_model.c and the Python twin, re-run fwsim (L0, L2, D17)", blk: "hardware (any STM32U5 board; O21)", k4: "valid, U575 unchanged"}
  - {id: E2-ALGO, src: "docs/sim/firmware-emulation.yaml FWSIM-R13 status; sim/fw/l2.py (2026-10-07)", t: "E2 listening test must choose the algorithm variant with these sim facts in hand: slim B (16 bands, 1.28 ms frames; fits ~44 MHz only as V4's tuned kernels) misses T2 bat-call recall 0.65 vs >= 0.80 - in the Python reference too, so it is the algorithm, not the port; algorithm A (heterodyne 38 kHz) misses EVERY FM bat call (recall 0) in Python and firmware with the old 575-tap decimator, and recalls 0.39 (still < 0.80) in both since the 16+40-tap cascade (lead decision 2026-10-07); spec B passes (0.83) but costs 94-119 MHz static in today's firmware (V4 floor 59-69)", opts: "A spec B at P80/P160 clock (rec until E2) / B slim B if her ears accept fewer bands and the recall loss / C A only as a tone-finder fallback", blk: "hardware (E2 listening, owner ears)", k4: "valid"}
  - {id: ECR-0006, t: "weighted dummy pair wear + joint flex test", k4: "valid; dummy pair mass: use pod_mass k4"}
  - {id: ECR-0007, dup: [OUT-2, PAD-2], t: "exciter E1 coil R/L, E2 listening", k4: "valid"}
  - {id: ECR-0010, t: "bring-up plan + firmware tested before order", note: "firmware half = fw-agent", st: "plan half done 2026-10-07 round 9: docs/build/bringup.yaml/.md (40 steps, gates G0-G5); every hardware entry below maps to a step via its `closes` list", k4: "bring-up plan is r2; K4 two-board steps + BM28 + dock needed -> K4-BRINGUP"}
  - {id: OUT-4, t: "JLCDFM verdict on Q1/Q2 0.15 mm gaps; 0.10 mm stencil", note: "needs the owner's JLC account", k4: "Q1/Q2 on P; JLCDFM needs both K4 boards"}
  - {id: OUT-5, t: "C14 X5R sing risk (S2/E7 listening)", k4: "C14 on P"}
  - {id: OUT-7, t: "dead time on the real Nexperia part", note: "or a browser-fetched model", k4: "valid"}
  - {id: OUT-8, dup: [SAI-8, MP-01], t: "PWM shaper noise into mic band: bench coupling", k4: "valid; bridge on P over the mic board (V9 B+ model)"}
  - {id: PWR-I4, t: "RT1 reads hot near U3: log TS vs thermocouple", k4: "RT1 near U3 on M"}
  - {id: PWR-I7, dup: [DK-06, DBG-6, PROC-8], t: "USB at +3V0 2.955 V: bench enumeration + DFU", k4: "USB D+/D- cross BM28 pins 11/13 and the dock pads"}
  - {id: PWR-I10, t: "cell lead exit, self-discharge, D4 drop, real charge time, E4 currents", dup: [PHYS-10], k4: "cell pad J5 on M; cell - shares J4 with the dock GND (ECR-0020 ASM-09 access check)"}
  - {id: PWR-I12, dup: [00-whole risk 13], t: "board + cell temperature through a full charge (ECR-0009 item 3)", k4: "valid"}
  - {id: PWR-I15, t: "Off-current bench measurement", note: "firmware sequence = fw-agent", k4: "valid"}
  - {id: DK-02, t: "dock contact order + magnet keying (sample)", k4: "merge with K4-MAG-HEAD: caliper a C5126845 head sample (pitch/polarity/stroke/tip/wire order)"}
  - {id: DK-03, t: "dock target envelope (caliper a sample)", st: "stale-closed 2026-10-08 (K4: YZT0675 target envelope: target replaced by own pads (ECR-0021) -> K4-MAG-HEAD)"}
  - {id: DK-11, t: "dock magnets near L1: E11 whine on the right pod", k4: "magnets now D2.5 N52 at pod x 20.65/33.85 (zero-growth) beside L1 on P: E11 whine check"}
  - {id: SAI-5, t: "mic clock duty (scope R2.2)", k4: "mic clock PB3 crosses BM28 pin 3"}
  - {id: SAI-6, t: "RSFLT at 800 kHz swept tone", k4: "valid"}
  - {id: SAI-7, t: "MIC_VDD self-noise capture", k4: "MIC_VDD crosses BM28 pin 6"}
  - {id: SAI-11, t: "PB4 back-feed in reset/DFU: meter", k4: "valid"}
  - {id: SAI-13, t: "mic-port EQ notch constant refined from a bench sweep (r2 63.0 kHz Q6.4 -11.5 dB; K4 44.4 kHz Q6.8 -10.8 dB)", k4: "firmware variant-selectable 2026-10-08 (fw/variants.yaml mic_notch, folded into FW_DSP_EQ2, ULTRASONIC_DESIGN=k4); bench sweep refinement still open"}
  - {id: DBG-8, t: "ROM DFU pauses charging: check with a cell", k4: "valid"}
  - {id: RB-4, dup: [OUT-9 J-pad, 00-whole risk 1], t: "meter adjacent J pads in bring-up step 1", st: "stale-closed 2026-10-08 (K4: r2 J-pad adjacency meter step; K4 pad set differs (TP1-TP5 on P, dock pads on M) -> K4-BRINGUP)"}
  - {id: RPB-17, t: "600k-press + drop coupon (MZD-7) + 1.6 N kitchen-scale press test (UI-2 bench half)", note: "analysis done (UI-2)", k4: "SW1 on M belly; coupon + press test re-point to shell_k4"}
  - {id: UI-7, t: "LED VF at 0.1-1 mA", k4: "LED_K crosses BM28 pin 30"}
  - {id: ARM-1R, t: "heel exit dry fit with the real cell", k4: "heel reused in shell_k4"}
  - {id: ARM-2, t: "pad force dip on jaw opening; option pick after E12", opts: "A ~5 mm set (rec if k_t <= 5 N/mm) / B 0.85 wire / C deeper + saddle", k4: "valid"}
  - {id: ARM-3, t: "wire diameter: buy 0.8/0.85, pick on bench", k4: "valid"}
  - {id: ARM-4, t: "unloading plateau coupon", k4: "valid"}
  - {id: ARM-5, t: "short flare 100-cycle test (or STRUT_START 3->4 CAD option)", k4: "valid"}
  - {id: ARM-9, dup: [ARM-10, PAD-7], t: "E9 temple + Ear (open) clearance at true scale", k4: "valid; pod L 49.15 in K4"}
  - {id: PAD-4, t: "tight fits: dry fit + shims", k4: "valid"}
  - {id: PAD-8, t: "LED polarity in JLC placement preview (order time)", k4: "valid"}
  - {id: PAD-11, t: "LED faint glow when off: fix if seen", k4: "valid"}
  - {id: Q-A-PHYSICAL-FIRSTWINS, t: "E1/E2/dummy wear", k4: "weights per pod_mass k4"}

  - {id: K4-MAG-HEAD, cls: risk, src: "k4-dock.yaml CALIPER_FIRST, polarity_keying; ECR-0021 [T]", t: "head C5126845 sample: magnet centre pitch (guess 13.2), polarity of each magnet (needs alternating for keying; else key by net order, harmless), pogo stroke/tip diameter, wire order; magnet N52 D2.5x1.0 sourcing", note: "merges DK-02; blocks the shell_k4 freeze (HEAD_MAG_PITCH), O21", blk: "hardware (sample; O21)"}
  - {id: K4-L1-BUZZ, cls: risk, src: "V9 B_plus_noise: MLCC/L1 audible-band buzz 2-3 mm from the mic port is acoustic, not in the model", t: "L1 and MLCC piezo/magnetostrictive buzz at load steps coupled to the mic port: tap/acoustic test before freeze (V9 rec d)", note: "mitigate: no MLCC on the switch/VSYS loop above the port, soft mount", blk: "hardware (built stack)"}
  - {id: K4-WINDOW-SEAL, cls: risk, src: "k4-dock.yaml sweat/seal; ECR-0021 [T]", t: "4 belly windows over the castellated pads: seal fillet from the cavity side + sweat leakage VBUS-D- (1.6 mm, ~5 V)", note: "re-points RPB-5; spray coupon", blk: "hardware"}
  - {id: K4-DOCK-CYCLES, cls: evidence, src: "k4-dock.yaml finish: ENIG 2-5 u-in", t: "contact R after 200 dock cycles (pogo on ENIG half-holes)", blk: "hardware"}
  - {id: K4-BM28-BENCH, cls: risk, src: "V9 hand_rework: fragile 0.35 mm B2B, shock/pull-out [T]", t: "BM28 mate/unmate force, retention under drop (worn pod), repeat-mate", blk: "hardware (O21)"}

router:   # needs placement/re-route (forbidden to parallel agents)
  - {id: SAI-15D, src: sub-audio-in.md#15, t: "D0.6 mic-port NPTH finishes 0.52-0.73 at JLC: below spec section 8 hole rule 0.6-1.0", opts: "A D0.6 + JLC press-fit +-0.05 (0.55-0.65, still 0.05 under) / B (rec) D0.65 + press-fit (0.60-0.70, duct limit 0.175 vs pin 0.14 PASS; footprint hole edit only, re-run acoustics) / C D0.7 regular (pin worst 0.205 > limit 0.15: fails)", blk: router, packet: "in packet 2 (coordinator, 2026-10-07)", commit: "b73598d", st: "done 2026-10-07 round 8: Port0.65 footprint, hole D0.65 at (1.90, 6.0) (0.2075 to pad 3), press-fit order note; acoustics MC60 mean +5.93 dB (was +5.58), R14 all-pass 0.63 (was 0.70)", k4: "mic port NPTH is now on M (hw/pod/k4/placement_M.yaml); same D0.65 rec; M routed 0 DRC, edit footprint at next M pass"}
  - {id: DK-17D, t: "ROM DFU VBUS sensing insurance: PA9 (USB_OTG_FS_VBUS) is NC", opts: "A (rec) add a 0201 series R DOCK_VBUS -> PA9 at the next layout pass / B read AN2606 in a browser first, add only if needed / C leave NC, test at bring-up step 6 (QFN bodge hard)", blk: "router + owner review (O25)", st: "BLOCKED 2026-10-07 round 8: not routable locally (14 passes + hand escapes; U1 bottom-row fan-out full); options in reg-board issue 22: A full re-route / B AN2606 read + bring-up test / C free a pocket at the next placement round", k4: "PA9 on P; P has 8 open + 6 near (another agent routing P); decide after P routes"}
  - {id: OUT-1B, t: "add option (B) offset resistor 100k +3V0 -> I_SENSE (0201) in gen.py + place/route near R22/C22; required by the verified option D (sim/checks/selftest_lockin.py)", st_r2: "done 2026-10-07 round 8: R23 1M (3.0 uA; 100k drew 29.7 uA > Off budget) at (19.2, 5.15) B, local re-route; DRC 0/0/0, smoke PASS", st: "stale-closed 2026-10-08 (K4: done on the r2 board; R23 offset resistor on P in K4 gen.py (check present))"}
  - {id: DBG-2, t: "TP row +3V0 beside GND (TP4|TP5 0.8 mm): reorder at the next placement edit", st_r2: "done 2026-10-07 round 8: TP2 SWCLK / TP4 +3V0 swapped (row GND, SWCLK, +3V0, SWDIO)", st: "stale-closed 2026-10-08 (K4: r2 TP row; K4 TP1-TP5 on P: row order re-check at P placement)"}

  - {id: K4-J4-ACCESS, t: "cell - shares dock GND pad J4 (ASM-09): can the cell leads reach J4 physically on M (ECR-0020 'check at placement')?", opts: "decide at the M pass", blk: "router (M placement)"}
  - {id: K4-P-ROUTE, t: "board P 8 open + 6 near unrouted (427315a); another agent routing", blk: none, st: "done 2026-10-08: 5-part unload P->M + BM28 pins 26/27 swap (ECR-0020 rev 4); M and P both 0 unconnected / 0 DRC / place PASS at L15.5 (hw/pod/k4/routed_P.kicad_pcb, routed_M.kicad_pcb). Solder window (--win) not done: U1 must move and near rules fail"}

fw_agent:   # owned by the firmware agent (fw/, docs/sim/firmware-emulation.yaml)
  - {id: PROC-4, dup: [UI-6], t: "idle plan Run vs Stop 2 + ADF + LPDMA (also LED PWM in Stop 2)"}
  - {id: PROC-5, t: "CPU budget re-cost for U575 / 800 kHz PWM"}
  - {id: PROC-7, t: "boot stub + self-test design note (self-test-firmware.md missing)"}
  - {id: PWR-I2, t: "charger register plan (TS_HOT, ICHG)"}
  - {id: PWR-I13, dup: [DK-09 ILIM half], t: "ILIM 100 mA until enumeration"}
  - {id: Q-B-FW-LIMITER, t: "true-peak limiter (e2e ceiling FAIL)", st: "done 2026-10-07 (host): fw/core/dsp.c true-peak limiter on the x16 stream; L2 T2/D17.ceiling_true_peak_dbfs -12.00; FWSIM-R15 1.36e6 hops 0 violations"}
  - {id: Q-B-FW-DSP-60S, t: "gate rule, transient mode"}

item_dep:   # waits on another item
  - {id: RPB-9, t: "r2 render dump + STEP export", blk: "item:ECR-0018 owner review edits", st: "stale-closed 2026-10-08 (K4: r2 render dump; K4 dump after ECR-0020/0021 implemented (K4-DIAG))"}
  - {id: RPB-13, t: "seam corner butt joints: sealant bead or corner key", blk: "item:RPB-5 (sealing note) -> note done 2026-10-07: rec = RTV fillet bead in each corner (S2); confirm on the spray coupon (hardware)", k4: "corner joints reused in shell_k4"}
  - {id: UI-4, t: "button skin material", blk: "owner-confirm (feel)", st: "options written 2026-10-07 (sub-ui issue 4)", opts: "A (rec) Wacker ELASTOSIL Film 2030 silicone film 300 um (+-5 %, compression set 5 %, glues with silicone adhesive) in a recess deepened to 0.30 (puck kit -0.05) / B 0.25 TPU film (easy bond, stiffer, creeps) / C moulded Sugru (no purchase, poor thickness control)", commit: "ed4e7dd", k4: "valid"}
  - {id: RPB-3, t: "body-side mic path", blk: "item:SAI-3, SAI-13", k4: "valid; SAI-3 unchanged; SAI-13 notch now 44.4 kHz (sim), sweep open"}

info_only:   # check WARNs that are tracked elsewhere, not work items
  - {id: CHK-PINS, t: "interfaces [pins] 3 known hazards (GB_N PB15, MIC_DATA PB4, TS PA2), ECR-0013 implemented"}
  - {id: CHK-SELFTEST, t: "interfaces [selftest] 5 skipped rules (design no longer has what they break)"}


# 2026-10-08 K4-REROUTE-R5: P and M re-placed + re-routed after 9ec84ae, 0 DRC / 0 unconnected (ECR-0020 update). Open: K4-C9-ESR (C9 0201 ESR<20 mOhm @3 MHz, C17 DC bias; Samsung weblib curve unreachable headless, same as PWR-I14), K4-SILK (K4 silk pass, silk_* warnings only).
# 2026-10-08 K4-C9-ESR attempt 2 (worker): LCSC reference-sheet PDFs fetched (CL03A225MP3CRNC wmsc .../2007201008_..._C318539.pdf, CL03A105MO3NRNC .../2401181241_..._C318540.pdf). Verified: both X5R, thickness 0.30+-0.09 (0.39 max, fits 0201 height budget), rated 10 V / 16 V, +-20%. NOT in them: DC-bias, ESR/impedance curves (spec sheets only). Samsung weblib/product.samsungsem.com return HTTP 500 headless; WebSearch finds no curve; Murata SimSurfing/TDK SEAT are JS tools. C9 ESR<20 mOhm@3 MHz and C17 bias remain UNVERIFIED. Closing needs owner-side KSIM/SPICE download (browser) or a Samsung FAE request; fallback if C9 fails: 2x 1u 0201 or C8-style 0402 (taller, check gap).
# 2026-10-08 K4-C9-ESR attempt 3 (worker): Murata equivalents identified, curves still unfetchable headless. C9 -> GRM033R61A225ME47D (LCSC C319184, 2u2 10 V X5R 0201, T 0.3+-0.09 = 0.39 max, stock 179060, $0.0301, Extended); C17 -> GRM033R61C105ME15D (C335102, 1u 16 V, stock 57177, $0.0737). SimSurfing is a JS app with no reachable static data; TDK 403; no TDK in JLC stock. No ESR/bias numbers, no pass/fail, gen.py unchanged. A-CAP-CURVES stays open (note added). Owner step: SimSurfing "download" for these two part numbers, or Samsung curves.
  - {id: K4-LIFT, rank_k4: 12, cls: hygiene, src: O34, t: "K4_RELIEF=lift default: rerun K4 checks, fix wire route, re-render k4-review", close: "ECR-0024", blk: none, st: "done 2026-10-08: pod 6.4x15.25x49.85, wires clash 0, strut 1.176, renders k4r_lift"}
