HrafnaValkyrja/ultrasonic/docs/research/drastic/V9-k4-board.yaml

# V9: shortest board for the K4 end-to-end pod (O33, 2026-10-08). AI-facing. Design study only: NO placement/routing/FreeRouting run; all L are [E] arithmetic on repo figures.
# Written 2026-10-08 by Claude (Opus 5.5 subagent). Conf: H measured, M derived, L inference. [V] = read this session, [T] = unverified (datasheet/quote not read).
meta:
  question: "min board length L for the K4 pod (cell 4.0/4.5max x 12 x 30 beside the board; pod L = 31.0 cell + board + 3.1 walls, V8 K4). Board H 12 (O27). Board zone T budget 4.5 inside walls (pod T 6.4 - floor 0.6 - lid 1.0 - gap 0.3), pod H 14.8."
  baseline: {board: "hw/pod/draft_r2/out/routed.kicad_pcb 30x12, 4L, DRC clean, 75 footprints, 195 pins, one face (B 54 % util)", dens: "V5-density.yaml"}
  glossary: {QFN48: "7x7 mm 48-pin leadless MCU package (STM32U575CIU6Q)", WLCSP-90: "wafer-level chip-scale MCU, 0.4 mm balls", B2B: "board-to-board connector", FPC: "flexible printed circuit", castellation: "half-cut plated holes on a board edge, soldered side-on to pads below", BM28: "Hirose BM28 0.35 mm-pitch B2B", DF40: "Hirose DF40 0.4 mm-pitch B2B", PDM: "pulse-density-modulated digital mic stream (mic U2 is digital, so no analogue ADC next to the SMPS; the exposure is MIC_VDD and acoustic/EM pickup)", SMPS: "MCU core switcher U1 + L1 (D11, the only allowed one)"}
  heights_mm: {src: "docs/system/reg-board.md, packages.md [V]", mic_U2_B: 1.08, L1: 1.0, SW1_F: 0.65, QFN48: "~0.6 [T]", C_0603: "~0.55", R_C_0402: 0.5, R_C_0201: 0.3, board: 0.8}
hard_floor:   # applies to ALL options
  rule_10mm: "L1/Q1/Q2 centres >= 10 mm from the mic port (port x 1.88 on the board front) = x >= 11.9; Q1/Q2/L1 courtyards ~1.5-2 mm -> L >= ~13.5. Today's measured port->nearest pad: L1 12.87, Q1 15.76 (reg-board.md). In-plane rule: a second board 2-3 mm up does not relax it."
  mcu: "QFN48 7x7 + 0.6 ring = ~8.2 mm of length; WLCSP 4.2 x 3.95"
  so_what: "no option goes below ~13.5-14 mm for QFN48. Option gains are bounded to 17 -> ~14: ~3 mm of a 51 mm pod (6 %)."
options:
  A_one_board_6L_two_face:
    L_mm: "17 (QFN48, shortest legal, V5 [H placement]); 15 with WLCSP-90 (needs via-in-pad on ~every ball; not reworkable, O18/O19). ECR-0019 (drops J12/R18/D6, ~2-3 mm2) does not break 17: 16 failed on SW1 axis + C21 in the MCU escape ring, not on area. [M]"
    pod_L_mm: "51.1 (17) / 49.1 (15)"
    stack_T_mm: "0.8 board + 1.08 mic (B) + 1.0 L1 or 0.65 SW1 (F) = ~2.9 [E]; 1.6 mm of the 4.5 budget unused"
    layers: "6 (planes GND + 3V0 kept, 2 inner signal). 4L load x2.46 at 17 mm = unlikely (V5). 6L x0.83 = likely [M]"
    jlc_build: "6L 0.8 mm is a standard JLC option (jlcpcb.com/resources/6-layer-pcbs: thickness 0.8/1.0/1.2/1.6/2.0, read 2026-10-08). Price: JLC headline '5 pcs 6L from $2' (jlcpcb.com/events/6-layer-pcb, coupon page, no 30x12 quote); secondary: 6L ~ +65 % over 4L (atlaspcb.com multilayer-cost article, 2026) [T]. For 2 pods a few boards: cost is noise vs the pod. Assembly quote with the real BOM NOT run (owner places orders, O21)."
    hand_rework: "worst: 195 pins on ~200 mm2, 0201s both faces, QFN48 on B between mic and L1; probing/rework only via the pads. Same as today's difficulty x ~2 density."
    noise: "same topology as today: port->L1 >= 12 mm, mic and MCU on one 17 mm board, 6L gives an extra inner-layer pair for mic return isolation. Unchanged risk class; tightest packing (MCU escape next to mic nets)."
  B_two_stacked_boards:
    partition: "P (power+dock): U3 charger BGA, U4 LDO, D4, D5, U6 ESD, RT1, C1-C4/C7/C14 bulk, dock wire pads J3-J5, cell leads, SW1 on its F (top) face. M (MCU+audio+output) : U1, L1, Y1, C5-C13/C15-C18, U2 mic (B, outer bottom, port through shell), Q1/Q2/R3-R6/R21 bridge, OUT_A/B pads J1/J2, SWD/test dots. Order top->bottom: SW1 | P | gap | M | mic port."
    inter_board_signals: "~16-18 [E, pin-contract.yaml not read for the final map]: GND x4, VSYS x2 (bridge 315 mA peak, parallel pins), +3V0 x2, USB_DP, USB_DN, CHG_INT, I2C SDA/SCL (charger, PB6/PA1), BTN, plus 1-2 spares. 20-pin B2B suffices; 24 if SWD is routed through."
    L_mm: "~14.5 (range 14-15.5) [E]: floor from hard_floor (13.5) + 4 faces at ~U 0.35 + B2B footprint (~5.4 x 2 mm on each inner face) ; M is the length-setting board (QFN48 + L1 >= 12 mm behind the port); P can be shorter and ends earlier. Gain vs A(17): -2.5; vs A-WLCSP(15): only -0.5."
    pod_L_mm: "48.6"
    layers: "4L + 4L. Per-board ~100-118 pins on ~174 mm2 = 0.57-0.68 pins/mm2 = x1.05-1.25 of today's 0.543 (proven 4L ceiling x1.00, 'likely' <=1.15, 'possible' 1.15-1.5, V5 bands) -> 4L 'possible', 6L on M only is the fallback [M-L]"
    connector_choice:   # JLC parts API 2026-10-08T01:53Z (tools/jlc.py)
      BM28B0.6-20DP/2-0.35V: {lcsc: C424566, class: Extended, stock: 25043, usd: 0.1985, mated_h_mm: "0.6 [T: from P/N, datasheet not read]", pitch_mm: 0.35, note: "ONLY one that fits: stack 0.8+0.6+0.8 + 1.08 mic + 0.65-1.0 = 3.9-4.3 <= 4.5 [E]. Gap parts limited to 0201 (0.3) / 0402 (0.5). Alt C3643381 $1.43 stock 57 (other variant). Plug and receptacle halves: confirm which P/N is which [T]. 0.35 mm pitch: no hand soldering, no hand rework; mating by tweezers/jig, retention ~N small [T]; hand-assembly = press fit only."}
      DF40C-20DP-0.4V: {lcsc: C424637, class: Extended, stock: 32994, usd: 0.3010, mated_h_mm: "1.5 [T]", pitch_mm: 0.4, note: "stack 4.8-5.2 > 4.5: FAILS thickness (+0.3..0.7 mm on pod T). Sturdier and cheaper; fallback if T may grow."}
      castellated_or_header_soldered: {mated_h_mm: "0.6-0.8 set by solder paste/pads [E]", note: "JLC will not assemble a stacked pair; owner hot-airs 12 mm edge, 16+ joints at 0.5 mm pitch on a 0.6 mm gap, solder bridging and no re-open without desolder. Strongest mechanically, worst serviceability. NOT recommended."}
      FPC_jumper: {part: "FH12-class 0.5 mm ZIF (e.g. C22459558, 10P, stock 2210, $0.0813, 2026-10-08)", note: "ZIF ~1 mm tall each + fold radius: stack > 4.5 unless boards sit side by side (then no length gain). Rejected for stacking."}
    stack_T_mm: "3.9-4.3 with BM28 [E]: fits the 4.5 board zone, so pod T stays 6.4 (no change). Margin 0.2-0.6 mm only, tolerance stack [T]."
    jlc_build: "two ordinary 4L 0.8 mm boards (cheapest known path), 2 small connectors; assembly both sides; the mate is a manual step by owner. 2 PCBs + 2 BOM lines instead of 1."
    hand_rework: "BEST for serviceability: unplug M from P to swap charger board or MCU board; each half has half the density. WORST for fragility: 0.35 mm B2B can't be hand-repaired, mating cycles limited [T], shock/pull-out in a worn pod [T]."
    noise: "L1/Q1/Q2 + mic all on M, so the SMPS is NOT separated from the mic; the P board only moves charger/LDO away. Gains: VSYS bridge pulses cross the B2B (needs 2 pins + local 22 uF C14 on M) ; MIC_VDD stays on M. New risks: B2B contact resistance on VSYS (bridge 315 mA, ~2 x 30-50 mohm [T]) ; GND return across 4 pins; USB D+/D- impedance over the B2B (full-speed only, tolerant). Net: neutral to slightly worse than A."
  C_rigid_flex_folded:
    L_mm: "~13.5-14 [E] (two rigid halves folded 180 degrees, flex tail ~2-3 mm fold radius, same floor as B with no B2B footprint: -0.5 vs B)"
    pod_L_mm: "~47.5"
    stack_T_mm: "~3.7 [E] (no connector gap, fold radius sets 1.0-1.5 gap) "
    layers: "rigid 4L/6L + 2L flex core [T]"
    jlc_build: "NOT BUILDABLE AT JLC: 'rigid-flex PCBs are not yet supported' (JLC capabilities/blog search 2026-10-08; also miniaturization-prelim.md BL-5 and MZR-02 '[V flex FAQ 2026-10-03]'). JLC makes 1-4L FPC with FR4/PI stiffeners only (jlcpcb.com/capabilities/flex-pcb-capabilities, read 2026-10-08), which BL-5 already rejected (SW1 needs rigid back, stiffener returns the thickness). Other fabs: quote not obtained [T]; expect much higher NRE, JLC assembly lost, and parts sourced by hand."
    hand_rework: "no connector to unplug; one failure scraps the whole assembly; fold is a static bend (fatigue ok) but unserviceable. Contradicts O19 serviceability."
    noise: "same as B."
    verdict: "REJECT: saves 0.5 mm over B but loses the JLC process and serviceability."
compare:   # L mm | pod L | T board zone | layers | JLC | rework | noise
  A: {L: 17, pod_L: 51.1, T: 2.9, layers: 6, jlc: "yes, 1 board", rework: "poor, dense", noise: "baseline", risk: "known placements; 6L routing unproven (V5 open item)"}
  A_wlcsp: {L: 15, pod_L: 49.1, T: 2.9, layers: 6, jlc: "yes, via-in-pad cost/capability unchecked", rework: "worst (no BGA rework/probe)", noise: "baseline", risk: "synthetic ballout (V5)"}
  B_bm28: {L: 14.5, pod_L: 48.6, T: "3.9-4.3", layers: "4+4", jlc: "yes, 2 boards, cheap", rework: "best serviceability, fragile 0.35 mm B2B", noise: "same-or-slightly-worse", risk: "stack margin 0.2-0.6 mm; no placement run yet"}
  C: {L: 14, pod_L: 47.5, T: 3.7, layers: "rigid-flex", jlc: "NO", rework: "none", noise: "same as B", risk: "not buildable at JLC"}
recommendation:
  pick: "A (one 6L two-face board, QFN48, 17 mm, pod L 51.1) is the baseline. B (BM28 stack, ~14.5 mm, pod 48.6) is the length option if the owner wants -2.5 mm (5 %). Reject C. Do NOT take A-WLCSP: B gets within 0.5 mm of it without via-in-pad."
  why_blunt: "the 10 mm mic-to-switcher rule and the 7 mm QFN48 floor the board at ~14 mm in every option; two boards buy 2.5 mm for +1 board, 2 fragile connectors and a thickness margin of 0.2-0.6 mm. Length gain is real but small relative to the 51 mm pod; A has zero new mechanical interfaces. Owner decides (spec 0 rule)."
  owner_decision_needed: "is -2.5 mm pod length worth a 0.35 mm B2B and a split board? If yes, B with BM28."
open_items:
  - "placement trial of B (M and P outlines, place_r2 two-board variant) and of A with ECR-0019 applied, to replace these [E] lengths (lead session only; no autorouter by parallel agents)"
  - "read BM28 and DF40 datasheets (mated height, current, retention, mating cycles) and confirm plug/receptacle LCSC numbers [T]"
  - "JLC quote with real BOM for 4L vs 6L 0.8 mm 30x12 / 17x12 (owner places orders, O21); price figures here are headlines only"
  - "final inter-board net count from pin-contract.yaml after partition is chosen"
  - "part heights not yet read: QFN48, C14 0603, U3 BGA (assumed <= 0.6)"
integration_map_crosscheck: "read-only research, no ECR; tools/plm.py impact not run. If B adopted: affects sub-power (VSYS across B2B), sub-dock-usb (D+/D- across B2B, ECR-0019 Rd at dock head), sub-ui (SW1 moves to P face), sub-audio-in (mic stays on M), reg-board (new outlines), reg-pod-body/physical (board zone T 3.9-4.3), rail-budget (B2B series R on VSYS); if A with ECR-0019: reg-board length only."
src: ["V5-density.yaml", "V8-thin-long.yaml K4", "docs/system/reg-board.md", "docs/research/mini/packages.md", "miniaturization-prelim.md BL-5/MZR-02", "tools/jlc.py 2026-10-08T01:53Z", "jlcpcb.com/resources/6-layer-pcbs", "jlcpcb.com/events/6-layer-pcb", "jlcpcb.com/capabilities/flex-pcb-capabilities", "atlaspcb.com multilayer-pcb-cost-scaling-optimization (secondary)"]
B_plus_noise:   # 2026-10-08 Claude (Opus 5.5 subagent). Sim: sim/noise/vertical_bplus.py (run_l2 reused unchanged, geometry hooks patched). Board: draft_r2 routed. H measured-by-model, all geometry/leak numbers [E] assumptions.
  rerun_2026_10_08_partition_v2:   # Claude (Opus 5.5 subagent), after the d2a70d9 review flaw (VLXSMPS/VDD11 crossed the B2B)
    partition: "ECR-0020 rev 2: P (upper) = U1 + SMPS (L1, C7, C8/C9) + charger + LDO + bridge + dock + button = ALL aggressors F01/F02; M (lower) = mic U2 + C13 only. B2B = BM28 10-pin: MIC_VDD, MIC_CLK, MIC_DATA + 7 GND. No switching node, no bridge or SMPS current crosses."
    result: "sim/noise/vertical_bplus.py re-run unchanged (fenced 3G), all 7 cases bit-identical to the table below: the model already puts OUT_A/OUT_B/VLXSMPS at the worst alignment over MIC_VDD, so moving U1 and L1 together onto P changes no aggressor position. Magnetic F02 nominal 62.7/42.7/12.7 dB (nom/pes/worst PSRR), pessimistic leak 54.8/34.8/4.8 dB (below the 10 dB sign-off), planes-ignored bound -7.3 dB worst PSRR. Verdict unchanged: PASS nominal, MARGINAL pessimistic-corner."
    new_victim_not_in_model: "MIC_VDD (PA5 -> mic) and MIC_CLK/DATA now run on P from U1 to the BM28, i.e. IN-PLANE with L1 on the same board, then up the connector. The in-plane baseline (today's routed board, MIC_VDD trace ~2.4 mm from the VLX trace) is 68.6/48.6/18.6 dB, so the in-plane run is fine only if the P layout keeps the routing as good as draft_r2; the vertical hop through the connector is the 62.7/42.7/12.7 case. Layout rule for P: route PA5/PB3/PB4 away from VLXSMPS/L1, on the side of U1 facing the connector, GND-guarded; check with the same sim on the routed P board."
    contact_risk_retired: "The 0.3 A [T] BM28 contact no longer carries SMPS ripple (VLXSMPS/VDD11 gone from the connector). Largest contact current is the ~1 mA mic supply. Conduction path A6 (A01 SMPS-input 15.3 dB) is now entirely on P, so the connector cannot worsen it; the open conduction item shrinks to the mic ground return through 7 GND contacts."
  question: "Option B+ (power board with L1/Q1/Q2 2-3 mm directly above the mic region, both boards' GND planes between): does mic/ADC noise stay in budget vs today's in-plane 12.87 mm port-to-L1 case?"
  verdict: "PASS on nominal assumptions, MARGINAL only under the pessimistic-leakage x worst-PSRR corner. Field-coupled mic-supply spur (F02 SMPS, the worst field line): margin vs tone limit (floor-10 dB) 42.7 dB at pessimistic PSRR (today in-plane 48.6, delta -5.9 dB); 12.7 dB at worst-case PSRR roll-off (today 18.6; sign-off needs >= 10). Pessimistic leakage: 34.8 / 4.8 dB (below the 10 dB sign-off). Planes ignored (bound): 22.7 / -7.3 dB, so the planes are doing the work and must be real. Bridge (F01) and PDM-line pickup stay >= 83 dB (digital 100 mV limit). Verdict margin: +6 dB worse than today, +12.7 dB absolute (worst PSRR), nominal."
  method:
    reuse: "sim/noise couple.py run_l2: same victims (MIC_VDD tone chain with alias+PSRR+mic floor, MIC_DATA, MIC_CLK), same aggressor waves (aggressors.yaml F01 bridge OUT_A/OUT_B, F02 SMPS VLXSMPS 3 MHz triangle 108 mA pp, 3 V edges 3 ns), same limits (tone limit floor-10 dB = -112.3 dBFS; digital 100 mV). Baseline = unmodified run on routed.kicad_pcb (sim/noise/out_r2/budget.json)."
    change: "aggressor nets translated in-plane to sit directly over the MIC_VDD net centroid (worst alignment) and lifted to height h above the lower board's B.Cu; victim traces keep their real routed geometry. Mutual L from 3-D filament distance (free); mutual C from free-space filaments."
  assumptions:
    A1_stack: "lower board B.Cu (mic face) = 0; lower F.Cu 0.8; gap 0.6 (BM28); upper board bottom 1.4; upper top 2.2. L1 winding centre ~0.5 above its board face -> 2.7. Switch-node/bridge traces on upper top: h = 2.2. Mic on the lower board outer (B) face (mic 1.08 mm does not fit the 0.6 gap) [T: mic face and port path not decided]."
    A2_plane_shield_H: "each GND plane screens B as a thin sheet: T_i = 1/sqrt(1+(f/fc_i)^2), fc_i = Rs/(pi mu0 d_i), Rs = 1.13 mohm/sq (model value, ~15 um Cu), d_i = source-to-plane distance. Plane 1 = upper board GND directly under the source (d1 0.15 for traces, 0.65 for L1 winding), plane 2 = lower board In1 GND (d2 = h - 0.45). fc: 1.9 MHz / 0.18 MHz (traces), 0.44 / 0.14 MHz (L1). Two planes combined as a PRODUCT (independent sheets). Lower In2 +3V0 plane is NOT counted (bonus). Same interpolation as the in-plane model, an engineering estimate not a field solve (+-10 dB model error stated in couple.py)."
    A3_leak_floor: "T_total = max(T1*T2, floor). floor = edge/aperture leakage (BM28 slot, via antipads, 12 mm wide planes): nominal 0.10 (-20 dB), pessimistic 0.25 (-12 dB), optimistic 0.03. ASSUMPTION; nothing measured. At 3 MHz and above the product is < 0.03, so the floor, not the plane physics, sets the result."
    A4_electric: "E field leaks only through apertures: Cm = leak x Cm_free, leak nominal 0.03 (the in-plane model's own Cm_image/Cm_free ratio), pessimistic 0.10, optimistic 0.01."
    A5_aggressor_current: "aggressor current taken uniform along the whole real VLXSMPS / OUT_A / OUT_B net with no return path in the model = upper bound on the loop (couple.py docstring). Real L1 DFE201610E is a metal-composite semi-shielded part; this is conservative."
    A6_not_modelled: "conduction through the BM28 (VSYS/GND contact R + pin L), vias, the L1 network itself. The worst conduction line today is A01_SMPS_IN at 28 MHz alias, 15.3 dB at worst PSRR (budget.json LN-M01): it is a conduction problem the connector can make WORSE and this run does not cover it."
  results_dB_margin:   # margin to tone limit, MIC_VDD chain F02 SMPS tone; nom / pes PSRR / worst PSRR (rolloff); digital lines = sum-of-harmonics margin vs 100 mV
    in_plane_today_12p87:   {H_magnetic: "68.6 / 48.6 / 18.6", E_electric: "101.5 / 81.5 / 51.5", PDM_data_H_E: "77.0 / 92.7", PDM_clk_H_E: "76.7 / 104.5", bridge_to_PDM: ">= 103"}
    Bplus_traces_h2.2:      {H_magnetic: "62.0 / 42.0 / 12.0", E_electric: "98.0 / 78.0 / 48.0", PDM_data_H_E: "73.7 / 78.7", PDM_clk_H_E: "76.9 / 89.4", bridge_to_PDM: ">= 93"}
    Bplus_L1_h2.7_nominal:  {H_magnetic: "62.7 / 42.7 / 12.7", E_electric: "98.8 / 78.8 / 48.8", PDM_data_H_E: "74.6 / 79.3", PDM_clk_H_E: "77.2 / 89.7", bridge_to_PDM: ">= 94"}
    Bplus_L1_h2.7_pessimistic_leak: {H_magnetic: "54.8 / 34.8 / 4.8", E_electric: "88.3 / 68.3 / 38.3", PDM_data_H_E: "66.6 / 68.8", PDM_clk_H_E: "69.2 / 79.2", bridge_to_PDM: ">= 83"}
    Bplus_L1_h2.7_optimistic_leak: {H_magnetic: "73.2 / 53.2 / 23.2", E_electric: "108.3 / 88.3 / 58.3"}
    Bplus_planes_ignored_bound: {H_magnetic: "42.7 / 22.7 / -7.3", E_electric: "68.3 / 48.3 / 18.3", PDM_data_H_E: "54.6 / 48.8", PDM_clk_H_E: "57.2 / 59.2", bridge_to_PDM: ">= 63"}
  magnetic_vs_electric:
    magnetic: "dominates everywhere. M_free(F02 -> MIC_VDD) -0.54 nH at h 2.7 (today in-plane -0.34 nH, because the MIC_VDD trace already runs ~2.4 mm from the VLX trace, not 12.87 mm: the 10 mm rule protects the PORT, not the VDD routing). SMPS H field at 3 MHz harmonics sits above the plane corner fc, so the sheet attenuation is real (T 0.16 -> 0.007 for two planes) but is floored by leakage (A3). Magnetic needs the planes continuous under L1 and over the mic region, with the BM28 slot offset away from the L1 shadow."
    electric: "78.8 dB at pessimistic PSRR (today 81.5): not a concern; any continuous plane kills dV/dt coupling; margin set by the aperture leak assumption A4. The 3 ns / 3 V switch-node edge puts its energy at 30-100 MHz where the plane image limit applies."
  vs_in_plane: "-5.9 dB in magnetic margin on the dominant line (aggressor 2.35 mm from the VDD trace today vs 2.7 mm vertical but with the shielding floor at -20 dB instead of in-plane T=0.12 at 8 MHz). The 10 mm rule is therefore not a noise-physics requirement for B+ on this model; it can be relaxed in the vertical case ONLY if both GND planes are continuous across the mic + L1 footprint (DRC/review item)."
  caveats:
    - "Margin to PSRR sign-off is thin in the pessimistic corner (4.8 dB < 10). Retire with a bring-up measurement (LN-V*) on a real stack; do not claim better than the model error (+-10 dB)."
    - "Conduction through BM28 not modelled (A6): the worst existing line (A01 conduction 15.3 dB) can only move down with extra series L/R in GND/VSYS. Needs >= 4 GND pins and a local 22 uF at the lower board (already in the B options)."
    - "Acoustic coupling of SMPS mechanical (inductor/MLCC piezo) noise into the mic port 2-3 mm away is NOT electrical and NOT in this model; MLCC and L1 audible-band buzz at load steps is a real B+ risk [T]. Mitigate: no MLCC on the switch/VSYS loop above the port, or soft-mount; decide by a tap test."
    - "Mic is 1.08 mm, gap 0.6: the mic must be on the lower board's OUTER face; then the port opening is on the outer side and the planes shield the mic die from the upper board. If the mic sat inside the gap the shielding would drop out."
  recommendation: "B+ is acceptable on noise if (a) continuous GND on upper In1 and lower In1 under/over L1 and the mic, (b) >= 4 GND pins on BM28 near L1, (c) mic on the outer lower face, (d) acoustic tap test of L1/C buzz before freezing. Then board L ~11 mm is not noise-blocked. Owner decides (spec 0)."
  src: ["sim/noise/vertical_bplus.py (run 2026-10-08, fenced 3G)", "sim/noise/couple.py, aggressors.yaml, params.yaml, out_r2/budget.json (baseline)", "docs/system/reg-board.md l.115, l.144 (12.87 mm, MP-01 rule)"]
  integration_map_crosscheck: "research-only, no ECR; plm impact not run. If B+ adopted: reg-board (retire/relax MP-01 10 mm for the vertical case, new outline), sub-power (VSYS+GND across BM28), rail-budget, sub-audio-in (mic outer face), physical (stack 3.9-4.3)."
k4_rebalance_2026_10_08:   # Claude (Opus 5.5 subagent). ECR-0020 rev 3. [E] arithmetic, no placement run. Courtyards from draft_r2/out/routed.kicad_pcb (mz2 packages), x1.3 routing, 2 faces, H 12 (gen.py area()).
  problem: "rev 2 put 51 parts on P and only the mic on M: P as long as a single board, B+ gained nothing in length."
  P_upper: {parts: 31, courtyards_mm2: 148.6, L_by_area_mm: 8.0, L_face_bound_mm: "~11.5 (U1 QFN48 65.6 mm2 + decoupling ~106 mm2 on one face)", content: "U1, Y1, L1/C7/C8/C9, bridge Q1/Q2 + shunt + C14, SWD/test pads, J1/J2, J21"}
  M_lower: {parts: 23, courtyards_mm2: 116.9, L_by_area_mm: 6.3, L_geometry_mm: "~9 (mic 4.1 + SW1 3.1 + dock strip 8 x 2.4 + BM28 2.6)", content: "mic U2/C13, BQ25180 + LDO, battery/ESD (D4/D5/U6), 4 own gold dock pads + 2 magnets (37 mm2 belly reserve), SW1, sense dividers, NTC, LED feed, cell pad, J20"}
  b2b: "BM28 30 contacts (16 signal/power, 14 GND); 20 do not fit (D+/D- pair + PDM trio need >= 8 GND); no switching node crosses; +3V0 on 3 contacts"
  K4_L_mm: "board stack ~11.5 (P-limited), M ~9; target <= 11-12 met. Pod L ~ 31.0 cell + 11.5 + 3.1 walls = ~45.6 [E] (was 48.6 for the 14.5 mm B estimate)"
  caveats: "the 11.5 is a face-bound estimate, not a packed result; SW1 now on M's belly (button access on the belly face to check in shell_k4); cell - on the shared dock GND pad J4 needs a placement check; magnet size [T]; +3V0 contact drop 3 x ~50 mohm [T] under 0.33 A peaks (C14 on P covers the edge)"
k4_post_route_2026_10_08:   # Claude (Opus 5.5 subagent), commit after 0cf2de6. Boards: hw/pod/k4/routed_P/M.kicad_pcb (6L, DRC 0/0, M 23 parts + P 29 assembled, outline 15.5 x 12). No placement/routing touched.
  glossary: {PSRR: "power-supply rejection ratio of the mic", M_eff: "effective mutual inductance (nH) between aggressor and victim traces after plane screening", L1_body: "the 2.2 uH SMPS inductor modelled as one filament 0.5 mm off the board face"}
  noise:
    tool: "sim/noise/k4_noise.py (NEW; fenced 3G, ~10 s). Reuses couple.mutual_nH kernels and aggressors.yaml F01 bridge / F02 SMPS vs victims MIC_VDD/DATA/CLK on the REAL routed geometry of P (aggressors + the mic nets' MCU half) and M (mic half) in one 3-D stack (gap P-B to M-F 1.3 mm [E], cross-board leak floor 0.10 = vertical_bplus A3). Today's board is run through the same function, so the dB change is like for like; it is applied to out_r2/budget.json margins. Output sim/noise/out_k4/k4_noise.json."
    why_not_extract_py: "extract.py/budget.py/pcbgeom.py assert 4 copper layers and ONE board; the MIC_VDD conduction network (U1 PA5 -> BM28 -> C13/mic) spans two boards and is not built. So conduction is NOT covered (K4-CONDUCT stays open)."
    result_margin_dB_F02_smps_on_mic_supply:   # tone chain, nominal / pessimistic PSRR / worst-case PSRR roll-off. sign-off needs >= 10 at worst
      today_draft_r2: [68.6, 48.6, 18.6]
      K4_traces_only_signed: [64.4, 44.4, 14.4]
      K4_traces_only_abs_bound: [59.4, 39.4, 9.4]
      K4_with_L1_body_signed: [56.9, 36.9, 6.9]
      K4_with_L1_body_abs_bound: [54.6, 34.6, 4.6]
    result_digital_lines_vs_100mV_limit: "F02->MIC_DATA 56.7-59.2 dB (today 77.0); F02->MIC_CLK 56.4-58.1 (today 76.7), L1-body case up to 81 signed; F01 bridge->DATA 82-87 (today 105), ->CLK 83-91 (today 103). All >= 56 dB: PASS with >= 50 dB spare."
    electric_bound: "not simulated: even with NO plane screening (full Cm_free instead of Cm_image, -30 dB on F02->MIC_VDD, budget.json l2_pairs) the electric margins stay 71 / 51 / 21 dB (>= 10): PASS as a bound."
    verdict: "PASS nominal and pessimistic PSRR on every line; MARGINAL in the worst-case-PSRR corner on the one dominant line (F02 SMPS 3 MHz -> MIC_VDD): 4.6-14.4 dB vs the >= 10 dB sign-off, i.e. 4-14 dB worse than today's 18.6. Same corner as the B+ pre-layout estimate (12.7 / pessimistic-leak 4.8): the real geometry lands inside that band, not worse. Mechanism: the mic supply/clock/data now run 8-14 mm on P (F.Cu/In3) in plane with L1 and the bridge, and M's F.Cu mic traces face P's B.Cu switch node with no plane between them (gap 1.3 mm)."
    cheap_fix_candidates: ["keep MIC_VDD off P's B.Cu/In3 near VLXSMPS/L1 (re-route only if the owner wants the margin; not done here)", "bring-up measurement LN-V* retires the leak floor assumption", "ferrite/RC on MIC_VDD at the M end (C13 already there)"]
    assumptions: ["gap 1.3 mm between the boards [E: shell_k4 stack 4.3 is a placeholder block]", "6L stack = uniform dielectrics, 0.8 mm total [E: JLC 6L impedance page NOT read, K4-STACK6 open]", "uniform victim current (no network), L1 body 1 filament, boards aligned xy with no mirror", "cross-board only the aggressor board's planes are counted (conservative)"]
  checks:
    tool: "tools/checks/k4_checks.py (NEW). interfaces.py/bom_check.py are single-board and read one netlist, dims_k4.py has no interface_facts(): run on one K4 board they FAIL on 'missing parts' (not defects). The new tool checks both boards vs their own pod_k4_X.net / bom_jlc_X.csv."
    result: "11/11 PASS: refs P 37 / M 37 (incl. J21/J20); nets 147 + 105 pads, 0 differ; JLC BOM 29 + 25 designators == assembled parts; 72 distinct parts, no duplicates; BM28 J20/J21 34/34 contacts, 0 net differences; outline 15.5 x 12.0 == dims_k4.STACK_L; U2 NPTH (1.75, 6.00) == dims_k4.MIC."
    not_covered: "part heights vs the stack bands (K4-HEIGHTS), clamp/VHB bands, SW1 plunger offset, pin-contract + rails (interfaces.py [pins] [rails]) on the K4 pair; bom_check values/stock/identity on the K4 pair (the single-board run gave PASS footprints, fp-library, nets, identity, cost-bom; WARN stock-lock U1 C5271013 stock 26 at 2026-10-07)."
  propose_k4_default:   # proposal only, hw/current.yaml NOT edited
    gate: "noise PASS/MARGINAL (worst corner 4.6-14.4 vs 10) + checks 11/11: do NOT call it a clean pass; owner decides whether the worst-PSRR corner needs a re-route first."
    changes_if_adopted:
      - "hw/current.yaml: move the k4 block to the top (id k4, ecr ECR-0021, O33), demote phase2 to a variant (keep as 'reference' neighbour). The pointer has ONE board/netlist/bom key: K4 needs board_P/board_M + netlist_P/M + bom_P/M (tools/current.py PATH_KEYS) or every consumer keeps seeing only M."
      - "single-board consumers break or read half the pod: sim/noise (extract/budget/pcbgeom: 4L + one board), tools/checks/interfaces.py (needs dims_k4.interface_facts() + two boards), bom_check.py (refs/jlc-bom FAIL on one board), docs/build/bom.py, pod_mass.py, shell + acoustic scenario (phase2_r2 reused), render scripts."
      - "docs/system (ECR-0018 -> ECR-0020/0021): reg-board.md, sub-power/dock-usb/ui/audio-in/output.md, physical.md, 00-whole.md, integration-map, rail-budget, pin-contract.yaml, vcrm; ECR-0020/0021 proposed -> approved (owner)."
      - "owner decisions still open: ECR-0020/0021 approval, worst-PSRR noise corner, K4-BM28-DS contact R now read: signal <=100 mohm, power <=30 mohm max, K4-HEIGHTS, K4-STACK6."
    recommendation: "wait for K4-HEIGHTS + K4-STACK6 (both fast), then switch; making k4 default today would leave interfaces.py/bom_check/noise half-blind."
k4_mic_filter_2026_10_08:   # Claude (Opus 5.5 subagent). Follows k4_post_route_2026_10_08; ECR-0020 rev 5. P placement/routing not touched.
  glossary: {R30: "33 ohm series resistor on M between MIC_VDD (from P's PA5 via BM28 pin 6) and the mic-local net MIC_VDDF", MIC_VDDF: "filtered mic supply: U2 VDD + C13", K4-STACK6: "backlog item: record the JLC 6-layer 0.8 mm stack-up"}
  stackup_K4_STACK6: "jlcpcb.com/impedance (headless Chromium, read 2026-10-08): 6L stack-ups published only for 1.2/1.6/2.0 mm (e.g. JLC06161H-1080: Cu 0.035 / 1080 0.0764 / core 0.55 / 7628 0.2104 / core 0.55 / 1080 0.0764 / Cu 0.035, inner Cu 0.0152; eps core 4.6, 7628 4.4, 3313 4.1, 1080 3.91, 2116 4.16). 0.8 mm 6L is orderable (jlcpcb.com/resources/6-layer-pcbs; FR4 0.4..2.0, tol +-0.1 mm under 1.0 mm, jlcpcb.com/capabilities) but NO 0.8 mm build is published: dielectric split unknown, bounded in k4_noise.py by --stack uniform|thin_outer (0.2 dB apart)."
  model_corrections: "k4_noise.py c5899c1 did not mirror P (stack (x, 12 - y)) and put P file F.Cu on top; place_k4 says P file F is the INNER face. Fixed (--legacy-noflip reproduces the old geometry). Gap 0.6 (BM28 mated, [T]) instead of 1.3."
  result_F02_smps_to_mic_vdd_worst_PSRR_corner_dB:   # abs-bound margin with the L1 body, sign-off >= 10
    no_filter_corrected_model: {uniform_gap0.6: 8.0, thin_outer: 7.7, uniform_gap1.3: 8.1, signed_default: 10.6}
    with_R30_33R_C13_50nF_att_floor_20dB: {uniform_gap0.6: 26.4, thin_outer: 26.2, uniform_gap1.3: 26.5, thin_outer_gap1.3: 26.3, signed_default: 29.7, wrong_legacy_geometry: 19.8}
    filter_att_db_ideal_3_6_9_27_MHz: [-29.9, -36.1, -39.9, -53.4]
  drop: "33 ohm x 1.35 mA (params.yaml mic.r_load 2.2k at 3 V) = 45 mV < 50 mV; datasheet ~1 mA gives 33 mV"
  parts: "R30 Yageo 0402WGF330JTCE C25105 Basic 0402, stock 1,868,836 (JLC parts API 2026-10-08T08:03Z); C13 unchanged 100 nF 0201 C76934. A 1 uF 0402 (C52923 Basic, stock 8.35 M same date) was tried and does not fit: F-face gap budget (0.6 mm total vs P Q1 0.37 + 0.5) and B-face keep-out."
  layout: "M place PASS (place_k4 --L 15.5 --fine --cx 9.8), route_k4 M + close_gaps: 0 unconnected, 0 DRC errors (kicad-cli, persisted JLC 6L rules), ERC 0 errors both. 27 parts on M incl. J20."
  stack6_rerun_2026_10_08: "K4-STACK6 closed. Order = JLC 6L 0.8 mm (jlcpcb.com/resources/6-layer-pcbs, jlcpcb.com/impedance read 2026-10-08), symmetric split assumed, no impedance control. k4_noise.py re-run both bounding splits (--stack uniform / thin_outer): F02->MIC_VDD at 3 MHz, abs-bound margin with filter 34.8 / 34.9 dB, unfiltered 21.4 / 21.4 dB (dominant tone only); worst-corner summary above 26.4 / 26.2 dB; split spread <= 0.2 dB at every f. Verdict unchanged (>= 10)."
  verdict: "worst-PSRR corner margin 26.4 dB (>= 10 in every corner and case). K4-HEIGHTS and K4-CONDUCT stay open; the 20 dB filter floor is an assumption until bring-up LN-V* measures MIC_VDDF vs MIC_VDD."
  integration_map_crosscheck: "touches SUB-AUDIO-IN (mic supply path, +R30), REG-BOARD (M placement), SUB-PROCESSING (PA5 now drives 33 ohm + C13 in series; 1.35 mA, 45 mV drop, no firmware change). Spec/MVP untouched."
integration_map_crosscheck_k4_post_route: "read-only analysis + two new tools; no design file edited. Touches reg-board (post-route evidence), sub-audio-in (mic noise margin in the worst corner), sub-power (conduction still open). plm status 0 suspect / 0 stale."

k4_heights_2026_10_08:   # Claude (Opus 5.5 subagent). Closes backlog K4-HEIGHTS (evidence). sim/checks/k4_heights.py (fenced 3G, <10 s) -> sim/out/k4_heights.json. No placement/routing touched, no shell edit.
  glossary: {VHB: "3M Very High Bond foam tape (the 0.25 mm layer that hangs the stack on the lid)", BM28: "Hirose 0.35 mm-pitch board-to-board connector pair, mated 0.6 [T]", file F/B: "KiCad layer of the part in routed_P/M.kicad_pcb", notch: "P Edge.Cuts cutout over the mic", RSS: "root-sum-square of independent tolerances"}
  physical_stack_y: "lid inner 9.70 | VHB 0.25 | M file-B = LID face (SW1 in lid pocket, C21, U6, C15/C18, R20/R30, 0201s, wire pads) 9.45 | M 0.8 | M file-F inner 8.65 (U2, U3, D4/D5, U4, C16/C17, J20) | BM28 gap 0.6 | P file-F inner 8.05 (Q1, C9, R21, 0201s, J21) | P 0.8 | P file-B OUTER 7.25 (L1, C4/C7/C14, U1, Y1) | floor 4.90. Source for which face is which: hw/pod/place_k4.py docstring + shell_k4.py (SW1 and mic port on the lid face)."
  heights_max_mm: {L1: "1.00 (L0806 lib name H1.0, V9 [V])", C4_C7_C14_C21_0603_10_22uF: "0.90 [T: Samsung 0.8 +-0.1 from memory, datasheet not fetched]", U1_QFN48: "0.60 [T: ST UFQFPN48 A max, not fetched]", Y1: "0.60 [T]", U2_mic: "1.08 [V]", SW1: "0.65 (dims_k4)", U6_SOT553: "0.60 [T]", C9_C15_C16_C17_C18_0402_cap: "0.55 [T]", R20_R21_R30_0402_res: "0.40", U3_BQ25180: "0.50 [T]", D4: "0.50 [T]", D5_U4_Q1_Q2: "0.40 [T/V]", 0201: "0.28 R / 0.33 C [T]", BM28_pair_mated: "0.60 nominal [V: Hirose BM28 Series Catalog (Aug 2019, 8 p), fetched 2026-10-08 from https://datasheet.lcsc.com/lcsc/C424571.pdf (curl, UA+Referer lcsc.com; byte-identical for C424570); hirose.com 403, www.lcsc.com/datasheet/ returns JS shell, p1 title + product-number field 3 stacking height 0.6 mm; no tolerance printed, the +-0.05 stays [T]]", boards: "0.8 +-0.1 (jlcpcb.com PCB thickness FAQ, read 2026-10-08)", VHB: "0.25 +-15 % (3M TDS 2024-09)", cavity_print: "+-0.1 [T, docs/build/tolerances.md lid +-0.1]", models_note: "the KiCad 3D models for these parts are placeholders (several 0.4) and were NOT used"}
  floor_side_P_outer: {tallest: "L1 1.0", nominal_clear_mm: 1.35, rss: 1.14, worst_case: 0.86, verdict: "PASS with 0.86 worst. The 4.5 mm board zone is NOT the constraint: the real stack is 2.2 (2 boards + gap) + 1.0 (L1) = 3.2, so 1.3 mm of the zone is free on the floor side (dims_k4 STACK_T 4.3 is a placeholder block)."}
  inner_gap_0p6: {checked: 24, fail_worst: 0, fail_nominal: 0, tightest: "C16/C17 (M, 0.55) and C9 (P, 0.55) = 0.00 worst, 0.05 nominal; U3/D4 0.5 = 0.05 worst; U2 1.08 sits exactly in the P notch (courtyard 0.12..3.38 x 3.21..7.29 == notch rect), no P copper over it; no M part sits under a P part", verdict: "PASS but ZERO worst-case margin on three 0402 1 uF/2.2 uF caps; MLCC thickness tolerance is [T]. Cheap margin: move C16/C17/C9 to 0201 or accept, and read the cap datasheets (C23733, C52923, C107369)."}
  lid_side_M_file_B: {vhb_gap_mm: 0.25, tol_lin: 0.138, tol_rss: 0.107, fail: "12 of 12 parts fail nominal AND worst (SW1 excluded, it has the lid pocket): C21 0.9, U6 0.6, C15/C18 0.55, R20/R30 0.4, J4 wire pad 0.4, C13 0.33, RT1/R10/R15/R16 0.28 vs 0.25 gap", verdict: "FAIL. A flat 1.0 lid over a 0.25 VHB sheet clears nothing on the lid face except bare pads. This was invisible while the stack was a placeholder block. Also: the wire pads J4/J5/J7/J8/J9 are on this face, but dims_k4.wire_routes() runs the wires at Y_B - 0.1 (the inner face): inconsistent, to be settled with this fix."}
  fix_options:
    A_lid_ledge_rec: "Print a perimeter ledge on the lid underside (height 0.84, ~0.5 wide, on a part-free edge band [T: not checked against the courtyards]) and put the VHB on its tip: lid gap 1.09, all 12 parts clear with 0.05 spare, wires and solder domes fit. Floor side after: 0.51 nominal / 0.30 RSS / 0.02 worst (L1 vs floor). Pod T 6.4 unchanged, pod L/H unchanged. Costs: puck +0.84 (PUCK_L, kit), mic duct gets a 0.84 printed tube round the port with the VHB ring on its tip (acoustic seal, K4 acoustic scenario must be re-run), a part-free bond band on M's lid face."
    B_A_plus_C21_to_0402: "As A but swap C21 (10 uF 0603, 0.9) to a 0402 10 uF (0.55): required gap 0.79, ledge 0.54, floor worst 0.32, nominal 0.81. Needs C21 re-sourced (it is also PWR-I14: 10 V class derating), M re-routed for the smaller land = placement/routing, so owner/next router pass."
    C_lid_pockets: "Recess the lid underside over C21/U6/0402s: needs 0.65+ deep into a 1.0 lid = 0.35 skin < 0.6 resin min wall: REJECT."
    D_move_parts_to_P_outer: "P outer has 1.3 mm free, so C21/U6/C15/C18 could live there: a re-placement of M and P: not in this item, and it breaks the mic-side isolation partition (ECR-0020)."
    rec: "A. Smallest change, no part or board edit, pod T unchanged; worst-case floor margin is thin (0.02), so B on the next router pass buys 0.3 more. If the owner prefers margin to a re-route: order boards at 0.8 +-0.1 (nothing tighter is offered), the budget above already assumes that."
  open: ["datasheets of the [T] heights not fetched (this item read none): U1, Y1, 0603/0402 MLCCs, U3, U4, U6, D4/D5, BM28 mated +-0.05 tolerance (catalog prints none; ask Hirose/customer drawing)", "ledge band vs M lid-face courtyards", "dims_k4 has no LID_STANDOFF parameter yet; shell_k4 still models VHB 0.25 flat: implement A in dims_k4/shell_k4 + puck/duct + acoustic re-run if A is approved"]
  integration_map_crosscheck: "read-only analysis, no ECR yet; tools/plm.py impact not run. If A adopted: reg-pod-body/physical (lid ledge, puck length, duct tube), reg-board (lid-face bond band, wire-pad face), sub-ui (SW1 puck), sub-audio-in (port seal, re-run acoustics); reg-board MP rules unchanged."
  swap_route_feasibility_2026_10_08: "swap-parts-no-lid-change at 0.1 mm margin is INFEASIBLE: lid-face max part h 0.012 mm (0.25 VHB - 0.138 tol - 0.1), 0201s are 0.28; gap max 0.45: C16/C17/C9/U3/D4 fail. Only fix A (lid ledge) or a re-partition clears it. sim/checks/k4_heights.py swap_route; ECR-0020."
k4_lid_ledge_2026_10_08:   # Claude (lead, Opus 5.5 subagent); ECR-0022; option B_A_plus_C21_to_0402 adopted by the lead
  glossary: {ledge: "printed frame on the lid underside that the board VHB sticks to, so the lid gap grows without the pod growing", C21: "10 uF VSYS capacitor of the charger", gap side: "the 0.6 mm BM28 mated gap between M inner face and P inner face"}
  c21: "Samsung CL05A106MP5NUNC C315248 10 uF 10 V X5R 0402, Extended, stock 390164 (JLC API 2026-10-08T08:22Z). Samsung spec sheet: T 0.50 +-0.20 = 0.70 max (NOT 0.55 as V9 assumed); Yageo 0402 10 uF is also class CD (0.5+-0.2): every 0402 10 uF is 0.7 max. Saves 0.2 vs 0603 0.9. 10 V class closes PWR-I14 direction (DC-bias curve itself still not read)."
  ledge: "LID_STANDOFF 0.70 (dims_k4), width 0.5, inset 0.2, notched 0.1 clear around J3 J5 J9 RT1 TP5; tube D2.4 round the port. Kept 73.5 % of band (38 mm, 19 mm2, 5 runs, shortest 2.05). Required gap 0.94 = 0.70 + 0.10 margin + VHB 0.0375 + lid 0.1."
  layout: "M place PASS, route 0/0, DRC 0 errors, ERC 0 errors."
  datasheet_heights_2026_10_08: {U1: "0.60 ST DS13737 Tbl154", Y1: "0.60 Epson", U4: "0.40 TI", U6: "0.60 TI", D4: "0.50 Nexperia", C16: "0.65 Samsung catalog", C17_C18: "0.60", C21: "0.70", R_0402: "0.40", R_0201: "0.26", C_0201: "0.33", BM28: "0.6 nominal; Hirose text gives NO mated tolerance (0.05 still [T])", unresolved_T: "U3 BQ25180 0.5 and D5 0.4 (outline drawings are images in the PDFs), C15 0.55, C9/C8 0.60 sibling row"}
  margins_worst_case: {lid: "+0.112 (C21)", floor: "+0.163 (L1; nominal 0.65, RSS 0.44)", gap: "FAIL: C16 -0.10, C17 -0.05, C9(P) -0.05, D4 +0.05, U3 +0.05 (target 0.10)"}
  gap_side_options: ["1 swap C16 4.7u, C17 1u to Samsung low-profile 0.33 parts (CL05A475MQ3LUN 6.3 V / CL05A105KP3LNN 10 V): M-only, ok; C9 is on P so C9 2.2u 10 V -> CL05A225KP3LRN 0.33 needs a P edit; D4/U3 then pass only at 0.05 (not 0.1)", "2 gap 0.6 -> 0.7 needs a different Hirose height, none in the BM28 0.6 family: re-partition", "3 accept 0 margin on 0402 caps (they touch the other board only if both boards are +0.1 thick and the BM28 is 0.05 short): NOT recommended"]
  noise: "k4_noise.py F02->MIC_VDD worst-PSRR corner with R30/C13: abs-bound margin 28.7 dB (>= 10 all corners); k4_checks 11/11 PASS."
  open: ["acoustic re-run, F gap 0.95 + tube", "SW1 press FEM on a 19 mm2 bond", "VHB bond area/peel with notched frame", "clash/tub/cell 0.14 mm3 in shell_k4 (cell vs tub, independent of the ledge; check)"]
  integration_map_crosscheck: "REG-POD-BODY, PHYSICAL, REG-BOARD, SUB-AUDIO-IN, SUB-UI, SUB-POWER; spec/MVP untouched; plm 0/0."
k4_bm28_ds_2026_10_08:
  src: "Hirose BM28 Series Catalog (Aug 2019, 8 p), fetched 2026-10-08 from https://datasheet.lcsc.com/lcsc/C424571.pdf (curl, UA+Referer lcsc.com; byte-identical for C424570); hirose.com 403, www.lcsc.com/datasheet/ returns JS shell"
  ratings: {current: "signal 0.3 A/contact (<=40 contacts), 2 power contacts 5 A", voltage: "30 V AC/DC", contact_R_max: "signal 100 mohm, power 30 mohm (20 mV 1 kHz 1 mA)", durability: "10 mating cycles (catalog Durability row)", temp: "-40..85 C operating", reflow: "250 C peak, max 2 cycles; hand 340 C 3 s", stencil: "80 um, 100 % aperture DS side; DP side 100 % signal, 80 % power", warpage: "0.02 mm max", shock: "450 m/s2 11 ms no discontinuity >1 us"}
  mating: {height: "0.6 mm stacking height", polarity: "none (catalog note 2: no polarity) so pin n mates pin n by geometry only", self_align: "+-0.3 mm guide ribs", force: "not printed in the catalog (customer drawing only)", note: "can disengage on drop; Hirose advises housings/cushioning, a 0.3 mm glass-epoxy or 0.2 mm steel stiffener under FPCs, no prying, no cleaning"}
  footprint_check: "30 signal pads + 4 shield tabs. DS (recept): rows +-0.80 x 0.41 long x 0.18 wide, pitch 0.35, B 4.90, tabs 0.53 wide at x +-3.16, y +-0.74: MATCH. DP (plug): rows +-0.59 x 0.615 x 0.15 wide (Hirose land 0.18 +-0.02: 0.03 narrow, left as is, conservative), inner gap 0.57 and outer 1.8 MATCH, tabs 0.52 x 0.40 at y +-0.32 (Hirose mask 0.33, PCB land 0.25, centre 0.32-0.40: oversize, harmless, left). Plug courtyard was +-0.42 in y (inside its own pads, body 1.5 wide): FIXED to +-0.90 in the library; no overlaps on routed_P J21."
  orientation: "place_k4 P-flip across long axis + plug rot 180: plug pad n at stack (-px, +py), recept pad n at (rx, ry): pads 1, 15, 16 verified same x and same row side, pin n to pin n OK"
  height_use: "GAP 0.6 consistent; tolerance +-0.05 remains [T]"

k4_conduct_2026_10_08:   # Claude (Opus 5.5 subagent). Closes backlog K4-CONDUCT (evidence). sim/checks/k4_conduct.py (fenced 3G, <5 s) -> sim/out/k4_conduct.json. No placement/routing/design file touched.
  glossary: {BM28: "Hirose 0.35 mm-pitch 30-contact board-to-board connector", contact_R: "resistance of one mated contact", +3V0/GND contacts: "pins 15, 30 + 4 power tabs 31-34 carry +3V0; 15 signal pins (even 2-28, 16-18) carry GND (gen.py BM28_PINS)", bound: "all aggressor line current assumed to cross the connector, zero credit for P-side C4/C14"}
  src: "Hirose BM28 catalog Aug 2019 (k4_bm28_ds above, fetched 2026-10-08): contact_R max signal 100 mohm, power 30 mohm; typical not printed. Aggressor lines/PSRR chain from sim/noise (aggressors.yaml 2026-10-02, params.yaml)."
  dc_drop: {case_all_contacts: "R_3V0 11.5 mohm + R_GND 6.7 mohm: 5.9 mV at the 326 mA peak, 1.8 mV at 100 mA mean", case_power_tabs_dead: "R_3V0 50 mohm: 18.5 mV peak, 5.7 mV mean (worst contact 0.163 A vs 0.3 A rating)", case_gnd_only_4_pins: "11.9 mV peak", verdict: "<= 19 mV of a 3.0 V rail (0.6 %); U1 VDD min 1.71 V, mic 1.64..3.6 V: irrelevant for headroom"}
  ac_to_mic_supply: {limit_dbfs_per_tone: -112.3, worst_margin_pessimistic_dB: {all_contacts: 27.2, power_tabs_dead: 17.3, gnd_4_pins: 21.1}, worst_line: "A08 LED PWM 25 kHz (6-19 uV rms); next A04 shaped noise (22-30 dB), A05 CPU hop (31-40 dB); SMPS/PDM/carrier lines fold to DC or out of the 20-96 kHz window after the CIC/RSFLT chain", divider_case: "P-side caps take part of the current; margin 0.4-1.2 dB better, so the bound is within 1.2 dB of the credited case"}
  tx_coherent_term: "transmit current 0.32 A FS through the loop makes 4.1 mV (all contacts) to 12.8 mV (tabs dead) at the transmit frequency = -102.7 / -92.8 dBFS if read as supply spur. It is coherent with the tx tone (a fixed gain/phase on the mic's own tx pickup, which is acoustically larger), not noise; check at bring-up with the echo-cancel reference."
  verdict: "PASS. Contacts do not threaten the mic budget: >= 17 dB pessimistic margin even with the power tabs dead; no need for more +3V0/GND pins. Open for bench: measured contact R (4-wire across a mated pair, E-step) and tabs 31-34 actually soldered/connected; the tabs counted as power contacts follow V9 [T] (Hirose catalog says 2 power contacts 5 A)."
  integration_map_crosscheck: "touches SUB-POWER (+3V0 across BM28), SUB-AUDIO-IN (mic supply conduction), REG-BOARD (BM28 pin map). No design change; assumptions: contact L not modelled (0.4 mohm at 400 kHz, small vs R); LDO Zout not in loop for the divider. plm status 0 suspect / 0 stale."


# O34 2026-10-08 (ECR-0024): pod L now 49.85 (lift default, cell to x 65.8); board length rule unchanged (STACK_L follows routed boards 15.5).
