HrafnaValkyrja/ultrasonic/hw/pod/place.py

"""Feasibility placement + autoroute of the pod board: does everything fit on 20 x 10 mm and route?

    source tools/env.sh && python3 hw/pod/place.py      # -> hw/pod/draft/*.kicad_pcb, drc.json, renders

This is a DRAFT to prove fit and routability. It is not the layout: the owner lays the real board
out in KiCad from pod.net (CLAUDE.md). Coordinates: x = 0 at the pod's front (mic end), running back
along the temple arm; y = 0 at the board's top edge. F (top) faces the pod's outer wall; B faces
the cell. The mic sits on B and ports outward through the board (§8 acoustic rules).
"""
from __future__ import annotations

import json
import os
import re
import subprocess
from pathlib import Path

import pcbnew

HERE = Path(__file__).resolve().parent
REPO = HERE.parents[1]
OUT = HERE / "draft"
OUT.mkdir(exist_ok=True)
mm = pcbnew.FromMM
W, H, CORNER = 20.0, 11.5, 1.0   # 11.5 mm: the pod's inner height is 12.4 mm (hw/mech/pod.py); 10 mm starved the QFN's escape

# (ref, x, y, rotation deg, side). Grouped by function; the bridge sits at the rear, far from the mic.
PLACE = {
    # ---- F (outer face): MCU square in the middle (a 45-degree QFN would be 10.7 mm tall)
    "U1": (10.0, 5.75, 0, "F"),
    # left strip: crystal on PC14/PC15 (pins 3/4), NRST, VDDA, VDD48 decoupling, SWD pads
    "Y1": (3.6, 3.45, 90, "F"), "C11": (5.3, 2.53, 90, "F"), "C12": (5.3, 4.83, 90, "F"),
    "C10": (5.3, 7.13, 90, "F"), "C5": (5.3, 9.43, 90, "F"), "C6": (4.3, 9.43, 90, "F"), "C1": (4.3, 7.13, 90, "F"),
    "TP1": (1.0, 1.15, 0, "F"), "TP2": (1.0, 2.99, 0, "F"), "TP3": (1.0, 4.83, 0, "F"),
    "TP4": (1.0, 6.67, 0, "F"), "TP5": (2.5, 6.79, 0, "F"),          # all 5 SWD pads together for a pogo jig
    # right strip: VDD25/VDD36 decoupling, SMPS (pins 20-23 at the bottom-right corner), button
    "C3": (14.6, 2.76, 90, "F"), "C4": (15.6, 2.76, 90, "F"), "C7": (15.0, 5.75, 90, "F"),
    "C2": (14.6, 8.74, 90, "F"), "C8": (14.6, 10.75, 0, "F"), "L1": (17.4, 9.89, 0, "F"), "C9": (17.3, 7.82, 0, "F"),
    "SW1": (18.3, 3.79, 90, "F"), "R1": (15.8, 0.92, 0, "F"),
    # ---- B (inner face, toward the cell)
    # front: mic, ports outward through the board; nothing on F over its port
    "U2": (2.2, 8.74, 90, "B"), "R2": (4.9, 9.89, 90, "B"), "C13": (4.9, 7.13, 90, "B"),
    # middle: charger, LDO, battery sense, pads
    "U3": (7.4, 3.45, 0, "B"), "C15": (4.8, 2.30, 90, "B"), "C16": (10.0, 2.30, 90, "B"), "R7": (7.4, 6.21, 0, "B"),
    "D3": (6.4, 8.28, 0, "B"),
    "U4": (11.2, 6.44, 0, "B"), "C17": (11.2, 4.49, 0, "B"), "C18": (11.2, 8.16, 0, "B"),
    "R8": (12.4, 1.84, 90, "B"), "R9": (13.4, 1.84, 90, "B"), "C19": (11.4, 1.84, 90, "B"),
    "J3": (6.9, 10.35, 0, "B"), "J4": (8.5, 10.35, 0, "B"), "J5": (10.1, 10.35, 0, "B"), "J6": (11.7, 10.35, 0, "B"),
    # rear: bridge, far from the mic
    "Q1": (15.6, 5.52, 0, "B"), "Q2": (18.4, 5.52, 0, "B"),
    "R3": (15.6, 3.68, 0, "B"), "R4": (15.6, 7.25, 0, "B"), "R5": (18.4, 3.68, 0, "B"), "R6": (18.4, 7.25, 0, "B"),
    "C14": (14.4, 10.24, 0, "B"), "D1": (16.9, 8.74, 0, "B"), "D2": (18.7, 8.74, 0, "B"),
    "J1": (17.2, 10.46, 0, "B"), "J2": (18.8, 10.46, 0, "B"),
    "R10": (17.0, 1.73, 0, "B"),
}


def _sexpr(txt):
    """Minimal S-expression reader for KiCad netlists: returns nested lists of strings."""
    toks = re.findall(r'\(|\)|"(?:[^"\\]|\\.)*"|[^\s()]+', txt)
    stack = [[]]
    for t in toks:
        if t == "(":
            stack.append([])
        elif t == ")":
            done = stack.pop(); stack[-1].append(done)
        else:
            stack[-1].append(t[1:-1] if t.startswith('"') else t)
    return stack[0][0]


def _find(node, key):
    return [c for c in node if isinstance(c, list) and c and c[0] == key]


def parse_netlist(path):
    root = _sexpr(Path(path).read_text())
    comps, nets = {}, {}
    for comp in _find(_find(root, "components")[0], "comp"):
        comps[_find(comp, "ref")[0][1]] = _find(comp, "footprint")[0][1]
    for net in _find(_find(root, "nets")[0], "net"):
        name = _find(net, "name")[0][1]
        nets[name] = [(_find(n, "ref")[0][1], _find(n, "pin")[0][1]) for n in _find(net, "node")]
    return comps, nets


def fp_lib(lib):
    if lib == "lcsc":
        return str(REPO / "hw/lib/lcsc/lcsc.pretty")
    return os.path.join(os.environ["KICAD10_FOOTPRINT_DIR"], f"{lib}.pretty")


def outline(b, inset=0.0):
    """Rounded rectangle on Edge.Cuts; `inset` shrinks it (routing only: FreeRouting ignores KiCad's
    copper-to-edge rule, so it routes inside an outline pulled in by that clearance)."""
    import math
    x0, y0, x1, y1, r = inset, inset, W - inset, H - inset, CORNER - inset
    V = lambda x, y: pcbnew.VECTOR2I(mm(x), mm(y))
    for (xa, ya), (xb, yb) in (((x0 + r, y0), (x1 - r, y0)), ((x1, y0 + r), (x1, y1 - r)),
                               ((x1 - r, y1), (x0 + r, y1)), ((x0, y1 - r), (x0, y0 + r))):
        s = pcbnew.PCB_SHAPE(b); s.SetShape(pcbnew.SHAPE_T_SEGMENT); s.SetLayer(pcbnew.Edge_Cuts)
        s.SetStart(V(xa, ya)); s.SetEnd(V(xb, yb)); s.SetWidth(mm(0.05)); b.Add(s)
    k = r * (1 - math.sqrt(0.5))
    for st, mid, en in (((x0, y0 + r), (x0 + k, y0 + k), (x0 + r, y0)),
                        ((x1 - r, y0), (x1 - k, y0 + k), (x1, y0 + r)),
                        ((x1, y1 - r), (x1 - k, y1 - k), (x1 - r, y1)),
                        ((x0 + r, y1), (x0 + k, y1 - k), (x0, y1 - r))):
        a = pcbnew.PCB_SHAPE(b); a.SetShape(pcbnew.SHAPE_T_ARC); a.SetLayer(pcbnew.Edge_Cuts)
        a.SetArcGeometry(V(*st), V(*mid), V(*en)); a.SetWidth(mm(0.05)); b.Add(a)
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
